calphool/TRS80MXS/eaglecad/modular_expansion_system_graphics_and_sound.board.pdf

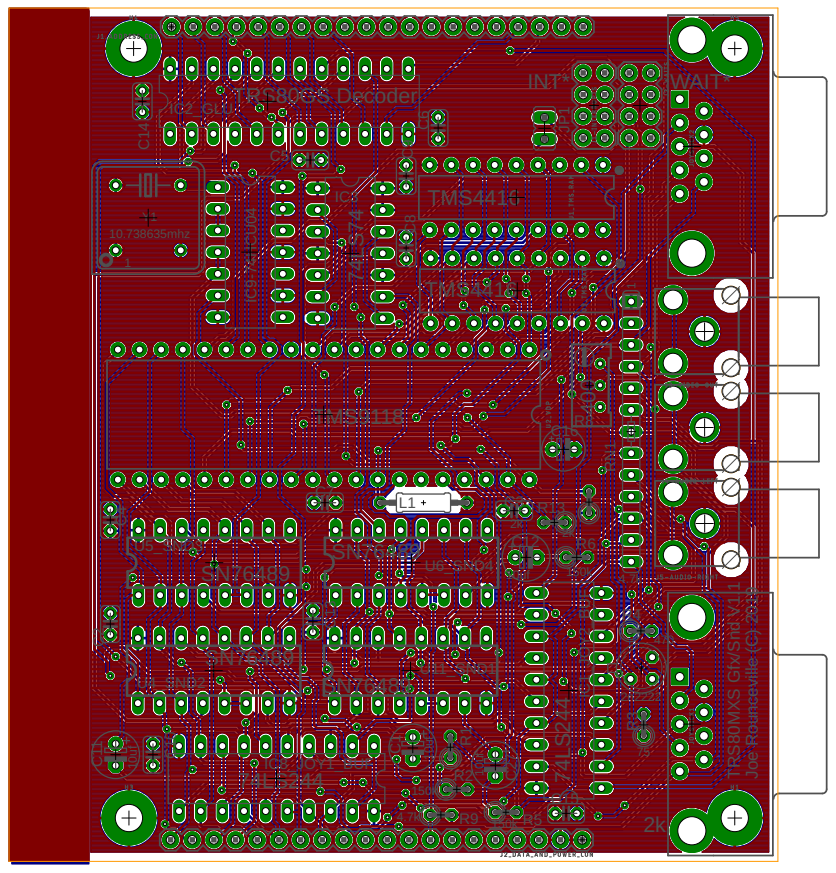
[picture p20: page 1]
