calphool/TRS80MXS/eaglecad/modular_expansion_system_base.board.pdf

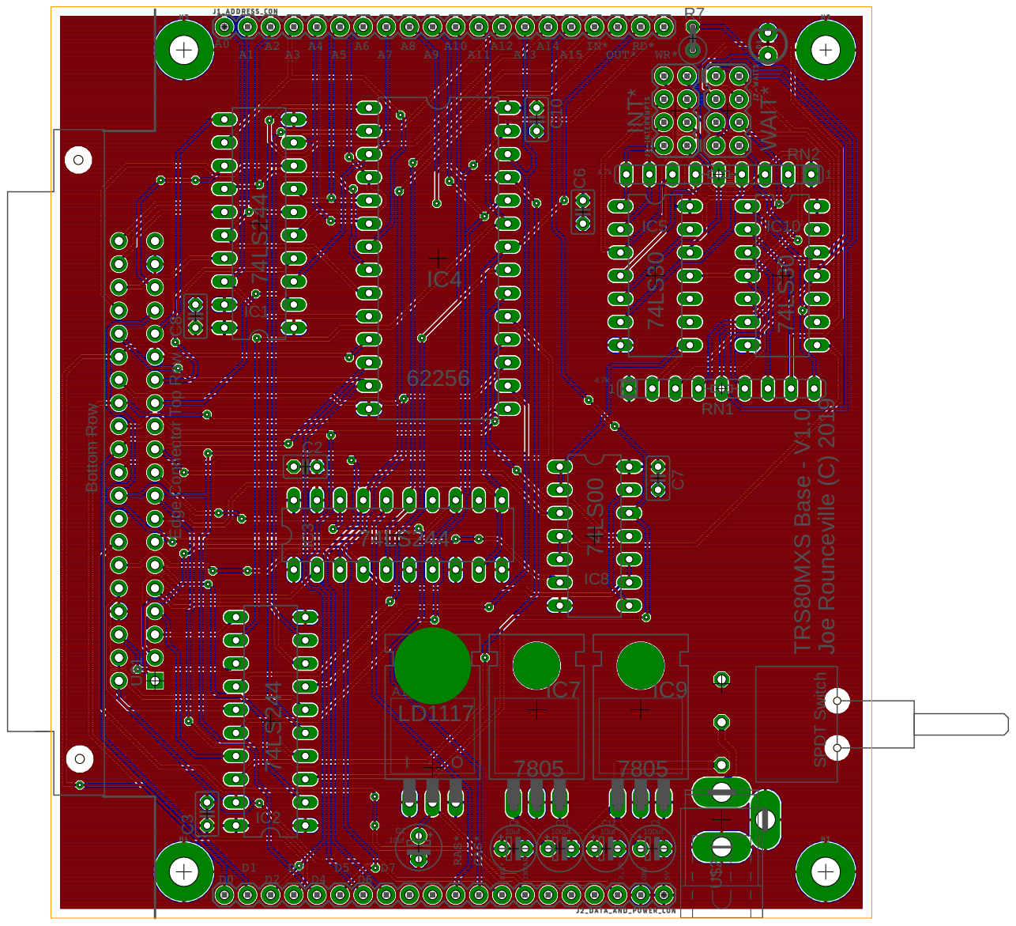
[picture p21: page 1]
