calphool/TRS80MXS/esp32/esp32.ino

#include "defines.h"
#include <WiFi.h>
#include <WiFiClientSecure.h>
#include "esp_task_wdt.h"



char ssid[128];
char password[128];
char server[256];
char inBuffer[256];
char outBuffer[256];
char getBuffer[256];
char headers[4096];
char outstream[8196];

IPAddress ip;
IPAddress subnet;
IPAddress gateway;
char CONNECTING = 0;
char WAITINGFORCONNECT = 0;
char SETTINGCACERT = 0;
char INVOKINGGET = 0;
char RETRIEVINGHEADERS = 0;
char RETRIEVINGSTREAM = 0;
char BUFFERSREADY = 0;

char interruptsAttached = 0;

WiFiClientSecure client;

char dataDirection = 2;


const char* globalsign_ca = \
   "-----BEGIN CERTIFICATE-----\n" \
   "MIIEMjCCAxqgAwIBAgIBATANBgkqhkiG9w0BAQUFADB7MQswCQYDVQQGEwJHQjEb\n" \
   "MBkGA1UECAwSR3JlYXRlciBNYW5jaGVzdGVyMRAwDgYDVQQHDAdTYWxmb3JkMRow\n" \
   "GAYDVQQKDBFDb21vZG8gQ0EgTGltaXRlZDEhMB8GA1UEAwwYQUFBIENlcnRpZmlj\n" \
   "YXRlIFNlcnZpY2VzMB4XDTA0MDEwMTAwMDAwMFoXDTI4MTIzMTIzNTk1OVowezEL\n" \
   "MAkGA1UEBhMCR0IxGzAZBgNVBAgMEkdyZWF0ZXIgTWFuY2hlc3RlcjEQMA4GA1UE\n" \
   "BwwHU2FsZm9yZDEaMBgGA1UECgwRQ29tb2RvIENBIExpbWl0ZWQxITAfBgNVBAMM\n" \
   "GEFBQSBDZXJ0aWZpY2F0ZSBTZXJ2aWNlczCCASIwDQYJKoZIhvcNAQEBBQADggEP\n" \
   "ADCCAQoCggEBAL5AnfRu4ep2hxxNRUSOvkbIgwadwSr+GB+O5AL686tdUIoWMQua\n" \
   "BtDFcCLNSS1UY8y2bmhGC1Pqy0wkwLxyTurxFa70VJoSCsN6sjNg4tqJVfMiWPPe\n" \
   "3M/vg4aijJRPn2jymJBGhCfHdr/jzDUsi14HZGWCwEiwqJH5YZ92IFCokcdmtet4\n" \
   "YgNW8IoaE+oxox6gmf049vYnMlhvB/VruPsUK6+3qszWY19zjNoFmag4qMsXeDZR\n" \
   "rOme9Hg6jc8P2ULimAyrL58OAd7vn5lJ8S3frHRNG5i1R8XlKdH5kBjHYpy+g8cm\n" \
   "ez6KJcfA3Z3mNWgQIJ2P2N7Sw4ScDV7oL8kCAwEAAaOBwDCBvTAdBgNVHQ4EFgQU\n" \
   "oBEKIz6W8Qfs4q8p74Klf9AwpLQwDgYDVR0PAQH/BAQDAgEGMA8GA1UdEwEB/wQF\n" \
   "MAMBAf8wewYDVR0fBHQwcjA4oDagNIYyaHR0cDovL2NybC5jb21vZG9jYS5jb20v\n" \
   "QUFBQ2VydGlmaWNhdGVTZXJ2aWNlcy5jcmwwNqA0oDKGMGh0dHA6Ly9jcmwuY29t\n" \
   "b2RvLm5ldC9BQUFDZXJ0aWZpY2F0ZVNlcnZpY2VzLmNybDANBgkqhkiG9w0BAQUF\n" \
   "AAOCAQEACFb8AvCb6P+k+tZ7xkSAzk/ExfYAWMymtrwUSWgEdujm7l3sAg9g1o1Q\n" \
   "GE8mTgHj5rCl7r+8dFRBv/38ErjHT1r0iWAFf2C3BUrz9vHCv8S5dIa2LX1rzNLz\n" \
   "Rt0vxuBqw8M0Ayx9lt1awg6nCpnBBYurDC/zXDrPbDdVCYfeU0BsWO/8tqtlbgT2\n" \
   "G9w84FoVxp7Z8VlIMCFlA2zs6SFz7JsDoeA3raAVGI/6ugLOpyypEBMs1OUIJqsi\n" \
   "l2D4kF501KKaU73yqWjgom7C12yxow+ev+to51byrvLjKzg6CYG1a4XXvi3tPxq3\n" \
   "smPi9WIsgtRqAEFQ8TmDn5XpNpaYbg==\n" \
   "-----END CERTIFICATE-----\n" \
   "-----BEGIN CERTIFICATE-----\n" \
   "MIIFuzCCA6OgAwIBAgIIVwoRl0LE48wwDQYJKoZIhvcNAQELBQAwazELMAkGA1UE\n" \
   "BhMCSVQxDjAMBgNVBAcMBU1pbGFuMSMwIQYDVQQKDBpBY3RhbGlzIFMucC5BLi8w\n" \
   "MzM1ODUyMDk2NzEnMCUGA1UEAwweQWN0YWxpcyBBdXRoZW50aWNhdGlvbiBSb290\n" \
   "IENBMB4XDTExMDkyMjExMjIwMloXDTMwMDkyMjExMjIwMlowazELMAkGA1UEBhMC\n" \
   "SVQxDjAMBgNVBAcMBU1pbGFuMSMwIQYDVQQKDBpBY3RhbGlzIFMucC5BLi8wMzM1\n" \
   "ODUyMDk2NzEnMCUGA1UEAwweQWN0YWxpcyBBdXRoZW50aWNhdGlvbiBSb290IENB\n" \
   "MIICIjANBgkqhkiG9w0BAQEFAAOCAg8AMIICCgKCAgEAp8bEpSmkLO/lGMWwUKNv\n" \
   "UTufClrJwkg4CsIcoBh/kbWHuUA/3R1oHwiD1S0eiKD4j1aPbZkCkpAW1V8IbInX\n" \
   "4ay8IMKx4INRimlNAJZaby/ARH6jDuSRzVju3PvHHkVH3Se5CAGfpiEd9UEtL0z9\n" \
   "KK3giq0itFZljoZUj5NDKd45RnijMCO6zfB9E1fAXdKDa0hMxKufgFpbOr3JpyI/\n" \
   "gCczWw63igxdBzcIy2zSekciRDXFzMwujt0q7bd9Zg1fYVEiVRvjRuPjPdA1Yprb\n" \
   "rxTIW6HMiRvhMCb8oJsfgadHHwTrozmSBp+Z07/T6k9QnBn+locePGX2oxgkg4YQ\n" \
   "51Q+qDp2JE+BIcXjDwL4k5RHILv+1A7TaLndxHqEguNTVHnd25zS8gebLra8Pu2F\n" \
   "be8lEfKXGkJh90qX6IuxEAf6ZYGyojnP9zz/GPvG8VqLWeICrHuS0E4UT1lF9gxe\n" \
   "KF+w6D9Fz8+vm2/7hNN3WpVvrJSEnu68wEqPSpP4RCHiMUVhUE4Q2OM1fEwZtN4F\n" \
   "v6MGn8i1zeQf1xcGDXqVdFUNaBr8EBtiZJ1t4JWgw5QHVw0U5r0F+7if5t+L4sbn\n" \
   "fpb2U8WANFAoWPASUHEXMLrmeGO89LKtmyuy/uE5jF66CyCU3nuDuP/jVo23Eek7\n" \
   "jPKxwV2dpAtMK9myGPW1n0sCAwEAAaNjMGEwHQYDVR0OBBYEFFLYiDrIn3hm7Ynz\n" \
   "ezhwlMkCAjbQMA8GA1UdEwEB/wQFMAMBAf8wHwYDVR0jBBgwFoAUUtiIOsifeGbt\n" \
   "ifN7OHCUyQICNtAwDgYDVR0PAQH/BAQDAgEGMA0GCSqGSIb3DQEBCwUAA4ICAQAL\n" \
   "e3KHwGCmSUyIWOYdiPcUZEim2FgKDk8TNd81HdTtBjHIgT5q1d07GjLukD0R0i70\n" \
   "jsNjLiNmsGe+b7bAEzlgqqI0JZN1Ut6nna0Oh4lScWoWPBkdg/iaKWW+9D+a2fDz\n" \
   "WochcYBNy+A4mz+7+uAwTc+G02UQGRjRlwKxK3JCaKygvU5a2hi/a5iB0P2avl4V\n" \
   "SM0RFbnAKVy06Ij3Pjaut2L9HmLecHgQHEhb2rykOLpn7VU+Xlff1ANATIGk0k9j\n" \
   "pwlCCRT8AKnCgHNPLsBA2RF7SOp6AsDT6ygBJlh0wcBzIm2Tlf05fbsq4/aC4yyX\n" \
   "X04fkZT6/iyj2HYauE2yOE+b+h1IYHkm4vP9qdCa6HCPSXrW5b0KDtst842/6+Ok\n" \
   "fcvHlXHo2qN8xcL4dJIEG4aspCJTQLas/kx2z/uUMsA1n3Y/buWQbqCmJqK4LL7R\n" \
   "K4X9p2jIugErsWx0Hbhzlefut8cl8ABMALJ+tguLHPPAUJ4lueAI3jZm/zel0btU\n" \
   "ZCzJJ7VLkn5l/9Mt4blOvH+kQSGQQXemOR/qnuOf0GZvBeyqdn6/axag67XH/JJU\n" \
   "LysRJyU3eExRarDzzFhdFPFqSBX/wge2sY0PjlxQRrM9vwGYT7JZVEc+NHt4bVaT\n" \
   "LnPqZih4zR0Uv6CPLy64Lo7yFIrM6bV8+2ydDKXhlg==\n" \
   "-----END CERTIFICATE-----\n" \
   "-----BEGIN CERTIFICATE-----\n" \
   "MIIEGDCCAwCgAwIBAgIBATANBgkqhkiG9w0BAQUFADBlMQswCQYDVQQGEwJTRTEU\n" \
   "MBIGA1UEChMLQWRkVHJ1c3QgQUIxHTAbBgNVBAsTFEFkZFRydXN0IFRUUCBOZXR3\n" \
   "b3JrMSEwHwYDVQQDExhBZGRUcnVzdCBDbGFzcyAxIENBIFJvb3QwHhcNMDAwNTMw\n" \
   "MTAzODMxWhcNMjAwNTMwMTAzODMxWjBlMQswCQYDVQQGEwJTRTEUMBIGA1UEChML\n" \
   "QWRkVHJ1c3QgQUIxHTAbBgNVBAsTFEFkZFRydXN0IFRUUCBOZXR3b3JrMSEwHwYD\n" \
   "VQQDExhBZGRUcnVzdCBDbGFzcyAxIENBIFJvb3QwggEiMA0GCSqGSIb3DQEBAQUA\n" \
   "A4IBDwAwggEKAoIBAQCWltQhSWDia+hBBwzexODcEyPNwTXH+9ZOEQpnXvUGW2ul\n" \
   "CDtbKRY654eyNAbFvAWlA3yCyykQruGIgb3WntP+LVbBFc7jJp0VLhD7Bo8wBN6n\n" \
   "tGO0/7Gcrjyvd7ZWxbWroulpOj0OM3kyP3CCkplhbY0wCI9xP6ZIVxn4JdxLZlyl\n" \
   "dI+Yrsj5wAYi56xz36Uu+1LcsRVlIPo1Zmne3yzxbrww2ywkEtvrNTVokMsAsJch\n" \
   "PXQhI2U0K7t4WaPW4XY5mqRJjox0r26kmqPZm9I4XJuiGMx1I4S+6+JNM3GOGvDC\n" \
   "+Mcdoq0Dlyz4zyXG9rgkMbFjXZJ/Y/AlyVMuH79NAgMBAAGjgdIwgc8wHQYDVR0O\n" \
   "BBYEFJWxtPCUtr3H2tERCSG+wa9J/RB7MAsGA1UdDwQEAwIBBjAPBgNVHRMBAf8E\n" \
   "BTADAQH/MIGPBgNVHSMEgYcwgYSAFJWxtPCUtr3H2tERCSG+wa9J/RB7oWmkZzBl\n" \
   "MQswCQYDVQQGEwJTRTEUMBIGA1UEChMLQWRkVHJ1c3QgQUIxHTAbBgNVBAsTFEFk\n" \
   "ZFRydXN0IFRUUCBOZXR3b3JrMSEwHwYDVQQDExhBZGRUcnVzdCBDbGFzcyAxIENB\n" \
   "IFJvb3SCAQEwDQYJKoZIhvcNAQEFBQADggEBACxtZBsfzQ3duQH6lmM0MkhHma6X\n" \
   "7f1yFqZzR1r0693p9db7RcwpiURdv0Y5PejuvE1Uhh4dbOMXJ0PhiVYrqW9yTkkz\n" \
   "43J8KiOavD7/KCrto/8cI7pDVwlnTUtiBi34/2ydYB7YHEt9tTEv2dB8Xfjea4MY\n" \
   "eDdXL+gzB2ffHsdrKpV2ro9Xo/D0UrSpUwjP4E/TelOL/bscVjby/rK25Xa71SJl\n" \
   "pz/+0WatC7xrmYbvP33zGDLKe8bjq2RGlfgmadlVg3sslgf/WSxEo8bl6ancoWOA\n" \
   "WiFeIc9TVPC6b4nbqKqVz4vjccweGyBECMB6tkD9xOQ14R0WHNC8K47Wcdk=\n" \
   "-----END CERTIFICATE-----\n" \
   "-----BEGIN CERTIFICATE-----\n" \
   "MIIENjCCAx6gAwIBAgIBATANBgkqhkiG9w0BAQUFADBvMQswCQYDVQQGEwJTRTEU\n" \
   "MBIGA1UEChMLQWRkVHJ1c3QgQUIxJjAkBgNVBAsTHUFkZFRydXN0IEV4dGVybmFs\n" \
   "IFRUUCBOZXR3b3JrMSIwIAYDVQQDExlBZGRUcnVzdCBFeHRlcm5hbCBDQSBSb290\n" \
   "MB4XDTAwMDUzMDEwNDgzOFoXDTIwMDUzMDEwNDgzOFowbzELMAkGA1UEBhMCU0Ux\n" \
   "FDASBgNVBAoTC0FkZFRydXN0IEFCMSYwJAYDVQQLEx1BZGRUcnVzdCBFeHRlcm5h\n" \
   "bCBUVFAgTmV0d29yazEiMCAGA1UEAxMZQWRkVHJ1c3QgRXh0ZXJuYWwgQ0EgUm9v\n" \
   "dDCCASIwDQYJKoZIhvcNAQEBBQADggEPADCCAQoCggEBALf3GjPm8gAELTngTlvt\n" \
   "H7xsD821+iO2zt6bETOXpClMfZOfvUq8k+0DGuOPz+VtUFrWlymUWoCwSXrbLpX9\n" \
   "uMq/NzgtHj6RQa1wVsfwTz/oMp50ysiQVOnGXw94nZpAPA6sYapeFI+eh6FqUNzX\n" \
   "mk6vBbOmcZSccbNQYArHE504B4YCqOmoaSYYkKtMsE8jqzpPhNjfzp/haW+710LX\n" \
   "a0Tkx63ubUFfclpxCDezeWWkWaCUN/cALw3CknLa0Dhy2xSoRcRdKn23tNbE7qzN\n" \
   "E0S3ySvdQwAl+mG5aWpYIxG3pzOPVnVZ9c0p10a3CitlttNCbxWyuHv77+ldU9U0\n" \
   "WicCAwEAAaOB3DCB2TAdBgNVHQ4EFgQUrb2YejS0Jvf6xCZU7wO94CTLVBowCwYD\n" \
   "VR0PBAQDAgEGMA8GA1UdEwEB/wQFMAMBAf8wgZkGA1UdIwSBkTCBjoAUrb2YejS0\n" \
   "Jvf6xCZU7wO94CTLVBqhc6RxMG8xCzAJBgNVBAYTAlNFMRQwEgYDVQQKEwtBZGRU\n" \
   "cnVzdCBBQjEmMCQGA1UECxMdQWRkVHJ1c3QgRXh0ZXJuYWwgVFRQIE5ldHdvcmsx\n" \
   "IjAgBgNVBAMTGUFkZFRydXN0IEV4dGVybmFsIENBIFJvb3SCAQEwDQYJKoZIhvcN\n" \
   "AQEFBQADggEBALCb4IUlwtYj4g+WBpKdQZic2YR5gdkeWxQHIzZlj7DYd7usQWxH\n" \
   "YINRsPkyPef89iYTx4AWpb9a/IfPeHmJIZriTAcKhjW88t5RxNKWt9x+Tu5w/Rw5\n" \
   "6wwCURQtjr0W4MHfRnXnJK3s9EK0hZNwEGe6nQY1ShjTK3rMUUKhemPR5ruhxSvC\n" \
   "Nr4TDea9Y355e6cJDUCrat2PisP29owaQgVR1EX1n6diIWgVIEM8med8vSTYqZEX\n" \
   "c4g/VhsxOBi0cQ+azcgOno4uG+GMmIPLHzHxREzGBHNJdmAPx/i9F4BrLunMTA5a\n" \
   "mnkPIAou1Z5jJh5VkpTYghdae9C8x49OhgQ=\n" \
   "-----END CERTIFICATE-----\n" \
   "-----BEGIN CERTIFICATE-----\n" \
   "MIIFVTCCBD2gAwIBAgIEO/OB0DANBgkqhkiG9w0BAQUFADBsMQswCQYDVQQGEwJj\n" \
   "aDEOMAwGA1UEChMFYWRtaW4xETAPBgNVBAsTCFNlcnZpY2VzMSIwIAYDVQQLExlD\n" \
   "ZXJ0aWZpY2F0aW9uIEF1dGhvcml0aWVzMRYwFAYDVQQDEw1BZG1pbi1Sb290LUNB\n" \
   "MB4XDTAxMTExNTA4NTEwN1oXDTIxMTExMDA3NTEwN1owbDELMAkGA1UEBhMCY2gx\n" \
   "DjAMBgNVBAoTBWFkbWluMREwDwYDVQQLEwhTZXJ2aWNlczEiMCAGA1UECxMZQ2Vy\n" \
   "dGlmaWNhdGlvbiBBdXRob3JpdGllczEWMBQGA1UEAxMNQWRtaW4tUm9vdC1DQTCC\n" \
   "ASIwDQYJKoZIhvcNAQEBBQADggEPADCCAQoCggEBAMvgr0QUIv5qF0nyXZ3PXAJi\n" \
   "C4C5Wr+oVTN7oxIkXkxvO0GJToM9n7OVJjSmzBL0zJ2HXj0MDRcvhSY+KiZZc6Go\n" \
   "vDvr5Ua481l7ILFeQAFtumeza+vvxeL5Nd0Maga2miiacLNAKXbAcUYRa0Ov5VZB\n" \
   "++YcOYNNt/aisWbJqA2y8He+NsEgJzK5zNdayvYXQTZN+7tVgWOck16Da3+4FXdy\n" \
   "fH1NCWtZlebtMKtERtkVAaVbiWW24CjZKAiVfggjsiLo3yVMPGj3budLx5D9hEEm\n" \
   "vlyDOtcjebca+AcZglppWMX/iHIrx7740y0zd6cWEqiLIcZCrnpkr/KzwO135GkC\n" \
   "AwEAAaOCAf0wggH5MA8GA1UdEwEB/wQFMAMBAf8wgZkGA1UdIASBkTCBjjCBiwYI\n" \
   "YIV0AREDAQAwfzArBggrBgEFBQcCAjAfGh1UaGlzIGlzIHRoZSBBZG1pbi1Sb290\n" \
   "LUNBIENQUzBQBggrBgEFBQcCARZEaHR0cDovL3d3dy5pbmZvcm1hdGlrLmFkbWlu\n" \
   "LmNoL1BLSS9saW5rcy9DUFNfMl8xNl83NTZfMV8xN18zXzFfMC5wZGYwfwYDVR0f\n" \
   "BHgwdjB0oHKgcKRuMGwxFjAUBgNVBAMTDUFkbWluLVJvb3QtQ0ExIjAgBgNVBAsT\n" \
   "GUNlcnRpZmljYXRpb24gQXV0aG9yaXRpZXMxETAPBgNVBAsTCFNlcnZpY2VzMQ4w\n" \
   "DAYDVQQKEwVhZG1pbjELMAkGA1UEBhMCY2gwHQYDVR0OBBYEFIKf+iNzIPGXi7JM\n" \
   "Tb5CxX9mzWToMIGZBgNVHSMEgZEwgY6AFIKf+iNzIPGXi7JMTb5CxX9mzWTooXCk\n" \
   "bjBsMQswCQYDVQQGEwJjaDEOMAwGA1UEChMFYWRtaW4xETAPBgNVBAsTCFNlcnZp\n" \
   "Y2VzMSIwIAYDVQQLExlDZXJ0aWZpY2F0aW9uIEF1dGhvcml0aWVzMRYwFAYDVQQD\n" \
   "Ew1BZG1pbi1Sb290LUNBggQ784HQMA4GA1UdDwEB/wQEAwIBBjANBgkqhkiG9w0B\n" \
   "AQUFAAOCAQEAeE96XCYRpy6umkPKXDWCRn7INo96ZrWpMggcDORuofHIwdTkgOeM\n" \
   "vWOxDN/yuT7CC3FAaUajbPRbDw0hRMcqKz0aC8CgwcyIyhw/rFK29mfNTG3EviP9\n" \
   "QSsEbnelFnjpm1wjz4EaBiFjatwpUbI6+Zv3XbEt9QQXBn+c6DeFLe4xvC4B+MTr\n" \
   "a440xTk59pSYux8OHhEvqIwHCkiijGqZhTS3KmGFeBopaR+dJVBRBMoXwzk4B3Hn\n" \
   "0Zib1dEYFZa84vPJZyvxCbLOnPRDJgH6V2uQqbG+6DXVaf/wORVOvF/wzzv0viM/\n" \
   "RWbEtJZdvo8N3sdtCULzifnxP/V0T9+4ZQ==\n" \
   "-----END CERTIFICATE-----\n" \
   "-----BEGIN CERTIFICATE-----\n" \
   "MIIDTDCCAjSgAwIBAgIId3cGJyapsXwwDQYJKoZIhvcNAQELBQAwRDELMAkGA1UE\n" \
   "BhMCVVMxFDASBgNVBAoMC0FmZmlybVRydXN0MR8wHQYDVQQDDBZBZmZpcm1UcnVz\n" \
   "dCBDb21tZXJjaWFsMB4XDTEwMDEyOTE0MDYwNloXDTMwMTIzMTE0MDYwNlowRDEL\n" \
   "MAkGA1UEBhMCVVMxFDASBgNVBAoMC0FmZmlybVRydXN0MR8wHQYDVQQDDBZBZmZp\n" \
   "cm1UcnVzdCBDb21tZXJjaWFsMIIBIjANBgkqhkiG9w0BAQEFAAOCAQ8AMIIBCgKC\n" \
   "AQEA9htPZwcroRX1BiLLHwGy43NFBkRJLLtJJRTWzsO3qyxPxkEylFf6EqdbDuKP\n" \
   "Hx6GGaeqtS25Xw2Kwq+FNXkyLbscYjfysVtKPcrNcV/pQr6U6Mje+SJIZMblq8Yr\n" \
   "ba0F8PrVC8+a5fBQpIs7R6UjW3p6+DM/uO+Zl+MgwdYoic+U+7lF7eNAFxHUdPAL\n" \
   "MeIrJmqbTFeurCA+ukV6BfO9m2kVrn1OIGPENXY6BwLJN/3HR+7o8XYdcxXyl6S1\n" \
   "yHp52UKqK39c/s4mT6NmgTWvRLpUHhwwMmWd5jyTXlBOeuM61G7MGvv50jeuJCqr\n" \
   "VwMiKA1JdX+3KNp1v47j3A55MQIDAQABo0IwQDAdBgNVHQ4EFgQUnZPGU4teyq8/\n" \
   "nx4P5ZmVvCT2lI8wDwYDVR0TAQH/BAUwAwEB/zAOBgNVHQ8BAf8EBAMCAQYwDQYJ\n" \
   "KoZIhvcNAQELBQADggEBAFis9AQOzcAN/wr91LoWXym9e2iZWEnStB03TX8nfUYG\n" \
   "XUPGhi4+c7ImfU+TqbbEKpqrIZcUsd6M06uJFdhrJNTxFq7YpFzUf1GO7RgBsZNj\n" \
   "vbz4YYCanrHOQnDiqX0GJX0nof5v7LMeJNrjS1UaADs1tDvZ110w/YETifLCBivt\n" \
   "Z8SOyUOyXGsViQK8YvxO8rUzqrJv0wqiUOP2O+guRMLbZjipM1ZI8W0bM40NjD9g\n" \
   "N53Tym1+NH4Nn3J2ixufcv1SNUFFApYvHLKac0khsUlHRUe072o0EclNmsxZt9YC\n" \
   "nlpOZbWUrhvfKbAW8b8Angc6F2S1BLUjIZkKlTuXfO8=\n" \
   "-----END CERTIFICATE-----\n" \
   "-----BEGIN CERTIFICATE-----\n" \
   "MIIDTDCCAjSgAwIBAgIIfE8EORzUmS0wDQYJKoZIhvcNAQEFBQAwRDELMAkGA1UE\n" \
   "BhMCVVMxFDASBgNVBAoMC0FmZmlybVRydXN0MR8wHQYDVQQDDBZBZmZpcm1UcnVz\n" \
   "dCBOZXR3b3JraW5nMB4XDTEwMDEyOTE0MDgyNFoXDTMwMTIzMTE0MDgyNFowRDEL\n" \
   "MAkGA1UEBhMCVVMxFDASBgNVBAoMC0FmZmlybVRydXN0MR8wHQYDVQQDDBZBZmZp\n" \
   "cm1UcnVzdCBOZXR3b3JraW5nMIIBIjANBgkqhkiG9w0BAQEFAAOCAQ8AMIIBCgKC\n" \
   "AQEAtITMMxcua5Rsa2FSoOujz3mUTOWUgJnLVWREZY9nZOIG41w3SfYvm4SEHi3y\n" \
   "YJ0wTsyEheIszx6e/jarM3c1RNg1lho9Nuh6DtjVR6FqaYvZ/Ls6rnla1fTWcbua\n" \
   "kCNrmreIdIcMHl+5ni36q1Mr3Lt2PpNMCAiMHqIjHNRqrSK6mQEubWXLviRmVSRL\n" \
   "QESxG9fhwoXA3hA/Pe24/PHxI1Pcv2WXb9n5QHGNfb2V1M6+oF4nI979ptAmDgAp\n" \
   "6zxG8D1gvz9Q0twmQVGeFDdCBKNwV6gbh+0t+nvujArjqWaJGctB+d1ENmHP4ndG\n" \
   "yH329JKBNv3bNPFyfvMMFr20FQIDAQABo0IwQDAdBgNVHQ4EFgQUBx/S55zawm6i\n" \
   "QLSwelAQUHTEyL0wDwYDVR0TAQH/BAUwAwEB/zAOBgNVHQ8BAf8EBAMCAQYwDQYJ\n" \
   "KoZIhvcNAQEFBQADggEBAIlXshZ6qML91tmbmzTCnLQyFE2npN/svqe++EPbkTfO\n" \
   "tDIuUFUaNU52Q3Eg75N3ThVwLofDwR1t3Mu1J9QsVtFSUzpE0nPIxBsFZVpikpzu\n" \
   "QY0x2+c06lkh1QF612S4ZDnNye2v7UsDSKegmQGA3GWjNq5lWUhPgkvIZfFXHeVZ\n" \
   "Lgo/bNjR9eUJtGxUAArgFU2HdW23WJZa3W3SAKD0m0i+wzekujbgfIeFlxoVot4u\n" \
   "olu9rxj5kFDNcFn4J2dHy8egBzp90SxdbBk6ZrV9/ZFvgrG+CJPbFEfxojfHRZ48\n" \
   "x3evZKiT3/Zpg4Jg8klCNO1aAFSFHBY2kgxc+qatv9s=\n" \
   "-----END CERTIFICATE-----\n" \
   "-----BEGIN CERTIFICATE-----\n" \
   "MIIFRjCCAy6gAwIBAgIIbYwURrGmCu4wDQYJKoZIhvcNAQEMBQAwQTELMAkGA1UE\n" \
   "BhMCVVMxFDASBgNVBAoMC0FmZmlybVRydXN0MRwwGgYDVQQDDBNBZmZpcm1UcnVz\n" \
   "dCBQcmVtaXVtMB4XDTEwMDEyOTE0MTAzNloXDTQwMTIzMTE0MTAzNlowQTELMAkG\n" \
   "A1UEBhMCVVMxFDASBgNVBAoMC0FmZmlybVRydXN0MRwwGgYDVQQDDBNBZmZpcm1U\n" \
   "cnVzdCBQcmVtaXVtMIICIjANBgkqhkiG9w0BAQEFAAOCAg8AMIICCgKCAgEAxBLf\n" \
   "qV/+Qd3d9Z+K4/as4Tx4mrzY8H96oDMq3I0gW64tb+eT2TZwamjPjlGjhVtnBKAQ\n" \
   "JG9dKILBl1fYSCkTtuG+kU3fhQxTGJoeJKJPj/CihQvL9Cl/0qRY7iZNyaqoe5rZ\n" \
   "+jjeRFcV5fiMyNlI4g0WJx0eyIOFJbe6qlVBzAMiSy2RjYvmia9mx+n/K+k8rNrS\n" \
   "s8PhaJyJ+HoAVt70VZVs+7pk3WKL3wt3MutizCaam7uqYoNMtAZ6MMgpv+0GTZe5\n" \
   "HMQxK9VfvFMSF5yZVylmd2EhMQcuJUmdGPLu8ytxjLW6OQdJd/zvLpKQBY0tL3d7\n" \
   "70O/Nbua2Plzpyzy0FfuKE4mX4+QaAkvuPjcBukumj5Rp9EixAqnOEhss/n/fauG\n" \
   "V+O61oV4d7pD6kh/9ti+I20ev9E2bFhc8e6kGVQa9QPSdubhjL08s9NIS+LI+H+S\n" \
   "qHZGnEJlPqQewQcDWkYtuJfzt9WyVSHvutxMAJf7FJUnM7/oQ0dG0giZFmA7mn7S\n" \
   "5u046uwBHjxIVkkJx0w3AJ6IDsBz4W9m6XJHMD4Q5QsDyZpCAGzFlH5hxIrff4Ia\n" \
   "C1nEWTJ3s7xgaVY5/bQGeyzWZDbZvUjthB9+pSKPKrhC9IK31FOQeE4tGv2Bb0TX\n" \
   "OwF0lkLgAOIua+rF7nKsu7/+6qqo+Nz2snmKtmcCAwEAAaNCMEAwHQYDVR0OBBYE\n" \
   "FJ3AZ6YMItkm9UWrpmVSESfYRaxjMA8GA1UdEwEB/wQFMAMBAf8wDgYDVR0PAQH/\n" \
   "BAQDAgEGMA0GCSqGSIb3DQEBDAUAA4ICAQCzV00QYk465KzquByvMiPIs0laUZx2\n" \
   "KI15qldGF9X1Uva3ROgIRL8YhNILgM3FEv0AVQVhh0HctSSePMTYyPtwni94loMg\n" \
   "Nt58D2kTiKV1NpgIpsbfrM7jWNa3Pt668+s0QNiigfV4Py/VpfzZotReBA4Xrf5B\n" \
   "8OWycvpEgjNC6C1Y91aMYj+6QrCcDFx+LmUmXFNPALJ4fqENmS2NuB2OosSw/WDQ\n" \
   "MKSOyARiqcTtNd56l+0OOF6SL5Nwpamcb6d9Ex1+xghIsV5n61EIJenmJWtSKZGc\n" \
   "0jlzCFfemQa0W50QBuHCAKi4HEoCChTQwUHK+4w1IX2COPKpVJEZNZOUbWo6xbLQ\n" \
   "u4mGk+ibyQ86p3q4ofB4Rvr8Ny/lioTz3/4E2aFooC8k4gmVBtWVyuEklut89pMF\n" \
   "u+1z6S3RdTnX5yTb2E5fQ4+e0BQ5v1VwSJlXMbSc7kqYA5YwH2AG7hsj/oFgIxpH\n" \
   "YoWlzBk0gG+zrBrjn/B7SK3VAdlntqlyk+otZrWyuOQ9PLLvTIzq6we/qzWaVYa8\n" \
   "GKa1qF60g2xraUDTn9zxw2lrueFtCfTxqlB2Cnp9ehehVZZCmTEJ3WARjQUwfuaO\n" \
   "RtGdFNrHF+QFlozEJLUbzxQHskD4o55BhrwE0GuWyCqANP2/7waj3VjFhT0+j/6e\n" \
   "KeC2uAloGRwYQw==\n" \
   "-----END CERTIFICATE-----\n" \
   "-----BEGIN CERTIFICATE-----\n" \
   "MIIB/jCCAYWgAwIBAgIIdJclisc/elQwCgYIKoZIzj0EAwMwRTELMAkGA1UEBhMC\n" \
   "VVMxFDASBgNVBAoMC0FmZmlybVRydXN0MSAwHgYDVQQDDBdBZmZpcm1UcnVzdCBQ\n" \
   "cmVtaXVtIEVDQzAeFw0xMDAxMjkxNDIwMjRaFw00MDEyMzExNDIwMjRaMEUxCzAJ\n" \
   "BgNVBAYTAlVTMRQwEgYDVQQKDAtBZmZpcm1UcnVzdDEgMB4GA1UEAwwXQWZmaXJt\n" \
   "VHJ1c3QgUHJlbWl1bSBFQ0MwdjAQBgcqhkjOPQIBBgUrgQQAIgNiAAQNMF4bFZ0D\n" \
   "0KF5Nbc6PJJ6yhUczWLznCZcBz3lVPqj1swS6vQUX+iOGasvLkjmrBhDeKzQN8O9\n" \
   "ss0s5kfiGuZjuD0uL3jET9v0D6RoTFVya5UdThhClXjMNzyR4ptlKymjQjBAMB0G\n" \
   "A1UdDgQWBBSaryl6wBE1NSZRMADDav5A1a7WPDAPBgNVHRMBAf8EBTADAQH/MA4G\n" \
   "A1UdDwEB/wQEAwIBBjAKBggqhkjOPQQDAwNnADBkAjAXCfOHiFBar8jAQr9HX/Vs\n" \
   "aobgxCd05DhT1wV/GzTjxi+zygk8N53X57hG8f2h4nECMEJZh0PUUd+60wkyWs6I\n" \
   "flc9nF9Ca/UHLbXwgpP5WW+uZPpY5Yse42O+tYHNbwKMeQ==\n" \
   "-----END CERTIFICATE-----\n" \
   "-----BEGIN CERTIFICATE-----\n" \
   "MIIDQTCCAimgAwIBAgITBmyfz5m/jAo54vB4ikPmljZbyjANBgkqhkiG9w0BAQsF\n" \
   "ADA5MQswCQYDVQQGEwJVUzEPMA0GA1UEChMGQW1hem9uMRkwFwYDVQQDExBBbWF6\n" \
   "b24gUm9vdCBDQSAxMB4XDTE1MDUyNjAwMDAwMFoXDTM4MDExNzAwMDAwMFowOTEL\n" \
   "MAkGA1UEBhMCVVMxDzANBgNVBAoTBkFtYXpvbjEZMBcGA1UEAxMQQW1hem9uIFJv\n" \
   "b3QgQ0EgMTCCASIwDQYJKoZIhvcNAQEBBQADggEPADCCAQoCggEBALJ4gHHKeNXj\n" \
   "ca9HgFB0fW7Y14h29Jlo91ghYPl0hAEvrAIthtOgQ3pOsqTQNroBvo3bSMgHFzZM\n" \
   "9O6II8c+6zf1tRn4SWiw3te5djgdYZ6k/oI2peVKVuRF4fn9tBb6dNqcmzU5L/qw\n" \
   "IFAGbHrQgLKm+a/sRxmPUDgH3KKHOVj4utWp+UhnMJbulHheb4mjUcAwhmahRWa6\n" \
   "VOujw5H5SNz/0egwLX0tdHA114gk957EWW67c4cX8jJGKLhD+rcdqsq08p8kDi1L\n" \
   "93FcXmn/6pUCyziKrlA4b9v7LWIbxcceVOF34GfID5yHI9Y/QCB/IIDEgEw+OyQm\n" \
   "jgSubJrIqg0CAwEAAaNCMEAwDwYDVR0TAQH/BAUwAwEB/zAOBgNVHQ8BAf8EBAMC\n" \
   "AYYwHQYDVR0OBBYEFIQYzIU07LwMlJQuCFmcx7IQTgoIMA0GCSqGSIb3DQEBCwUA\n" \
   "A4IBAQCY8jdaQZChGsV2USggNiMOruYou6r4lK5IpDB/G/wkjUu0yKGX9rbxenDI\n" \
   "U5PMCCjjmCXPI6T53iHTfIUJrU6adTrCC2qJeHZERxhlbI1Bjjt/msv0tadQ1wUs\n" \
   "N+gDS63pYaACbvXy8MWy7Vu33PqUXHeeE6V/Uq2V8viTO96LXFvKWlJbYK8U90vv\n" \
   "o/ufQJVtMVT8QtPHRh8jrdkPSHCa2XV4cdFyQzR1bldZwgJcJmApzyMZFo6IQ6XU\n" \
   "5MsI+yMRQ+hDKXJioaldXgjUkK642M4UwtBV8ob2xJNDd2ZhwLnoQdeXeGADbkpy\n" \
   "rqXRfboQnoZsG4q5WTP468SQvvG5\n" \
   "-----END CERTIFICATE-----\n" \
   "-----BEGIN CERTIFICATE-----\n" \
   "MIIFQTCCAymgAwIBAgITBmyf0pY1hp8KD+WGePhbJruKNzANBgkqhkiG9w0BAQwF\n" \
   "ADA5MQswCQYDVQQGEwJVUzEPMA0GA1UEChMGQW1hem9uMRkwFwYDVQQDExBBbWF6\n" \
   "b24gUm9vdCBDQSAyMB4XDTE1MDUyNjAwMDAwMFoXDTQwMDUyNjAwMDAwMFowOTEL\n" \
   "MAkGA1UEBhMCVVMxDzANBgNVBAoTBkFtYXpvbjEZMBcGA1UEAxMQQW1hem9uIFJv\n" \
   "b3QgQ0EgMjCCAiIwDQYJKoZIhvcNAQEBBQADggIPADCCAgoCggIBAK2Wny2cSkxK\n" \
   "gXlRmeyKy2tgURO8TW0G/LAIjd0ZEGrHJgw12MBvIITplLGbhQPDW9tK6Mj4kHbZ\n" \
   "W0/jTOgGNk3Mmqw9DJArktQGGWCsN0R5hYGCrVo34A3MnaZMUnbqQ523BNFQ9lXg\n" \
   "1dKmSYXpN+nKfq5clU1Imj+uIFptiJXZNLhSGkOQsL9sBbm2eLfq0OQ6PBJTYv9K\n" \
   "8nu+NQWpEjTj82R0Yiw9AElaKP4yRLuH3WUnAnE72kr3H9rN9yFVkE8P7K6C4Z9r\n" \
   "2UXTu/Bfh+08LDmG2j/e7HJV63mjrdvdfLC6HM783k81ds8P+HgfajZRRidhW+me\n" \
   "z/CiVX18JYpvL7TFz4QuK/0NURBs+18bvBt+xa47mAExkv8LV/SasrlX6avvDXbR\n" \
   "8O70zoan4G7ptGmh32n2M8ZpLpcTnqWHsFcQgTfJU7O7f/aS0ZzQGPSSbtqDT6Zj\n" \
   "mUyl+17vIWR6IF9sZIUVyzfpYgwLKhbcAS4y2j5L9Z469hdAlO+ekQiG+r5jqFoz\n" \
   "7Mt0Q5X5bGlSNscpb/xVA1wf+5+9R+vnSUeVC06JIglJ4PVhHvG/LopyboBZ/1c6\n" \
   "+XUyo05f7O0oYtlNc/LMgRdg7c3r3NunysV+Ar3yVAhU/bQtCSwXVEqY0VThUWcI\n" \
   "0u1ufm8/0i2BWSlmy5A5lREedCf+3euvAgMBAAGjQjBAMA8GA1UdEwEB/wQFMAMB\n" \
   "Af8wDgYDVR0PAQH/BAQDAgGGMB0GA1UdDgQWBBSwDPBMMPQFWAJI/TPlUq9LhONm\n" \
   "UjANBgkqhkiG9w0BAQwFAAOCAgEAqqiAjw54o+Ci1M3m9Zh6O+oAA7CXDpO8Wqj2\n" \
   "LIxyh6mx/H9z/WNxeKWHWc8w4Q0QshNabYL1auaAn6AFC2jkR2vHat+2/XcycuUY\n" \
   "+gn0oJMsXdKMdYV2ZZAMA3m3MSNjrXiDCYZohMr/+c8mmpJ5581LxedhpxfL86kS\n" \
   "k5Nrp+gvU5LEYFiwzAJRGFuFjWJZY7attN6a+yb3ACfAXVU3dJnJUH/jWS5E4ywl\n" \
   "7uxMMne0nxrpS10gxdr9HIcWxkPo1LsmmkVwXqkLN1PiRnsn/eBG8om3zEK2yygm\n" \
   "btmlyTrIQRNg91CMFa6ybRoVGld45pIq2WWQgj9sAq+uEjonljYE1x2igGOpm/Hl\n" \
   "urR8FLBOybEfdF849lHqm/osohHUqS0nGkWxr7JOcQ3AWEbWaQbLU8uz/mtBzUF+\n" \
   "fUwPfHJ5elnNXkoOrJupmHN5fLT0zLm4BwyydFy4x2+IoZCn9Kr5v2c69BoVYh63\n" \
   "n749sSmvZ6ES8lgQGVMDMBu4Gon2nL2XA46jCfMdiyHxtN/kHNGfZQIG6lzWE7OE\n" \
   "76KlXIx3KadowGuuQNKotOrN8I1LOJwZmhsoVLiJkO/KdYE+HvJkJMcYr07/R54H\n" \
   "9jVlpNMKVv/1F2Rs76giJUmTtt8AF9pYfl3uxRuw0dFfIRDH+fO6AgonB8Xx1sfT\n" \
   "4PsJYGw=\n" \
   "-----END CERTIFICATE-----\n" \
   "-----BEGIN CERTIFICATE-----\n" \
   "MIIBtjCCAVugAwIBAgITBmyf1XSXNmY/Owua2eiedgPySjAKBggqhkjOPQQDAjA5\n" \
   "MQswCQYDVQQGEwJVUzEPMA0GA1UEChMGQW1hem9uMRkwFwYDVQQDExBBbWF6b24g\n" \
   "Um9vdCBDQSAzMB4XDTE1MDUyNjAwMDAwMFoXDTQwMDUyNjAwMDAwMFowOTELMAkG\n" \
   "A1UEBhMCVVMxDzANBgNVBAoTBkFtYXpvbjEZMBcGA1UEAxMQQW1hem9uIFJvb3Qg\n" \
   "Q0EgMzBZMBMGByqGSM49AgEGCCqGSM49AwEHA0IABCmXp8ZBf8ANm+gBG1bG8lKl\n" \
   "ui2yEujSLtf6ycXYqm0fc4E7O5hrOXwzpcVOho6AF2hiRVd9RFgdszflZwjrZt6j\n" \
   "QjBAMA8GA1UdEwEB/wQFMAMBAf8wDgYDVR0PAQH/BAQDAgGGMB0GA1UdDgQWBBSr\n" \
   "ttvXBp43rDCGB5Fwx5zEGbF4wDAKBggqhkjOPQQDAgNJADBGAiEA4IWSoxe3jfkr\n" \
   "BqWTrBqYaGFy+uGh0PsceGCmQ5nFuMQCIQCcAu/xlJyzlvnrxir4tiz+OpAUFteM\n" \
   "YyRIHN8wfdVoOw==\n" \
   "-----END CERTIFICATE-----\n" \
   "-----BEGIN CERTIFICATE-----\n" \
   "MIIB8jCCAXigAwIBAgITBmyf18G7EEwpQ+Vxe3ssyBrBDjAKBggqhkjOPQQDAzA5\n" \
   "MQswCQYDVQQGEwJVUzEPMA0GA1UEChMGQW1hem9uMRkwFwYDVQQDExBBbWF6b24g\n" \
   "Um9vdCBDQSA0MB4XDTE1MDUyNjAwMDAwMFoXDTQwMDUyNjAwMDAwMFowOTELMAkG\n" \
   "A1UEBhMCVVMxDzANBgNVBAoTBkFtYXpvbjEZMBcGA1UEAxMQQW1hem9uIFJvb3Qg\n" \
   "Q0EgNDB2MBAGByqGSM49AgEGBSuBBAAiA2IABNKrijdPo1MN/sGKe0uoe0ZLY7Bi\n" \
   "9i0b2whxIdIA6GO9mif78DluXeo9pcmBqqNbIJhFXRbb/egQbeOc4OO9X4Ri83Bk\n" \
   "M6DLJC9wuoihKqB1+IGuYgbEgds5bimwHvouXKNCMEAwDwYDVR0TAQH/BAUwAwEB\n" \
   "/zAOBgNVHQ8BAf8EBAMCAYYwHQYDVR0OBBYEFNPsxzplbszh2naaVvuc84ZtV+WB\n" \
   "MAoGCCqGSM49BAMDA2gAMGUCMDqLIfG9fhGt0O9Yli/W651+kI0rz2ZVwyzjKKlw\n" \
   "CkcO8DdZEv8tmZQoTipPNU0zWgIxAOp1AE47xDqUEpHJWEadIRNyp4iciuRMStuW\n" \
   "1KyLa2tJElMzrdfkviT8tQp21KW8EA==\n" \
   "-----END CERTIFICATE-----\n" \
   "-----BEGIN CERTIFICATE-----\n" \
   "MIIIGDCCBgCgAwIBAgIGAT8vMXfmMA0GCSqGSIb3DQEBCwUAMIIBCjELMAkGA1UE\n" \
   "BhMCRVMxEjAQBgNVBAgMCUJhcmNlbG9uYTFYMFYGA1UEBwxPQmFyY2Vsb25hIChz\n" \
   "ZWUgY3VycmVudCBhZGRyZXNzIGF0IGh0dHA6Ly93d3cuYW5mLmVzL2VzL2FkZHJl\n" \
   "c3MtZGlyZWNjaW9uLmh0bWwgKTEnMCUGA1UECgweQU5GIEF1dG9yaWRhZCBkZSBD\n" \
   "ZXJ0aWZpY2FjaW9uMRcwFQYDVQQLDA5BTkYgQ2xhc2UgMSBDQTEaMBgGCSqGSIb3\n" \
   "DQEJARYLaW5mb0BhbmYuZXMxEjAQBgNVBAUTCUc2MzI4NzUxMDEbMBkGA1UEAwwS\n" \
   "QU5GIEdsb2JhbCBSb290IENBMB4XDTEzMDYxMDE3NDUzOFoXDTMzMDYwNTE3NDUz\n" \
   "OFowggEKMQswCQYDVQQGEwJFUzESMBAGA1UECAwJQmFyY2Vsb25hMVgwVgYDVQQH\n" \
   "DE9CYXJjZWxvbmEgKHNlZSBjdXJyZW50IGFkZHJlc3MgYXQgaHR0cDovL3d3dy5h\n" \
   "bmYuZXMvZXMvYWRkcmVzcy1kaXJlY2Npb24uaHRtbCApMScwJQYDVQQKDB5BTkYg\n" \
   "QXV0b3JpZGFkIGRlIENlcnRpZmljYWNpb24xFzAVBgNVBAsMDkFORiBDbGFzZSAx\n" \
   "IENBMRowGAYJKoZIhvcNAQkBFgtpbmZvQGFuZi5lczESMBAGA1UEBRMJRzYzMjg3\n" \
   "NTEwMRswGQYDVQQDDBJBTkYgR2xvYmFsIFJvb3QgQ0EwggIiMA0GCSqGSIb3DQEB\n" \
   "AQUAA4ICDwAwggIKAoICAQDHPi9xy4wynbcUbWjorVUgQKeUAVh937J7P37XmsfH\n" \
   "ZLOBZKIIlhhCtRwnDlg7x+BUvtJOTkIbEGMujDygUQ2s3HDYr5I41hTyM2Pl0cq2\n" \
   "EuSGEbPIHb3dEX8NAguFexM0jqNjrreN3hM2/+TOkAxSdDJP2aMurlySC5zwl47K\n" \
   "ZLHtcVrkZnkDa0o5iN24hJT4vBDT4t2q9khQ+qb1D8KgCOb02r1PxWXu3vfd6Ha2\n" \
   "mkdB97iGuEh5gO2n4yOmFS5goFlVA2UdPbbhJsb8oKVKDd+YdCKGQDCkQyG4AjmC\n" \
   "YiNm3UPG/qtftTH5cWri67DlLtm6fyUFOMmO6NSh0RtR745pL8GyWJUanyq/Q4bF\n" \
   "HQB21E+WtTsCaqjGaoFcrBunMypmCd+jUZXl27TYENRFbrwNdAh7m2UztcIyb+Sg\n" \
   "VJFyfvVsBQNvnp7GPimVxXZNc4VpxEXObRuPWQN1oZN/90PcZVqTia/SHzEyTryL\n" \
   "ckhiLG3jZiaFZ7pTZ5I9wti9Pn+4kOHvE3Y/4nEnUo4mTxPX9pOlinF+VCiybtV2\n" \
   "u1KSlc+YaIM7VmuyndDZCJRXm3v0/qTE7t5A5fArZl9lvibigMbWB8fpD+c1GpGH\n" \
   "Eo8NRY0lkaM+DkIqQoaziIsz3IKJrfdKaq9bQMSlIfameKBZ8fNYTBZrH9KZAIhz\n" \
   "YwIDAQABo4IBfjCCAXowHQYDVR0OBBYEFIf6nt9SdnXsSUogb1twlo+d77sXMB8G\n" \
   "A1UdIwQYMBaAFIf6nt9SdnXsSUogb1twlo+d77sXMA8GA1UdEwEB/wQFMAMBAf8w\n" \
   "DgYDVR0PAQH/BAQDAgEGMIIBFQYDVR0RBIIBDDCCAQiCEWh0dHA6Ly93d3cuYW5m\n" \
   "LmVzgQtpbmZvQGFuZi5lc6SB5TCB4jE0MDIGA1UECQwrR3JhbiBWaWEgZGUgbGVz\n" \
   "IENvcnRzIENhdGFsYW5lcy4gOTk2LiAwODAxODESMBAGA1UEBwwJQmFyY2Vsb25h\n" \
   "MScwJQYDVQQKDB5BTkYgQXV0b3JpZGFkIGRlIENlcnRpZmljYWNpb24xEjAQBgNV\n" \
   "BAUTCUc2MzI4NzUxMDFZMFcGA1UECwxQSW5zY3JpdGEgZW4gZWwgTWluaXN0ZXJp\n" \
   "byBkZWwgSW50ZXJpb3IgZGUgRXNwYcOxYSBjb24gZWwgbnVtZXJvIG5hY2lvbmFs\n" \
   "IDE3MS40NDMwDQYJKoZIhvcNAQELBQADggIBAIgR9tFTZ9BCYg+HViMxOfF0MHN2\n" \
   "Pe/eC128ARdS+GH8A4thtbqiH/SOYbWofO/0zssHhNKa5iQEj45lCAb8BANpWJMD\n" \
   "nWkPr6jq2+50a6d0MMgSS2l1rvjSF+3nIrEuicshHXSTi3q/vBLKr7uGKMVFaM68\n" \
   "XAropIwk6ndlA0JseARSPsbetv7ALESMIZAxlHV1TcctYHd0bB3c/Jz+PLszJQqs\n" \
   "Cg/kBPo2D111OXZkIY8W/fJuG9veR783khAK2gUnC0zLLCNsYzEbdGt8zUmBsAsM\n" \
   "cGxqGm6B6vDXd65OxWqw13xdq/24+5R8Ng1PF9tvfjZkUFBF30CxjWur7P90WiKI\n" \
   "G7IGfr6BE1NgXlhEQQu4F+HizB1ypEPzGWltecXQ4yOzO+H0WfFTjLTYX6VSveyW\n" \
   "DQV18ixF8M4tHP/SwNE+yyv2b2JJ3/3RpxjtFlLk+opJ574x0gD/dMJuWTH0JqVY\n" \
   "3PbRfE1jIxFpk164Qz/Xp7H7w7f6xh+tQCkBs3PUYmnGIZcPwq44Q6JHlCNsKx4K\n" \
   "hxfggTvRCk4w79cUID45c2qDsRCqTPoOo/cbOpcfVhbH9LdMORpmuLwNogRZEUSE\n" \
   "fWpqR9q+0kcQf4zGSWIURIyDrogdpDgoHDxktqgMgc+qA4ZE2WQl1D8hmev53A46\n" \
   "lUSrWUiWfDXtK3ux\n" \
   "-----END CERTIFICATE-----\n" \
   "-----BEGIN CERTIFICATE-----\n" \
   "MIIEuzCCA6OgAwIBAgIBAjANBgkqhkiG9w0BAQUFADBiMQswCQYDVQQGEwJVUzET\n" \
   "MBEGA1UEChMKQXBwbGUgSW5jLjEmMCQGA1UECxMdQXBwbGUgQ2VydGlmaWNhdGlv\n" \
   "biBBdXRob3JpdHkxFjAUBgNVBAMTDUFwcGxlIFJvb3QgQ0EwHhcNMDYwNDI1MjE0\n" \
   "MDM2WhcNMzUwMjA5MjE0MDM2WjBiMQswCQYDVQQGEwJVUzETMBEGA1UEChMKQXBw\n" \
   "bGUgSW5jLjEmMCQGA1UECxMdQXBwbGUgQ2VydGlmaWNhdGlvbiBBdXRob3JpdHkx\n" \
   "FjAUBgNVBAMTDUFwcGxlIFJvb3QgQ0EwggEiMA0GCSqGSIb3DQEBAQUAA4IBDwAw\n" \
   "ggEKAoIBAQDkkakJH5HbHkdQ6wXtXnmELes2oldMVeyLGYne+Uts9QerIjAC6Bg+\n" \
   "+FAJ039BqJj50cpmnCRrEdCju+QbKsMflZ56DKRHi1vUFjczy8QPTc4UadHJGXL1\n" \
   "XQ7Vf1+b8iUDulWPTV0N8WQ1IxVLFVkds5T39pyez1C6wVhQZ48ItCD3y6wsIG9w\n" \
   "tj8BMIy3Q88PnT3zK0koGsj+zrW5DtleHNbLPbU6rfQPDgCSC7EhFi501TwN22IW\n" \
   "q6NxkkdTVcGvL0Gz+PvjcM3mo0xFfh9Ma1CWQYnEdGILEINBhzOKgbEwWOxaBDKM\n" \
   "aLOPHd5lc/9nXmW8Sdh2nzMUZaF3lMktAgMBAAGjggF6MIIBdjAOBgNVHQ8BAf8E\n" \
   "BAMCAQYwDwYDVR0TAQH/BAUwAwEB/zAdBgNVHQ4EFgQUK9BpR5R2Cf70a40uQKb3\n" \
   "R01/CF4wHwYDVR0jBBgwFoAUK9BpR5R2Cf70a40uQKb3R01/CF4wggERBgNVHSAE\n" \
   "ggEIMIIBBDCCAQAGCSqGSIb3Y2QFATCB8jAqBggrBgEFBQcCARYeaHR0cHM6Ly93\n" \
   "d3cuYXBwbGUuY29tL2FwcGxlY2EvMIHDBggrBgEFBQcCAjCBthqBs1JlbGlhbmNl\n" \
   "IG9uIHRoaXMgY2VydGlmaWNhdGUgYnkgYW55IHBhcnR5IGFzc3VtZXMgYWNjZXB0\n" \
   "YW5jZSBvZiB0aGUgdGhlbiBhcHBsaWNhYmxlIHN0YW5kYXJkIHRlcm1zIGFuZCBj\n" \
   "b25kaXRpb25zIG9mIHVzZSwgY2VydGlmaWNhdGUgcG9saWN5IGFuZCBjZXJ0aWZp\n" \
   "Y2F0aW9uIHByYWN0aWNlIHN0YXRlbWVudHMuMA0GCSqGSIb3DQEBBQUAA4IBAQBc\n" \
   "NplMLXi37Yyb3PN3m/J20ncwT8EfhYOFG5k9RzfyqZtAjizUsZAS2L70c5vu0mQP\n" \
   "y3lPNNiiPvl4/2vIB+x9OYOLUyDTOMSxv5pPCmv/K/xZpwUJfBdAVhEedNO3iyM7\n" \
   "R6PVbyTi69G3cN8PReEnyvFteO3ntRcXqNx+IjXKJdXZD9Zr1KIkIxH3oayPc4Fg\n" \
   "xhtbCS+SsvhESPBgOJ4V9T0mZyCKM2r3DYLP3uujL/lTaltkwGMzd/c6ByxW69oP\n" \
   "IQ7aunMZT7XZNn/Bh1XZp5m5MkL72NVxnn6hUrcbvZNCJBIqxw8dtk2cXmPIS4AX\n" \
   "UKqK1drk/NAJBzewdXUh\n" \
   "-----END CERTIFICATE-----\n" \
   "-----BEGIN CERTIFICATE-----\n" \
   "MIIFkjCCA3qgAwIBAgIIAeDltYNno+AwDQYJKoZIhvcNAQEMBQAwZzEbMBkGA1UE\n" \
   "AwwSQXBwbGUgUm9vdCBDQSAtIEcyMSYwJAYDVQQLDB1BcHBsZSBDZXJ0aWZpY2F0\n" \
   "aW9uIEF1dGhvcml0eTETMBEGA1UECgwKQXBwbGUgSW5jLjELMAkGA1UEBhMCVVMw\n" \
   "HhcNMTQwNDMwMTgxMDA5WhcNMzkwNDMwMTgxMDA5WjBnMRswGQYDVQQDDBJBcHBs\n" \
   "ZSBSb290IENBIC0gRzIxJjAkBgNVBAsMHUFwcGxlIENlcnRpZmljYXRpb24gQXV0\n" \
   "aG9yaXR5MRMwEQYDVQQKDApBcHBsZSBJbmMuMQswCQYDVQQGEwJVUzCCAiIwDQYJ\n" \
   "KoZIhvcNAQEBBQADggIPADCCAgoCggIBANgREkhI2imKScUcx+xuM23+TfvgHN6s\n" \
   "XuI2pyT5f1BrTM65MFQn5bPW7SXmMLYFN14UIhHF6Kob0vuy0gmVOKTvKkmMXT5x\n" \
   "ZgM4+xb1hYjkWpIMBDLyyED7Ul+f9sDx47pFoFDVEovy3d6RhiPw9bZyLgHaC/Yu\n" \
   "OQhfGaFjQQscp5TBhsRTL3b2CtcM0YM/GlMZ81fVJ3/8E7j4ko380yhDPLVoACVd\n" \
   "J2LT3VXdRCCQgzWTxb+4Gftr49wIQuavbfqeQMpOhYV4SbHXw8EwOTKrfl+q04tv\n" \
   "ny0aIWhwZ7Oj8ZhBbZF8+NfbqOdfIRqMM78xdLe40fTgIvS/cjTf94FNcX1RoeKz\n" \
   "8NMoFnNvzcytN31O661A4T+B/fc9Cj6i8b0xlilZ3MIZgIxbdMYs0xBTJh0UT8TU\n" \
   "gWY8h2czJxQI6bR3hDRSj4n4aJgXv8O7qhOTH11UL6jHfPsNFL4VPSQ08prcdUFm\n" \
   "IrQB1guvkJ4M6mL4m1k8COKWNORj3rw31OsMiANDC1CvoDTdUE0V+1ok2Az6DGOe\n" \
   "HwOx4e7hqkP0ZmUoNwIx7wHHHtHMn23KVDpA287PT0aLSmWaasZobNfMmRtHsHLD\n" \
   "d4/E92GcdB/O/WuhwpyUgquUoue9G7q5cDmVF8Up8zlYNPXEpMZ7YLlmQ1A/bmH8\n" \
   "DvmGqmAMQ0uVAgMBAAGjQjBAMB0GA1UdDgQWBBTEmRNsGAPCe8CjoA1/coB6HHcm\n" \
   "jTAPBgNVHRMBAf8EBTADAQH/MA4GA1UdDwEB/wQEAwIBBjANBgkqhkiG9w0BAQwF\n" \
   "AAOCAgEAUabz4vS4PZO/Lc4Pu1vhVRROTtHlznldgX/+tvCHM/jvlOV+3Gp5pxy+\n" \
   "8JS3ptEwnMgNCnWefZKVfhidfsJxaXwU6s+DDuQUQp50DhDNqxq6EWGBeNjxtUVA\n" \
   "eKuowM77fWM3aPbn+6/Gw0vsHzYmE1SGlHKy6gLti23kDKaQwFd1z4xCfVzmMX3z\n" \
   "ybKSaUYOiPjjLUKyOKimGY3xn83uamW8GrAlvacp/fQ+onVJv57byfenHmOZ4VxG\n" \
   "/5IFjPoeIPmGlFYl5bRXOJ3riGQUIUkhOb9iZqmxospvPyFgxYnURTbImHy99v6Z\n" \
   "SYA7LNKmp4gDBDEZt7Y6YUX6yfIjyGNzv1aJMbDZfGKnexWoiIqrOEDCzBL/FePw\n" \
   "N983csvMmOa/orz6JopxVtfnJBtIRD6e/J/JzBrsQzwBvDR4yGn1xuZW7AYJNpDr\n" \
   "FEobXsmII9oDMJELuDY++ee1KG++P+w8j2Ud5cAeh6Squpj9kuNsJnfdBrRkBof0\n" \
   "Tta6SqoWqPQFZ2aWuuJVecMsXUmPgEkrihLHdoBR37q9ZV0+N0djMenl9MU/S60E\n" \
   "inpxLK8JQzcPqOMyT/RFtm2XNuyE9QoB6he7hY1Ck3DDUOUUi78/w0EP3SIEIwiK\n" \
   "um1xRKtzCTrJ+VKACd+66eYWyi4uTLLT3OUEVLLUNIAytbwPF+E=\n" \
   "-----END CERTIFICATE-----\n" \
   "-----BEGIN CERTIFICATE-----\n" \
   "MIICQzCCAcmgAwIBAgIILcX8iNLFS5UwCgYIKoZIzj0EAwMwZzEbMBkGA1UEAwwS\n" \
   "QXBwbGUgUm9vdCBDQSAtIEczMSYwJAYDVQQLDB1BcHBsZSBDZXJ0aWZpY2F0aW9u\n" \
   "IEF1dGhvcml0eTETMBEGA1UECgwKQXBwbGUgSW5jLjELMAkGA1UEBhMCVVMwHhcN\n" \
   "MTQwNDMwMTgxOTA2WhcNMzkwNDMwMTgxOTA2WjBnMRswGQYDVQQDDBJBcHBsZSBS\n" \
   "b290IENBIC0gRzMxJjAkBgNVBAsMHUFwcGxlIENlcnRpZmljYXRpb24gQXV0aG9y\n" \
   "aXR5MRMwEQYDVQQKDApBcHBsZSBJbmMuMQswCQYDVQQGEwJVUzB2MBAGByqGSM49\n" \
   "AgEGBSuBBAAiA2IABJjpLz1AcqTtkyJygRMc3RCV8cWjTnHcFBbZDuWmBSp3ZHtf\n" \
   "TjjTuxxEtX/1H7YyYl3J6YRbTzBPEVoA/VhYDKX1DyxNB0cTddqXl5dvMVztK517\n" \
   "IDvYuVTZXpmkOlEKMaNCMEAwHQYDVR0OBBYEFLuw3qFYM4iapIqZ3r6966/ayySr\n" \
   "MA8GA1UdEwEB/wQFMAMBAf8wDgYDVR0PAQH/BAQDAgEGMAoGCCqGSM49BAMDA2gA\n" \
   "MGUCMQCD6cHEFl4aXTQY2e3v9GwOAEZLuN+yRhHFD/3meoyhpmvOwgPUnPWTxnS4\n" \
   "at+qIxUCMG1mihDK1A3UT82NQz60imOlM27jbdoXt2QfyFMm+YhidDkLF1vLUagM\n" \
   "6BgD56KyKA==\n" \
   "-----END CERTIFICATE-----\n" \
   "-----BEGIN CERTIFICATE-----\n" \
   "MIIFujCCBKKgAwIBAgIBATANBgkqhkiG9w0BAQUFADCBhjELMAkGA1UEBhMCVVMx\n" \
   "HTAbBgNVBAoTFEFwcGxlIENvbXB1dGVyLCBJbmMuMS0wKwYDVQQLEyRBcHBsZSBD\n" \
   "b21wdXRlciBDZXJ0aWZpY2F0ZSBBdXRob3JpdHkxKTAnBgNVBAMTIEFwcGxlIFJv\n" \
   "b3QgQ2VydGlmaWNhdGUgQXV0aG9yaXR5MB4XDTA1MDIxMDAwMTgxNFoXDTI1MDIx\n" \
   "MDAwMTgxNFowgYYxCzAJBgNVBAYTAlVTMR0wGwYDVQQKExRBcHBsZSBDb21wdXRl\n" \
   "ciwgSW5jLjEtMCsGA1UECxMkQXBwbGUgQ29tcHV0ZXIgQ2VydGlmaWNhdGUgQXV0\n" \
   "aG9yaXR5MSkwJwYDVQQDEyBBcHBsZSBSb290IENlcnRpZmljYXRlIEF1dGhvcml0\n" \
   "eTCCASIwDQYJKoZIhvcNAQEBBQADggEPADCCAQoCggEBAOSRqQkfkdseR1DrBe1e\n" \
   "eYQt6zaiV0xV7IsZid75S2z1B6siMALoGD74UAnTf0GomPnRymacJGsR0KO75Bsq\n" \
   "wx+VnnoMpEeLW9QWNzPLxA9NzhRp0ckZcvVdDtV/X5vyJQO6VY9NXQ3xZDUjFUsV\n" \
   "WR2zlPf2nJ7PULrBWFBnjwi0IPfLrCwgb3C2PwEwjLdDzw+dPfMrSSgayP7OtbkO\n" \
   "2V4c1ss9tTqt9A8OAJILsSEWLnTVPA3bYharo3GSR1NVwa8vQbP4++NwzeajTEV+\n" \
   "H0xrUJZBicR0YgsQg0GHM4qBsTBY7FoEMoxos48d3mVz/2deZbxJ2HafMxRloXeU\n" \
   "yS0CAwEAAaOCAi8wggIrMA4GA1UdDwEB/wQEAwIBBjAPBgNVHRMBAf8EBTADAQH/\n" \
   "MB0GA1UdDgQWBBQr0GlHlHYJ/vRrjS5ApvdHTX8IXjAfBgNVHSMEGDAWgBQr0GlH\n" \
   "lHYJ/vRrjS5ApvdHTX8IXjCCASkGA1UdIASCASAwggEcMIIBGAYJKoZIhvdjZAUB\n" \
   "MIIBCTBBBggrBgEFBQcCARY1aHR0cHM6Ly93d3cuYXBwbGUuY29tL2NlcnRpZmlj\n" \
   "YXRlYXV0aG9yaXR5L3Rlcm1zLmh0bWwwgcMGCCsGAQUFBwICMIG2GoGzUmVsaWFu\n" \
   "Y2Ugb24gdGhpcyBjZXJ0aWZpY2F0ZSBieSBhbnkgcGFydHkgYXNzdW1lcyBhY2Nl\n" \
   "cHRhbmNlIG9mIHRoZSB0aGVuIGFwcGxpY2FibGUgc3RhbmRhcmQgdGVybXMgYW5k\n" \
   "IGNvbmRpdGlvbnMgb2YgdXNlLCBjZXJ0aWZpY2F0ZSBwb2xpY3kgYW5kIGNlcnRp\n" \
   "ZmljYXRpb24gcHJhY3RpY2Ugc3RhdGVtZW50cy4wRAYDVR0fBD0wOzA5oDegNYYz\n" \
   "aHR0cHM6Ly93d3cuYXBwbGUuY29tL2NlcnRpZmljYXRlYXV0aG9yaXR5L3Jvb3Qu\n" \
   "Y3JsMFUGCCsGAQUFBwEBBEkwRzBFBggrBgEFBQcwAoY5aHR0cHM6Ly93d3cuYXBw\n" \
   "bGUuY29tL2NlcnRpZmljYXRlYXV0aG9yaXR5L2Nhc2lnbmVycy5odG1sMA0GCSqG\n" \
   "SIb3DQEBBQUAA4IBAQCd2i0oWC99dgS5BNM+zrdmY06PL9T+S61yvaM5xlJNBZhS\n" \
   "9YlRASR5vhoy9+VEi0tEBzmC1lrKtCBe2a4VXR2MHTK/ODFiSF3H4ZCx+CRA+F9Y\n" \
   "m1FdV53B5f88zHIhbsTp6aF31ywXJsM/65roCwO66bNKcuszCVut5mIxauivL9Wv\n" \
   "Hld2j383LS4CXN1jyfJxuCZA3xWNdUQ/eb3mHZnhQyw+rW++uaT+DjUZUWOxw961\n" \
   "kj5ReAFziqQjyqSI8R5cH0EWLX6VCqrpiUGYGxrdyyC/R14MJsVVNU3GMIuZZxTH\n" \
   "CR+6R8faAQmHJEKVvRNgGQrv6n8Obs3BREM6StXj\n" \
   "-----END CERTIFICATE-----\n" \
   "-----BEGIN CERTIFICATE-----\n" \
   "MIID9zCCAt+gAwIBAgILMTI1MzcyODI4MjgwDQYJKoZIhvcNAQELBQAwWDELMAkG\n" \
   "A1UEBhMCSlAxHDAaBgNVBAoTE0phcGFuZXNlIEdvdmVybm1lbnQxDTALBgNVBAsT\n" \
   "BEdQS0kxHDAaBgNVBAMTE0FwcGxpY2F0aW9uQ0EyIFJvb3QwHhcNMTMwMzEyMTUw\n" \
   "MDAwWhcNMzMwMzEyMTUwMDAwWjBYMQswCQYDVQQGEwJKUDEcMBoGA1UEChMTSmFw\n" \
   "YW5lc2UgR292ZXJubWVudDENMAsGA1UECxMER1BLSTEcMBoGA1UEAxMTQXBwbGlj\n" \
   "YXRpb25DQTIgUm9vdDCCASIwDQYJKoZIhvcNAQEBBQADggEPADCCAQoCggEBAKaq\n" \
   "rSVl1gAR1uh6dqr05rRL88zDUrSNrKZPtZJxb0a11a2LEiIXJc5F6BR6hZrkIxCo\n" \
   "+rFnUOVtR+BqiRPjrq418fRCxQX3TZd+PCj8sCaRHoweOBqW3FhEl2LjMsjRFUFN\n" \
   "dZh4vqtoqV7tR76kuo6hApfek3SZbWe0BSXulMjtqqS6MmxCEeu+yxcGkOGThchk\n" \
   "KM4fR8fAXWDudjbcMztR63vPctgPeKgZggiQPhqYjY60zxU2pm7dt+JNQCBT2XYq\n" \
   "0HisifBPizJtROouurCp64ndt295D6uBbrjmiykLWa+2SQ1RLKn9nShjZrhwlXOa\n" \
   "2Po7M7xCQhsyrLEy+z0CAwEAAaOBwTCBvjAdBgNVHQ4EFgQUVqesqgIdsqw9kA6g\n" \
   "by5Bxnbne9owDgYDVR0PAQH/BAQDAgEGMHwGA1UdEQR1MHOkcTBvMQswCQYDVQQG\n" \
   "EwJKUDEYMBYGA1UECgwP5pel5pys5Zu95pS/5bqcMRswGQYDVQQLDBLmlL/lupzo\n" \
   "qo3oqLzln7rnm6QxKTAnBgNVBAMMIOOCouODl+ODquOCseODvOOCt+ODp+ODs0NB\n" \
   "MiBSb290MA8GA1UdEwEB/wQFMAMBAf8wDQYJKoZIhvcNAQELBQADggEBAH+aCXWs\n" \
   "B9FydC53VzDCBJzUgKaD56WgG5/+q/OAvdVKo6GPtkxgEefK4WCB10jBIFmlYTKL\n" \
   "nZ6X02aD2mUuWD7b5S+lzYxzplG+WCigeVxpL0PfY7KJR8q73rk0EWOgDiUX5Yf0\n" \
   "HbCwpc9BqHTG6FPVQvSCLVMJEWgmcZR1E02qdog8dLHW40xPYsNJTE5t8XB+w3+m\n" \
   "Bcx4m+mB26jIx1ye/JKSLaaX8ji1bnOVDMA/zqaUMLX6BbfeniCq/BNkyYq6ZO/i\n" \
   "Y+TYmK5rtT6mVbgzPixy+ywRAPtbFi+E0hOe+gXFwctyTiLdhMpLvNIthhoEdlkf\n" \
   "SUJiOxMfFui61/0=\n" \
   "-----END CERTIFICATE-----\n" \
   "-----BEGIN CERTIFICATE-----\n" \
   "MIIDdzCCAl+gAwIBAgIIXDPLYixfszIwDQYJKoZIhvcNAQELBQAwPDEeMBwGA1UE\n" \
   "AwwVQXRvcyBUcnVzdGVkUm9vdCAyMDExMQ0wCwYDVQQKDARBdG9zMQswCQYDVQQG\n" \
   "EwJERTAeFw0xMTA3MDcxNDU4MzBaFw0zMDEyMzEyMzU5NTlaMDwxHjAcBgNVBAMM\n" \
   "FUF0b3MgVHJ1c3RlZFJvb3QgMjAxMTENMAsGA1UECgwEQXRvczELMAkGA1UEBhMC\n" \
   "REUwggEiMA0GCSqGSIb3DQEBAQUAA4IBDwAwggEKAoIBAQCVhTuXbyo7LjvPpvMp\n" \
   "Nb7PGKw+qtn4TaA+Gke5vJrf8v7MPkfoepbCJI419KkM/IL9bcFyYie96mvr54rM\n" \
   "VD6QUM+A1JX76LWC1BTFtqlVJVfbsVD2sGBkWXppzwO3bw2+yj5vdHLqqjAqc2K+\n" \
   "SZFhyBH+DgMq92og3AIVDV4VavzjgsG1xZ1kCWyjWZgHJ8cblithdHFsQ/H3NYkQ\n" \
   "4J7sVaE3IqKHBAUsR320HLliKWYoyrfhk/WklAOZuXCFteZI6o1Q/NnezG8HDt0L\n" \
   "cp2AMBYHlT8oDv3FdU9T1nSatCQujgKRz3bFmx5VdJx4IbHwLfELn8LVlhgf8FQi\n" \
   "eowHAgMBAAGjfTB7MB0GA1UdDgQWBBSnpQaxLKYJYO7Rl+lwrrw7GWzbITAPBgNV\n" \
   "HRMBAf8EBTADAQH/MB8GA1UdIwQYMBaAFKelBrEspglg7tGX6XCuvDsZbNshMBgG\n" \
   "A1UdIAQRMA8wDQYLKwYBBAGwLQMEAQEwDgYDVR0PAQH/BAQDAgGGMA0GCSqGSIb3\n" \
   "DQEBCwUAA4IBAQAmdzTblEiGKkGdLD4GkGDEjKwLVLgfuXvTBznk+j57sj1O7Z8j\n" \
   "vZfza1zv7v1Apt+hk6EKhqzvINB5Ab149xnYJDE0BAGmuhWawyfc2E8PzBhj/5kP\n" \
   "DpFrdRbhIfzYJsdHt6bPWHJxfrrhTZVHO8mvbaG0weyJ9rQPOLXiZNwlz6bb65pc\n" \
   "maHFCN795trV1lpFDMS3wrUU77QR/w4VtfX128a961qn8FYiqTxlVMYVqL2Gns2D\n" \
   "lmh6cYGJ4Qvh6hEbaAjMaZ7snkGeRDImeuKHCnE96+RapNLbxc3G3mB/ufNPRJLv\n" \
   "KrcYPqcZ2Qt9sTdBQrC6YB3y/gkRsPCHe6ed\n" \
   "-----END CERTIFICATE-----\n" \
   "-----BEGIN CERTIFICATE-----\n" \
   "MIIGFDCCA/ygAwIBAgIIU+w77vuySF8wDQYJKoZIhvcNAQEFBQAwUTELMAkGA1UE\n" \
   "BhMCRVMxQjBABgNVBAMMOUF1dG9yaWRhZCBkZSBDZXJ0aWZpY2FjaW9uIEZpcm1h\n" \
   "cHJvZmVzaW9uYWwgQ0lGIEE2MjYzNDA2ODAeFw0wOTA1MjAwODM4MTVaFw0zMDEy\n" \
   "MzEwODM4MTVaMFExCzAJBgNVBAYTAkVTMUIwQAYDVQQDDDlBdXRvcmlkYWQgZGUg\n" \
   "Q2VydGlmaWNhY2lvbiBGaXJtYXByb2Zlc2lvbmFsIENJRiBBNjI2MzQwNjgwggIi\n" \
   "MA0GCSqGSIb3DQEBAQUAA4ICDwAwggIKAoICAQDKlmuO6vj78aI14H9M2uDDUtd9\n" \
   "thDIAl6zQyrET2qyyhxdKJp4ERppWVevtSBC5IsP5t9bpgOSL/UR5GLXMnE42QQM\n" \
   "cas9UX4PB99jBVzpv5RvwSmCwLTaUbDBPLutN0pcyvFLNg4kq7/DhHf9qFD0sefG\n" \
   "L9ItWY16Ck6WaVICqjaY7Pz6FIMMNx/Jkjd/14Et5cS54D40/mf0PmbR0/RAz15i\n" \
   "NA9wBj4gGFrO93IbJWyTdBSTo3OxDqqHECNZXyAFGUftaI6SEspd/NYrspI8IM/h\n" \
   "X68gvqB2f3bl7BqGYTM+53u0P6APjqK5am+5hyZvQWyIplD9amML9ZMWGxmPsu2b\n" \
   "m8mQ9QEM3xk9Dz44I8kvjwzRAv4bVdZO0I08r0+k8/6vKtMFnXkIoctXMbScyJCy\n" \
   "Z/QYFpM6/EfY0XiWMR+6KwxfXZmtY4laJCB22N/9q06mIqqdXuYnin1oKaPnirja\n" \
   "EbsXLZmdEyRG98Xi2J+Of8ePdG1asuhy9azuJBCtLxTa/y2aRnFHvkLfuwHb9H/T\n" \
   "KI8xWVvTyQKmtFLKbpf7Q8UIJm+K9Lv9nyiqDdVF8xM6HdjAeI9BZzwelGSuewvF\n" \
   "6NkBiDkal4ZkQdU7hwxu+g/GvUgUvzlN1J5Bto+WHWOWk9mVBngxaJ43BjuAiUVh\n" \
   "OSPHG0SjFeUc+JIwuwIDAQABo4HvMIHsMBIGA1UdEwEB/wQIMAYBAf8CAQEwDgYD\n" \
   "VR0PAQH/BAQDAgEGMB0GA1UdDgQWBBRlzeurNR4APn7VdMActHNHDhpkLzCBpgYD\n" \
   "VR0gBIGeMIGbMIGYBgRVHSAAMIGPMC8GCCsGAQUFBwIBFiNodHRwOi8vd3d3LmZp\n" \
   "cm1hcHJvZmVzaW9uYWwuY29tL2NwczBcBggrBgEFBQcCAjBQHk4AUABhAHMAZQBv\n" \
   "ACAAZABlACAAbABhACAAQgBvAG4AYQBuAG8AdgBhACAANAA3ACAAQgBhAHIAYwBl\n" \
   "AGwAbwBuAGEAIAAwADgAMAAxADcwDQYJKoZIhvcNAQEFBQADggIBABd9oPm03cXF\n" \
   "661LJLWhAqvdpYhKsg9VSytXjDvlMd3+xDLx51tkljYyGOylMnfX40S2wBEqgLk9\n" \
   "am58m9Ot/MPWo+ZkKXzR4Tgegiv/J2Wv+xYVxC5xhOW1//qkR71kMrv2JYSiJ0L1\n" \
   "ILDCExARzRAVukKQKtJE4ZYm6zFIEv0q2skGz3QeqUvVhyj5eTSSPi5E6PaPT481\n" \
   "PyWzOdxjKpBrIF/EUhJOlywqrJ2X3kjyo2bbwtKDlaZmp54lD+kLM5FlClrD2VQS\n" \
   "3a/DTg4fJl4N3LON7NWBcN7STyQF82xO9UxJZo3R/9ILJUFI/lGExkKvgATP0H5k\n" \
   "SeTy36LssUzAKh3ntLFlosS88Zj0qnAHY7S42jtM+kAiMFsRpvAFDsYCA0irhpuF\n" \
   "3dvd6qJ2gHN99ZwExEWN57kci57q13XRcrHedUTnQn3iV2t93Jm8PYMo6oCTjcVM\n" \
   "ZcFwgbg4/EMxsvYDNEeyrPsiBsse3RdHHF9mudMaotoRsaS8I8nkvof/uZS2+F0g\n" \
   "StRf571oe2XyFR7SOqkt6dhrJKyXWERHrVkY8SFlcN7ONGCoQPHzPKTDKCOM/icz\n" \
   "Q0CgFzzr6juwcqajuUpLXhZI9LK8yIySxZ2frHI2vDSANGupi5LAuBft7HZT9SQB\n" \
   "jLMi6Et8Vcad+qMUu2WFbm5PEn4KPJ2V\n" \
   "-----END CERTIFICATE-----\n" \
   "-----BEGIN CERTIFICATE-----\n" \
   "MIIJmzCCB4OgAwIBAgIBATANBgkqhkiG9w0BAQwFADCCAR4xPjA8BgNVBAMTNUF1\n" \
   "dG9yaWRhZCBkZSBDZXJ0aWZpY2FjaW9uIFJhaXogZGVsIEVzdGFkbyBWZW5lem9s\n" \
   "YW5vMQswCQYDVQQGEwJWRTEQMA4GA1UEBxMHQ2FyYWNhczEZMBcGA1UECBMQRGlz\n" \
   "dHJpdG8gQ2FwaXRhbDE2MDQGA1UEChMtU2lzdGVtYSBOYWNpb25hbCBkZSBDZXJ0\n" \
   "aWZpY2FjaW9uIEVsZWN0cm9uaWNhMUMwQQYDVQQLEzpTdXBlcmludGVuZGVuY2lh\n" \
   "IGRlIFNlcnZpY2lvcyBkZSBDZXJ0aWZpY2FjaW9uIEVsZWN0cm9uaWNhMSUwIwYJ\n" \
   "KoZIhvcNAQkBFhZhY3JhaXpAc3VzY2VydGUuZ29iLnZlMB4XDTEwMTIyMjE4MDgy\n" \
   "MVoXDTMwMTIxNzIzNTk1OVowggEeMT4wPAYDVQQDEzVBdXRvcmlkYWQgZGUgQ2Vy\n" \
   "dGlmaWNhY2lvbiBSYWl6IGRlbCBFc3RhZG8gVmVuZXpvbGFubzELMAkGA1UEBhMC\n" \
   "VkUxEDAOBgNVBAcTB0NhcmFjYXMxGTAXBgNVBAgTEERpc3RyaXRvIENhcGl0YWwx\n" \
   "NjA0BgNVBAoTLVNpc3RlbWEgTmFjaW9uYWwgZGUgQ2VydGlmaWNhY2lvbiBFbGVj\n" \
   "dHJvbmljYTFDMEEGA1UECxM6U3VwZXJpbnRlbmRlbmNpYSBkZSBTZXJ2aWNpb3Mg\n" \
   "ZGUgQ2VydGlmaWNhY2lvbiBFbGVjdHJvbmljYTElMCMGCSqGSIb3DQEJARYWYWNy\n" \
   "YWl6QHN1c2NlcnRlLmdvYi52ZTCCAiIwDQYJKoZIhvcNAQEBBQADggIPADCCAgoC\n" \
   "ggIBAME77xNS8ZlW47RsBeEaaRZhJoZ4rw785UAFCuPZOAVMqNS1wMYqzy95q6Gk\n" \
   "UO81ER/ugiQX/KMcq/4HBn83fwdYWxPZfwBfK7BP2p/JsFgzYeFP0BXOLmvoJIzl\n" \
   "Jb6FW+1MPwGBjuaZGFImWZsSmGUclb51mRYMZETh9/J5CLThR1exStxHQptwSzra\n" \
   "zNFpkQY/zmj7+YZNA9yDoroVFv6sybYOZ7OxNDo7zkSLo45I7gMwtxqWZ8VkJZkC\n" \
   "8+p0dX6mkhUT0QAV64Zc9HsZiH/oLhEkXjhrgZ28cF73MXIqLx1fyM4kPH1yOJi/\n" \
   "R72nMwL7D+Sd6mZgI035TxuHXc2/uOwXfKrrTjaJDz8Jp6DdessOkxIgkKXRjP+F\n" \
   "K3ze3n4NUIRGhGRtyvEjK95/2g02t6PeYiYVGur6ruS49n0RAaSS0/LJb6XzaAAe\n" \
   "0mmO2evnEqxIKwy2mZRNPfAVW1l3wCnWiUwryBU6OsbFcFFrQm+00wOicXvOTHBM\n" \
   "aiCVAVZTb9RSLyi+LJ1llzJZO3pq3IRiiBj38Nooo+2ZNbMEciSgmig7YXaUcmud\n" \
   "SVQvLSL+Yw+SqawyezwZuASbp7d/0rutQ59d81zlbMt3J7yB567rT2IqIydQ8qBW\n" \
   "k+fmXzghX+/FidYsh/aK+zZ7Wy68kKHuzEw1Vqkat5DGs+VzAgMBAAGjggLeMIIC\n" \
   "2jASBgNVHRMBAf8ECDAGAQH/AgECMDcGA1UdEgQwMC6CD3N1c2NlcnRlLmdvYi52\n" \
   "ZaAbBgVghl4CAqASDBBSSUYtRy0yMDAwNDAzNi0wMB0GA1UdDgQWBBStuyIdxuDS\n" \
   "Aaj9dlBSk+2YwU2u0zCCAVAGA1UdIwSCAUcwggFDgBStuyIdxuDSAaj9dlBSk+2Y\n" \
   "wU2u06GCASakggEiMIIBHjE+MDwGA1UEAxM1QXV0b3JpZGFkIGRlIENlcnRpZmlj\n" \
   "YWNpb24gUmFpeiBkZWwgRXN0YWRvIFZlbmV6b2xhbm8xCzAJBgNVBAYTAlZFMRAw\n" \
   "DgYDVQQHEwdDYXJhY2FzMRkwFwYDVQQIExBEaXN0cml0byBDYXBpdGFsMTYwNAYD\n" \
   "VQQKEy1TaXN0ZW1hIE5hY2lvbmFsIGRlIENlcnRpZmljYWNpb24gRWxlY3Ryb25p\n" \
   "Y2ExQzBBBgNVBAsTOlN1cGVyaW50ZW5kZW5jaWEgZGUgU2VydmljaW9zIGRlIENl\n" \
   "cnRpZmljYWNpb24gRWxlY3Ryb25pY2ExJTAjBgkqhkiG9w0BCQEWFmFjcmFpekBz\n" \
   "dXNjZXJ0ZS5nb2IudmWCAQEwDgYDVR0PAQH/BAQDAgEGMDcGA1UdEQQwMC6CD3N1\n" \
   "c2NlcnRlLmdvYi52ZaAbBgVghl4CAqASDBBSSUYtRy0yMDAwNDAzNi0wMFQGA1Ud\n" \
   "HwRNMEswJKAioCCGHmhodHA6Ly93d3cuc3VzY2VydGUuZ29iLnZlL2xjcjAjoCGg\n" \
   "H4YdbGRhcDovL2FjcmFpei5zdXNjZXJ0ZS5nb2IudmUwNwYIKwYBBQUHAQEEKzAp\n" \
   "MCcGCCsGAQUFBzABhhtoaHRwOi8vb2NzcC5zdXNjZXJ0ZS5nb2IudmUwQAYDVR0g\n" \
   "BDkwNzA1BgVghl4BAjAsMCoGCCsGAQUFBwIBFh5odHRwOi8vd3d3LnN1c2NlcnRl\n" \
   "LmdvYi52ZS9kcGMwDQYJKoZIhvcNAQEMBQADggIBAK4qy/zmZ9zBwfW3yOYtLcBT\n" \
   "Oy4szJyPz7/RhNH3bPVH7HbDTGpi6JZ4YXdXMBeJE5qBF4a590Kgj8Rlnltt+Rbo\n" \
   "OFQOU1UDqKuTdBsA//Zry5899fmn8jBUkg4nh09jhHHbLlaUScdz704Zz2+UVg7i\n" \
   "s/r3Legxap60KzmdrmTAE9VKte1TQRgavQwVX5/2mO/J+SCas//UngI+h8SyOucq\n" \
   "mjudYEgBrZaodUsagUfn/+AzFNrGLy+al+5nZeHb8JnCfLHWS0M9ZyhgoeO/czyn\n" \
   "99+5G93VWNv4zfc4KiavHZKrkn8F9pg0ycIZh+OwPT/RE2zq4gTazBMlP3ACIe/p\n" \
   "olkNaOEa8KvgzW96sjBZpMW49zFmyINYkcj+uaNCJrVGsXgdBmkuRGJNWFZ9r0cG\n" \
   "woIaxViFBypsz045r1ESfYPlfDOavBhZ/giR/Xocm9CHkPRY2BApMMR0DUCyGETg\n" \
   "Ql+L3kfdTKzuDjUp2DM9FqysQmaM81YDZufWkMhlZPfHwC7KbNougoLroa5Umeos\n" \
   "bqAXWmk46SwIdWRPLLqbUpDTKooynZKpSYIkkotdgJoVZUUCY+RCO8jsVPEU6ece\n" \
   "SxztNUm5UOta1OJPMwSAKRHOo3ilVb9c6lAixDdvV8MeNbqe6asM1mpCHWbJ/0rg\n" \
   "5Ls9Cxx8hracyp0ev7b0\n" \
   "-----END CERTIFICATE-----\n" \
   "-----BEGIN CERTIFICATE-----\n" \
   "MIIDdzCCAl+gAwIBAgIEAgAAuTANBgkqhkiG9w0BAQUFADBaMQswCQYDVQQGEwJJ\n" \
   "RTESMBAGA1UEChMJQmFsdGltb3JlMRMwEQYDVQQLEwpDeWJlclRydXN0MSIwIAYD\n" \
   "VQQDExlCYWx0aW1vcmUgQ3liZXJUcnVzdCBSb290MB4XDTAwMDUxMjE4NDYwMFoX\n" \
   "DTI1MDUxMjIzNTkwMFowWjELMAkGA1UEBhMCSUUxEjAQBgNVBAoTCUJhbHRpbW9y\n" \
   "ZTETMBEGA1UECxMKQ3liZXJUcnVzdDEiMCAGA1UEAxMZQmFsdGltb3JlIEN5YmVy\n" \
   "VHJ1c3QgUm9vdDCCASIwDQYJKoZIhvcNAQEBBQADggEPADCCAQoCggEBAKMEuyKr\n" \
   "mD1X6CZymrV51Cni4eiVgLGw41uOKymaZN+hXe2wCQVt2yguzmKiYv60iNoS6zjr\n" \
   "IZ3AQSsBUnuId9Mcj8e6uYi1agnnc+gRQKfRzMpijS3ljwumUNKoUMMo6vWrJYeK\n" \
   "mpYcqWe4PwzV9/lSEy/CG9VwcPCPwBLKBsua4dnKM3p31vjsufFoREJIE9LAwqSu\n" \
   "XmD+tqYF/LTdB1kC1FkYmGP1pWPgkAx9XbIGevOF6uvUA65ehD5f/xXtabz5OTZy\n" \
   "dc93Uk3zyZAsuT3lySNTPx8kmCFcB5kpvcY67Oduhjprl3RjM71oGDHweI12v/ye\n" \
   "jl0qhqdNkNwnGjkCAwEAAaNFMEMwHQYDVR0OBBYEFOWdWTCCR1jMrPoIVDaGezq1\n" \
   "BE3wMBIGA1UdEwEB/wQIMAYBAf8CAQMwDgYDVR0PAQH/BAQDAgEGMA0GCSqGSIb3\n" \
   "DQEBBQUAA4IBAQCFDF2O5G9RaEIFoN27TyclhAO992T9Ldcw46QQF+vaKSm2eT92\n" \
   "9hkTI7gQCvlYpNRhcL0EYWoSihfVCr3FvDB81ukMJY2GQE/szKN+OMY3EU/t3Wgx\n" \
   "jkzSswF07r51XgdIGn9w/xZchMB5hbgF/X++ZRGjD8ACtPhSNzkE1akxehi/oCr0\n" \
   "Epn3o0WC4zxe9Z2etciefC7IpJ5OCBRLbf1wbWsaY71k5h+3zvDyny67G7fyUIhz\n" \
   "ksLi4xaNmjICq44Y3ekQEe5+NauQrz4wlHrQMz2nZQ/1/I6eYs9HRCwBXbsdtTLS\n" \
   "R9I4LtD+gdwyah617jzV/OeBHRnDJELqYzmp\n" \
   "-----END CERTIFICATE-----\n" \
   "-----BEGIN CERTIFICATE-----\n" \
   "MIIDjjCCAnagAwIBAgIIKv++n6Lw6YcwDQYJKoZIhvcNAQEFBQAwKDELMAkGA1UE\n" \
   "BhMCQkUxGTAXBgNVBAMTEEJlbGdpdW0gUm9vdCBDQTIwHhcNMDcxMDA0MTAwMDAw\n" \
   "WhcNMjExMjE1MDgwMDAwWjAoMQswCQYDVQQGEwJCRTEZMBcGA1UEAxMQQmVsZ2l1\n" \
   "bSBSb290IENBMjCCASIwDQYJKoZIhvcNAQEBBQADggEPADCCAQoCggEBAMZzQh6S\n" \
   "/3UPi790hqc/7bIYLS2X+an7mEoj39WN4IzGMhwWLQdC1i22bi+n9fzGhYJdld61\n" \
   "IgDMqFNAn68KNaJ6x+HK92AQZw6nUHMXU5WfIp8MXW+2QbyM69odRr2nlL/zGsvU\n" \
   "+40OHjPIltfsjFPekx40HopQcSZYtF3CiInaYNKJIT/e1wEYNm7hLHADBGXvmAYr\n" \
   "XR5i3FVr/mZkIV/4L+HXmymvb82fqgxG0YjFnaKVn6w/Fa7yYd/vw2uaItgscf1Y\n" \
   "HewApDgglVrH1Tdjuk+bqv5WRi5j2Qsj1Yr6tSPwiRuhFA0m2kHwOI8w7QUmecFL\n" \
   "TqG4flVSOmlGhHUCAwEAAaOBuzCBuDAOBgNVHQ8BAf8EBAMCAQYwDwYDVR0TAQH/\n" \
   "BAUwAwEB/zBCBgNVHSAEOzA5MDcGBWA4CQEBMC4wLAYIKwYBBQUHAgEWIGh0dHA6\n" \
   "Ly9yZXBvc2l0b3J5LmVpZC5iZWxnaXVtLmJlMB0GA1UdDgQWBBSFiuv0xbu+DlkD\n" \
   "lN7WgAEV4xCcOTARBglghkgBhvhCAQEEBAMCAAcwHwYDVR0jBBgwFoAUhYrr9MW7\n" \
   "vg5ZA5Te1oABFeMQnDkwDQYJKoZIhvcNAQEFBQADggEBAFHYhd27V2/MoGy1oyCc\n" \
   "UwnzSgEMdL8rs5qauhjyC4isHLMzr87lEwEnkoRYmhC598wUkmt0FoqW6FHvv/pK\n" \
   "JaeJtmMrXZRY0c8RcrYeuTlBFk0pvDVTC9rejg7NqZV3JcqUWumyaa7YwBO+mPyW\n" \
   "nIR/VRPmPIfjvCCkpDZoa01gZhz5v6yAlGYuuUGK02XThIAC71AdXkbc98m6tTR8\n" \
   "KvPG2F9fVJ3bTc0R5/0UAoNmXsimABKgX77OFP67H6dh96tK8QYUn8pJQsKpvO2F\n" \
   "sauBQeYNxUJpU4c5nUwfAA4+Bw11V0SoU7Q2dmSZ3G7rPUZuFF1eR1ONeE3gJ7uO\n" \
   "hXY=\n" \
   "-----END CERTIFICATE-----\n" \
   "-----BEGIN CERTIFICATE-----\n" \
   "MIIFWTCCA0GgAwIBAgIBAjANBgkqhkiG9w0BAQsFADBOMQswCQYDVQQGEwJOTzEd\n" \
   "MBsGA1UECgwUQnV5cGFzcyBBUy05ODMxNjMzMjcxIDAeBgNVBAMMF0J1eXBhc3Mg\n" \
   "Q2xhc3MgMiBSb290IENBMB4XDTEwMTAyNjA4MzgwM1oXDTQwMTAyNjA4MzgwM1ow\n" \
   "TjELMAkGA1UEBhMCTk8xHTAbBgNVBAoMFEJ1eXBhc3MgQVMtOTgzMTYzMzI3MSAw\n" \
   "HgYDVQQDDBdCdXlwYXNzIENsYXNzIDIgUm9vdCBDQTCCAiIwDQYJKoZIhvcNAQEB\n" \
   "BQADggIPADCCAgoCggIBANfHXvfBB9R3+0Mh9PT1aeTuMgHbo4Yf5FkNuud1g1Lr\n" \
   "6hxhFUi7HQfKjK6w3Jad6sNgkoaCKHOcVgb/S2TwDCo3SbXlzwx87vFKu3MwZfPV\n" \
   "L4O2fuPn9Z6rYPnT8Z2SdIrkHJasW4DptfQxh6NR/Md+oW+OU3fUl8FVM5I+GC91\n" \
   "1K2GScuVr1QGbNgGE41b/+EmGVnAJLqBcXmQRFBoJJRfuLMR8SlBYaNByyM21cHx\n" \
   "MlAQTn/0hpPshNOOvEu/XAFOBz3cFIqUCqTqc/sLUegTBxj6DvEr0VQVfTzh97QZ\n" \
   "QmdiXnfgolXsttlpF9U6r0TtSsWe5HonfOV116rLJeffawrbD02TTqigzXsu8lkB\n" \
   "arcNuAeBfos4GzjmCleZPe4h6KP1DBbdi+w0jpwqHAAVF41og9JwnxgIzRFo1clr\n" \
   "Us3ERo/ctfPYV3Me6ZQ5BL/T3jjetFPsaRyifsSP5BtwrfKi+fv3FmRmaZ9JUaLi\n" \
   "FRhnBkp/1Wy1TbMz4GHrXb7pmA8y1x1LPC5aAVKRCfLf6o3YBkBjqhHk/sM3nhRS\n" \
   "P/TizPJhk9H9Z2vXUq6/aKtAQ6BXNVN48FP4YUIHZMbXb5tMOA1jrGKvNouicwoN\n" \
   "9SG9dKpN6nIDSdvHXx1iY8f93ZHsM+71bbRuMGjeyNYmsHVee7QHIJihdjK4TWxP\n" \
   "AgMBAAGjQjBAMA8GA1UdEwEB/wQFMAMBAf8wHQYDVR0OBBYEFMmAd+BikoL1Rpzz\n" \
   "uvdMw964o605MA4GA1UdDwEB/wQEAwIBBjANBgkqhkiG9w0BAQsFAAOCAgEAU18h\n" \
   "9bqwOlI5LJKwbADJ784g7wbylp7ppHR/ehb8t/W2+xUbP6umwHJdELFx7rxP462s\n" \
   "A20ucS6vxOOto70MEae0/0qyexAQH6dXQbLArvQsWdZHEIjzIVEpMMpghq9Gqx3t\n" \
   "OluwlN5E40EIosHsHdb9T7bWR9AUC8rmyrV7d35BH16Dx7aMOZawP5aBQW9gkOLo\n" \
   "+fsicdl9sz1Gv7SEr5AcD48Saq/v7h56rgJKihcrdv6sVIkkLE8/trKnToyokZf7\n" \
   "KcZ7XC25y2a2t6hbElGFtQl+Ynhw/qlqYLYdDnkM/crqJIByw5c/8nerQyIKx+u2\n" \
   "DISCLIBrQYoIwOula9+ZEsuK1V6ADJHgJgg2SMX6OBE1/yWDLfJ6v9r9jv6ly0Us\n" \
   "H8SIU653DtmadsWOLB2jutXsMq7Aqqz30XpN69QH4kj3Io6wpJ9qzo6ysmD0oyLQ\n" \
   "I+uUWnpp3Q+/QFesa1lQ2aOZ4W7+jQF5JyMV3pKdewlNWudLSDBaGOYKbeaP4NK7\n" \
   "5t98biGCwWg5TbSYWGZizEqQXsP6JwSxeRV0mcy+rSDeJmAc61ZRpqPq5KM/p/9h\n" \
   "3PFaTWwyI0PurKju7koSCTxdccK+efrCh2gdC/1cacwG0Jp9VJkqyTkaGa9LKkPz\n" \
   "Y11aWOIv4x3kqdbQCtCev9eBCfHJxyYNrJgWVqA=\n" \
   "-----END CERTIFICATE-----\n" \
   "-----BEGIN CERTIFICATE-----\n" \
   "MIIFWTCCA0GgAwIBAgIBAjANBgkqhkiG9w0BAQsFADBOMQswCQYDVQQGEwJOTzEd\n" \
   "MBsGA1UECgwUQnV5cGFzcyBBUy05ODMxNjMzMjcxIDAeBgNVBAMMF0J1eXBhc3Mg\n" \
   "Q2xhc3MgMyBSb290IENBMB4XDTEwMTAyNjA4Mjg1OFoXDTQwMTAyNjA4Mjg1OFow\n" \
   "TjELMAkGA1UEBhMCTk8xHTAbBgNVBAoMFEJ1eXBhc3MgQVMtOTgzMTYzMzI3MSAw\n" \
   "HgYDVQQDDBdCdXlwYXNzIENsYXNzIDMgUm9vdCBDQTCCAiIwDQYJKoZIhvcNAQEB\n" \
   "BQADggIPADCCAgoCggIBAKXaCpUWUOOV8l6ddjEGMnqb8RB2uACatVI2zSRHsJ8Y\n" \
   "ZLya9vrVediQYkwiL944PdbgqOkcLNt4EemOaFEVcsfzM4fkoF0LXOBXByow9c3E\n" \
   "N3coTRiR5r/VUv1xLXA+58bEiuPwKAv0dpihi4dVsjoT/Lc+JzeOIuOoTyrvYLs9\n" \
   "tznDDgFHmV0ST9tD+leh7fmdvhFHJlsTmKtdFoqwNxxXnUX/iJY2v7vKB3tvh2PX\n" \
   "0DJq1l1sDPGzbjniazEuOQAnFN44wOwZZoYS6J1yFhNkUsepNxz9gjDthBgd9K5c\n" \
   "/3ATAOux9TN6S9ZV+AWNS2mw9bMoNlwUxFFzTWsL8TQH2xc519woe2v1n/MuwU8X\n" \
   "KhDzzMro6/1rqy6any2CbgTUUgGTLT2G/H783+9CHaZr77kgxve9oKeV/afmiSTY\n" \
   "zIw0bOIjL9kSGiG5VZFvC5F5GQytQIgLcOJ60g7YaEi7ghM5EFjp2CoHxhLbWNvS\n" \
   "O1UQRwUVZ2J+GGOmRj8JDlQyXr8NYnon74Do29lLBlo3WiXQCBJ31G8JUJc9yB3D\n" \
   "34xFMFbG02SrZvPAXpacw8Tvw3xrizp5f7NJzz3iiZ+gMEuFuZyUJHmPfWupRWgP\n" \
   "K9Dx2hzLabjKSWJtyNBjYt1gD1iqj6G8BaVmos8bdrKEZLFMOVLAMLrwjEsCsLa3\n" \
   "AgMBAAGjQjBAMA8GA1UdEwEB/wQFMAMBAf8wHQYDVR0OBBYEFEe4zf/lb+74suwv\n" \
   "Tg75JbCOPGvDMA4GA1UdDwEB/wQEAwIBBjANBgkqhkiG9w0BAQsFAAOCAgEAACAj\n" \
   "QTUEkMJAYmDv4jVM1z+s4jSQuKFvdvoWFqRINyzpkMLyPPgKn9iB5btb2iUspKdV\n" \
   "cSQy9sgL8rxq+JOssgfCX5/bzMiKqr5qb+FJEMwx14C7u8jYog5kV+qi9cKpMRXS\n" \
   "IGrs/CIBKM+GuIAeqcwRpTzyFrNHnfzSgCHEy9BHcEGhyoMZCCxt8l13nIoUE9Q2\n" \
   "HJLw5QY33KbmkJs4j1xrG0aGQ0JfPgEHU1RdZX33inOhmlRaHylDFCfChQ+1iHsa\n" \
   "O5S3HWCntZznKWlXWpuTekMwGwPXYshApqr8ZORK15FTAaggiG6cX0S5y2CBNOxv\n" \
   "033aSF/rtJC8LakcC6wc1aJoIIAE1vyxjy+7SjENSoYc6+I2KSb12tjE8nVhz36u\n" \
   "dmNKekBlk4f4HoCMhuWG1o8O/FMsYOgWYRqiPkN7zTlgVGr18okmAWiDSKIz6MkE\n" \
   "kbIRNBE+6tBDGR8Dk5AM/1E9V/RBbuHLoL7ryWPNbczk+DaqaJ3tvV2XcEQNtg41\n" \
   "3OEMXbugUZTLfhbrES+jkkXITHHZvMmZUldGL1DPvTVp9D0VzgalLA8+9oG6lLvD\n" \
   "u79leNKGef9JOxqDDPDeeOzI8k1MGt6CKfjBWtrt7uYnXuhF0J0cUahoq0Tj0Itq\n" \
   "4/g7u9xN12TyUb7mqqta6THuBrxzvxNiCp/HuZc=\n" \
   "-----END CERTIFICATE-----\n" \
   "-----BEGIN CERTIFICATE-----\n" \
   "MIIFaTCCA1GgAwIBAgIJAMMDmu5QkG4oMA0GCSqGSIb3DQEBBQUAMFIxCzAJBgNV\n" \
   "BAYTAlNLMRMwEQYDVQQHEwpCcmF0aXNsYXZhMRMwEQYDVQQKEwpEaXNpZyBhLnMu\n" \
   "MRkwFwYDVQQDExBDQSBEaXNpZyBSb290IFIxMB4XDTEyMDcxOTA5MDY1NloXDTQy\n" \
   "MDcxOTA5MDY1NlowUjELMAkGA1UEBhMCU0sxEzARBgNVBAcTCkJyYXRpc2xhdmEx\n" \
   "EzARBgNVBAoTCkRpc2lnIGEucy4xGTAXBgNVBAMTEENBIERpc2lnIFJvb3QgUjEw\n" \
   "ggIiMA0GCSqGSIb3DQEBAQUAA4ICDwAwggIKAoICAQCqw3j33Jijp1pedxiy3QRk\n" \
   "D2P9m5YJgNXoqqXinCaUOuiZc4yd39ffg/N4T0Dhf9Kn0uXKE5Pn7cZ3Xza1lK/o\n" \
   "OI7bm+V8u8yN63Vz4STN5qctGS7Y1oprFOsIYgrY3LMATcMjfF9DCCMyEtztDK3A\n" \
   "fQ+lekLZWnDZv6fXARz2m6uOt0qGeKAeVjGu74IKgEH3G8muqzIm1Cxr7X1r5OJe\n" \
   "IgpFy4QxTaz+29FHuvlglzmxZcfe+5nkCiKxLU3lSCZpq+Kq8/v8kiky6bM+TR8n\n" \
   "oc2OuRf7JT7JbvN32g0S9l3HuzYQ1VTW8+DiR0jm3hTaYVKvJrT1cU/J19IG32PK\n" \
   "/yHoWQbgCNWEFVP3Q+V8xaCJmGtzxmjOZd69fwX3se72V6FglcXM6pM6vpmumwKj\n" \
   "rckWtc7dXpl4fho5frLABaTAgqWjR56M6ly2vGfb5ipN0gTco65F97yLnByn1tUD\n" \
   "3AjLLhbKXEAz6GfDLuemROoRRRw1ZS0eRWEkG4IupZ0zXWX4Qfkuy5Q/H6MMMSRE\n" \
   "7cderVC6xkGbrPAXZcD4XW9boAo0PO7X6oifmPmvTiT6l7Jkdtqr9O3jw2Dv1fkC\n" \
   "yC2fg69naQanMVXVz0tv/wQFx1isXxYb5dKj6zHbHzMVTdDypVP1y+E9Tmgt2BLd\n" \
   "qvLmTZtJ5cUoobqwWsagtQIDAQABo0IwQDAPBgNVHRMBAf8EBTADAQH/MA4GA1Ud\n" \
   "DwEB/wQEAwIBBjAdBgNVHQ4EFgQUiQq0OJMa5qvum5EY+fU8PjXQ04IwDQYJKoZI\n" \
   "hvcNAQEFBQADggIBADKL9p1Kyb4U5YysOMo6CdQbzoaz3evUuii+Eq5FLAR0rBNR\n" \
   "xVgYZk2C2tXck8An4b58n1KeElb21Zyp9HWc+jcSjxyT7Ff+Bw+r1RL3D65hXlaA\n" \
   "SfX8MPWbTx9BLxyE04nH4toCdu0Jz2zBuByDHBb6lM19oMgY0sidbvW9adRtPTXo\n" \
   "HqJPYNcHKfyyo6SdbhWSVhlMCrDpfNIZTUJG7L399ldb3Zh+pE3McgODWF3vkzpB\n" \
   "emOqfDqo9ayk0d2iLbYq/J8BjuIQscTK5GfbVSUZP/3oNn6z4eGBrxEWi1CXYBmC\n" \
   "AMBrTXO40RMHPuq2MU/wQppt4hF05ZSsjYSVPCGvxdpHyN85YmLLW1AL14FABZyb\n" \
   "7bq2ix4Eb5YgOe2kfSnbSM6C3NQCjR0EMVrHS/BsYVLXtFHCgWzN4funodKSds+x\n" \
   "DzdYpPJScWc/DIh4gInByLUfkmO+p3qKViwaqKactV2zY9ATIKHrkWzQjX2v3wvk\n" \
   "F7mGnjixlAxYjOBVqjtjbZqJYLhkKpLGN/R+Q0O3c+gB53+XD9fyexn9GtePyfqF\n" \
   "a3qdnom2piiZk4hA9z7NUaPK6u95RyG1/jLix8NRb76AdPCkwzryT+lf3xkK8jsT\n" \
   "Q6wxpLPn6/wY1gGp8yqPNg7rtLG8t0zJa7+h89n07eLw4+1knj0vllJPgFOL\n" \
   "-----END CERTIFICATE-----\n" \
   "-----BEGIN CERTIFICATE-----\n" \
   "MIIFaTCCA1GgAwIBAgIJAJK4iNuwisFjMA0GCSqGSIb3DQEBCwUAMFIxCzAJBgNV\n" \
   "BAYTAlNLMRMwEQYDVQQHEwpCcmF0aXNsYXZhMRMwEQYDVQQKEwpEaXNpZyBhLnMu\n" \
   "MRkwFwYDVQQDExBDQSBEaXNpZyBSb290IFIyMB4XDTEyMDcxOTA5MTUzMFoXDTQy\n" \
   "MDcxOTA5MTUzMFowUjELMAkGA1UEBhMCU0sxEzARBgNVBAcTCkJyYXRpc2xhdmEx\n" \
   "EzARBgNVBAoTCkRpc2lnIGEucy4xGTAXBgNVBAMTEENBIERpc2lnIFJvb3QgUjIw\n" \
   "ggIiMA0GCSqGSIb3DQEBAQUAA4ICDwAwggIKAoICAQCio8QACdaFXS1tFPbCw3Oe\n" \
   "NcJxVX6B+6tGUODBfEl45qt5WDza/3wcn9iXAng+a0EE6UG9vgMsRfYvZNSrXaNH\n" \
   "PWSb6WiaxswbP7q+sos0Ai6YVRn8jG+qX9pMzk0DIaPY0jSTVpbLTAwAFjxfGs3I\n" \
   "x2ymrdMxp7zo5eFm1tL7A7RBZckQrg4FY8aAamkw/dLukO8NJ9+flXP04SXabBbe\n" \
   "QTg06ov80egEFGEtQX6sx3dOy1FU+16SGBsEWmjGycT6txOgmLcRK7fWV8x8nhfR\n" \
   "yyX+hk4kLlYMeE2eARKmK6cBZW58Yh2EhN/qwGu1pSqVg8NTEQxzHQuyRpDRQjrO\n" \
   "QG6Vrf/GlK1ul4SOfW+eioANSW1z4nuSHsPzwfPrLgVv2RvPN3YEyLRa5Beny912\n" \
   "H9AZdugsBbPWnDTYltxhh5EF5EQIM8HauQhl1K6yNg3ruji6DOWbnuuNZt2Zz9aJ\n" \
   "QfYEkoopKW1rOhzndX0CcQ7zwOe9yxndnWCywmZgtrEE7snmhrmaZkCo5xHtgUUD\n" \
   "i/ZnWejBBhG93c+AAk9lQHhcR1DIm+YfgXvkRKhbhZri3lrVx/k6RGZL5DJUfORs\n" \
   "nLMOPReisjQS1n6yqEm70XooQL6iFh/f5DcfEXP7kAplQ6INfPgGAVUzfbANuPT1\n" \
   "rqVCV3w2EYx7XsQDnYx5nQIDAQABo0IwQDAPBgNVHRMBAf8EBTADAQH/MA4GA1Ud\n" \
   "DwEB/wQEAwIBBjAdBgNVHQ4EFgQUtZn4r7CU9eMg1gqtzk5WpC5uQu0wDQYJKoZI\n" \
   "hvcNAQELBQADggIBACYGXnDnZTPIgm7ZnBc6G3pmsgH2eDtpXi/q/075KMOYKmFM\n" \
   "tCQSin1tERT3nLXK5ryeJ45MGcipvXrA1zYObYVybqjGom32+nNjf7xueQgcnYqf\n" \
   "GopTpti72TVVsRHFqQOzVju5hJMiXn7B9hJSi+osZ7z+Nkz1uM/Rs0mSO9MpDpkb\n" \
   "lvdhuDvEK7Z4bLQjb/D907JedR+Zlais9trhxTF7+9FGs9K8Z7RiVLoJ92Owk6Ka\n" \
   "+elSLotgEqv89WBW7xBci8QaQtyDW2QOy7W81k/BfDxujRNt+3vrMNDcTa/F1bal\n" \
   "TFtxyegxvug4BkihGuLq0t4SOVga/4AOgnXmt8kHbA7v/zjxmHHEt38OFdAlab0i\n" \
   "nSvtBfZGR6ztwPDUO+Ls7pZbkBNOHlY667DvlruWIxG68kOGdGSVyCh13x01utI3\n" \
   "gzhTODY7z2zp+WsO0PsE6E9312UBeIYMej4hYvF/Y3EMyZ9E26gnonW+boE+18Dr\n" \
   "G5gPcFw0sorMwIUY6256s/daoQe/qUKS82Ail+QUoQebTnbAjn39pCXHR+3/H3Os\n" \
   "zMOl6W8KjptlwlCFtaOgUxLMVYdh84GuEEZhvUQhuMI9dM9+JDX6HAcOmz0iyu8x\n" \
   "L4ysEr3vQCj8KWefshNPZiTEUxnpHikV7+ZtsH8tZ/3zbBt1RqPlShfppNcL\n" \
   "-----END CERTIFICATE-----\n" \
   "-----BEGIN CERTIFICATE-----\n" \
   "MIIDqDCCApCgAwIBAgIJAP7c4wEPyUj/MA0GCSqGSIb3DQEBBQUAMDQxCzAJBgNV\n" \
   "BAYTAkZSMRIwEAYDVQQKDAlEaGlteW90aXMxETAPBgNVBAMMCENlcnRpZ25hMB4X\n" \
   "DTA3MDYyOTE1MTMwNVoXDTI3MDYyOTE1MTMwNVowNDELMAkGA1UEBhMCRlIxEjAQ\n" \
   "BgNVBAoMCURoaW15b3RpczERMA8GA1UEAwwIQ2VydGlnbmEwggEiMA0GCSqGSIb3\n" \
   "DQEBAQUAA4IBDwAwggEKAoIBAQDIaPHJ1tazNHUmgh7stL7qXOEm7RFHYeGifBZ4\n" \
   "QCHkYJ5ayGPhxLGWkv8YbWkj4Sti993iNi+RB7lIzw7sebYs5zRLcAglozyHGxny\n" \
   "gQcPOJAZ0xH+hrTy0V4eHpbNgGzOOzGTtvKg0KmVEn2lmsxryIRWijOp5yIVUxbw\n" \
   "zBfsV1/pogqYCd7jX5xv3EjjhQsVWqa6n6xI4wmy9/Qy3l40vhx4XUJbzg4ij02Q\n" \
   "130yGLMLLGq/jj8UEYkgDncUtT2UCIf3JR7VsmAA7G8qKCVuKj4YYxclPz5EIBb2\n" \
   "JsglrgVKtOdjLPOMFlN+XPsRGgjBRmKfIrjxwo1p3Po6WAbfAgMBAAGjgbwwgbkw\n" \
   "DwYDVR0TAQH/BAUwAwEB/zAdBgNVHQ4EFgQUGu3+QTmQtCRZvgHyUtVF9lo53BEw\n" \
   "ZAYDVR0jBF0wW4AUGu3+QTmQtCRZvgHyUtVF9lo53BGhOKQ2MDQxCzAJBgNVBAYT\n" \
   "AkZSMRIwEAYDVQQKDAlEaGlteW90aXMxETAPBgNVBAMMCENlcnRpZ25hggkA/tzj\n" \
   "AQ/JSP8wDgYDVR0PAQH/BAQDAgEGMBEGCWCGSAGG+EIBAQQEAwIABzANBgkqhkiG\n" \
   "9w0BAQUFAAOCAQEAhQMeknH2Qq/ho2Ge6/PAD/Kl1NqV5ta+aDY9fm4fTIrv0Q8h\n" \
   "bV6lUmPOEvjvKtpv6zf+EwLHyzs+ImvaYS5/1HI93TDhHkxAGYwP15zRgzB7mFnc\n" \
   "fca5DClMoTOi62c6ZYTTluLtdkVwj7Ur3vkj1kluPBS1xp81HlDQwY9qcEQCYsuu\n" \
   "HWhBp6pX6FOqB9IG9tUUBguRA3UsbHK1YZWaDYu5Def131TN3ubY1gkIl2PlwS6w\n" \
   "t0QmwCbAr1UwnjvVNioZBPRcHv/PLLf/0P2HQBHVESO7SMAhqaQoLf0V+LBOK/Qw\n" \
   "WyH8EZE0vkHve52Xdf+XlcCWWC/qu0bXu+TZLg==\n" \
   "-----END CERTIFICATE-----\n" \
   "-----BEGIN CERTIFICATE-----\n" \
   "MIIFnDCCA4SgAwIBAgIBATANBgkqhkiG9w0BAQUFADBjMQswCQYDVQQGEwJGUjET\n" \
   "MBEGA1UEChMKQ2VydGlub21pczEXMBUGA1UECxMOMDAwMiA0MzM5OTg5MDMxJjAk\n" \
   "BgNVBAMMHUNlcnRpbm9taXMgLSBBdXRvcml0w6kgUmFjaW5lMB4XDTA4MDkxNzA4\n" \
   "Mjg1OVoXDTI4MDkxNzA4Mjg1OVowYzELMAkGA1UEBhMCRlIxEzARBgNVBAoTCkNl\n" \
   "cnRpbm9taXMxFzAVBgNVBAsTDjAwMDIgNDMzOTk4OTAzMSYwJAYDVQQDDB1DZXJ0\n" \
   "aW5vbWlzIC0gQXV0b3JpdMOpIFJhY2luZTCCAiIwDQYJKoZIhvcNAQEBBQADggIP\n" \
   "ADCCAgoCggIBAJ2Fn4bT46/HsmtuM+Cet0I0VZ35gb5j2CN2DpdUzZlMGvE5x4jY\n" \
   "F1AMnmHawE5V3udauHpOd4cN5bjr+p5eex7Ezyh0x5P1FMYiKAT5kcOrJ3NqDi5N\n" \
   "8y4oH3DfVS9O7cdxbwlyLu3VMpfQ8Vh30WC8Tl7bmoT2R2FFK/ZQpn9qcSdIhDWe\n" \
   "rP5pqZ56XjUl+rSnSTV3lqc2W+HN3yNw2F1MpQiD8aYkOBOo7C+ooWfHpi2GR+6K\n" \
   "/OybDnT0K0kCe5B1jPyZOQE51kqJ5Z52qz6WKDgmi92NjMD2AR5vpTESOH2VwnHu\n" \
   "7XSu5DaiQ3XV8QCb4uTXzEIDS3h65X27uK4uIJPT5GHfceF2Z5c/tt9qc1pkIuVC\n" \
   "28+BA5PY9OMQ4HL2AHCs8MF6DwV/zzRpRbWT5BnbUhYjBYkOjUjkJW+zeL9i9Qf6\n" \
   "lSTClrLooyPCXQP8w9PlfMl1I9f09bze5N/NgL+RiH2nE7Q5uiy6vdFrzPOlKO1E\n" \
   "nn1So2+WLhl+HPNbxxaOu2B9d2ZHVIIAEWBsMsGoOBvrbpgT1u449fCfDu/+MYHB\n" \
   "0iSVL1N6aaLwD4ZFjliCK0wi1F6g530mJ0jfJUaNSih8hp75mxpZuWW/Bd22Ql09\n" \
   "5gBIgl4g9xGC3srYn+Y3RyYe63j3YcNBZFgCQfna4NH4+ej9Uji29YnfAgMBAAGj\n" \
   "WzBZMA8GA1UdEwEB/wQFMAMBAf8wDgYDVR0PAQH/BAQDAgEGMB0GA1UdDgQWBBQN\n" \
   "jLZh2kS40RR9w759XkjwzspqsDAXBgNVHSAEEDAOMAwGCiqBegFWAgIAAQEwDQYJ\n" \
   "KoZIhvcNAQEFBQADggIBACQ+YAZ+He86PtvqrxyaLAEL9MW12Ukx9F1BjYkMTv9s\n" \
   "ov3/4gbIOZ/xWqndIlgVqIrTseYyCYIDbNc/CMf4uboAbbnW/FIyXaR/pDGUu7ZM\n" \
   "OH8oMDX/nyNTt7buFHAAQCvaR6s0fl6nVjBhK4tDrP22iCj1a7Y+YEq6QpA0Z43q\n" \
   "619FVDsXrIvkxmUP7tCMXWY5zjKn2BCXwH40nJ+U8/aGH88bc62UeYdocMMzpXDn\n" \
   "2NU4lG9jeeu/Cg4I58UvD0KgKxRA/yHgBcUn4YQRE7rWhh1BCxMjidPJC+iKunqj\n" \
   "o3M3NYB9Ergzd0A4wPpeMNLytqOx1qKVl4GbUu1pTP+A5FPbVFsDbVRfsbjvJL1v\n" \
   "nxHDx2TCDyhihWZeGnuyt++uNckZM6i4J9szVb9o4XVIRFb7zdNIu0eJOqxp9YDG\n" \
   "5ERQL1TEqkPFMTFYvZbF6nVsmnWxTfj3l/+WFvKXTej28xH5On2KOG4Ey+HTRRWq\n" \
   "pdEdnV1j6CTmNhTih60bWfVEm/vXd3wfAXBioSAaosUaKPQhA+4u2cGA6rnZgtZb\n" \
   "dsLLO7XSAPCjDuGtbkD326C00EauFddEwk01+dIL8hf2rGbVJLJP0RyZwG71fet0\n" \
   "BLj5TXcJ17TPBzAJ8bgAVtkXFhYKK4bfjwEZGuW7gmP/vgt2Fl43N+bYdJeimUV5\n" \
   "-----END CERTIFICATE-----\n" \
   "-----BEGIN CERTIFICATE-----\n" \
   "MIIFkjCCA3qgAwIBAgIBATANBgkqhkiG9w0BAQsFADBaMQswCQYDVQQGEwJGUjET\n" \
   "MBEGA1UEChMKQ2VydGlub21pczEXMBUGA1UECxMOMDAwMiA0MzM5OTg5MDMxHTAb\n" \
   "BgNVBAMTFENlcnRpbm9taXMgLSBSb290IENBMB4XDTEzMTAyMTA5MTcxOFoXDTMz\n" \
   "MTAyMTA5MTcxOFowWjELMAkGA1UEBhMCRlIxEzARBgNVBAoTCkNlcnRpbm9taXMx\n" \
   "FzAVBgNVBAsTDjAwMDIgNDMzOTk4OTAzMR0wGwYDVQQDExRDZXJ0aW5vbWlzIC0g\n" \
   "Um9vdCBDQTCCAiIwDQYJKoZIhvcNAQEBBQADggIPADCCAgoCggIBANTMCQosP5L2\n" \
   "fxSeC5yaah1AMGT9qt8OHgZbn1CF6s2Nq0Nn3rD6foCWnoR4kkjW4znuzuRZWJfl\n" \
   "LieY6pOod5tK8O90gC3rMB+12ceAnGInkYjwSond3IjmFPnVAy//ldu9n+ws+hQV\n" \
   "WZUKxkd8aRi5pwP5ynapz8dvtF4F/u7BUrJ1Mofs7SlmO/NKFoL21prbcpjp3vDF\n" \
   "TKWrteoB4owuZH9kb/2jJZOLyKIOSY008B/sWEUuNKqEUL3nskoTuLAPrjhdsKkb\n" \
   "5nPJWqHZZkCqqU2mNAKthH6yI8H7KsZn9DS2sJVqM09xRLWtwHkziOC/7aOgFLSc\n" \
   "CbAK42C++PhmiM1b8XcF4LVzbsF9Ri6OSyemzTUK/eVNfaoqoynHWmgE6OXWk6Ri\n" \
   "wsXm9E/G+Z8ajYJJGYrKWUM66A0ywfRMEwNvbqY/kXPLynNvEiCL7sCCeN5LLsJJ\n" \
   "wx3tFvYk9CcbXFcx3FXuqB5vbKziRcxXV4p1VxngtViZSTYxPDMBbRZKzbgqg4SG\n" \
   "m/lg0h9tkQPTYKbVPZrdd5A9NaSfD171UkRpucC63M9933zZxKyGIjK8e2uR73r4\n" \
   "F2iw4lNVYC2vPsKD2NkJK/DAZNuHi5HMkesE/Xa0lZrmFAYb1TQdvtj/dBxThZng\n" \
   "WVJKYe2InmtJiUZ+IFrZ50rlau7SZRFDAgMBAAGjYzBhMA4GA1UdDwEB/wQEAwIB\n" \
   "BjAPBgNVHRMBAf8EBTADAQH/MB0GA1UdDgQWBBTvkUz1pcMw6C8I6tNxIqSSaHh0\n" \
   "2TAfBgNVHSMEGDAWgBTvkUz1pcMw6C8I6tNxIqSSaHh02TANBgkqhkiG9w0BAQsF\n" \
   "AAOCAgEAfj1U2iJdGlg+O1QnurrMyOMaauo++RLrVl89UM7g6kgmJs95Vn6RHJk/\n" \
   "0KGRHCwPT5iVWVO90CLYiF2cN/z7ZMF4jIuaYAnq1fohX9B0ZedQxb8uuQsLrbWw\n" \
   "F6YSjNRieOpWauwK0kDDPAUwPk2Ut59KA9N9J0u2/kTO+hkzGm2kQtHdzMjI1xZS\n" \
   "g081lLMSVX3l4kLr5JyTCcBMWwerx20RoFAXlCOotQqSD7J6wWAsOMwaplv/8gzj\n" \
   "qh8c3LigkyfeY+N/IZ865Z764BNqdeuWXGKRlI5nU7aJ+BIJy29SWwNyhlCVCNSN\n" \
   "h4YVH5Uk2KRvms6knZtt0rJ2BobGVgjF6wnaNsIbW0G+YSrjcOa4pvi2WsS9Iff/\n" \
   "ql+hbHY5ZtbqTFXhADObE5hjyW/QASAJN1LnDE8+zbz1X5YnpyACleAu6AdBBR8V\n" \
   "btaw5BngDwKTACdyxYvRVB9dSsNAl35VpnzBMwQUAR1JIGkLGZOdblgi90AMRgwj\n" \
   "Y/M50n92Uaf0yKHxDHYiI0ZSKS3io0EHVmmY0gUJvGnHWmHNj4FgFU2A3ZDifcRQ\n" \
   "8ow7bkrHxuaAKzyBvBGAFhAn1/DNP3nMcyrDflOR1m749fPH0FFNjkulW+YZFzvW\n" \
   "gQncItzujrnEj1PhZ7szuIgVRs/taTX/dQ1G885x4cVrhkIGuUE=\n" \
   "-----END CERTIFICATE-----\n" \
   "-----BEGIN CERTIFICATE-----\n" \
   "MIIFazCCA1OgAwIBAgISESBVg+QtPlRWhS2DN7cs3EYRMA0GCSqGSIb3DQEBDQUA\n" \
   "MD4xCzAJBgNVBAYTAkZSMREwDwYDVQQKDAhDZXJ0cGx1czEcMBoGA1UEAwwTQ2Vy\n" \
   "dHBsdXMgUm9vdCBDQSBHMTAeFw0xNDA1MjYwMDAwMDBaFw0zODAxMTUwMDAwMDBa\n" \
   "MD4xCzAJBgNVBAYTAkZSMREwDwYDVQQKDAhDZXJ0cGx1czEcMBoGA1UEAwwTQ2Vy\n" \
   "dHBsdXMgUm9vdCBDQSBHMTCCAiIwDQYJKoZIhvcNAQEBBQADggIPADCCAgoCggIB\n" \
   "ANpQh7bauKk+nWT6VjOaVj0W5QOVsjQcmm1iBdTYj+eJZJ+622SLZOZ5KmHNr49a\n" \
   "iZFluVj8tANfkT8tEBXgfs+8/H9DZ6itXjYj2JizTfNDnjl8KvzsiNWI7nC9hRYt\n" \
   "6kuJPKNxQv4c/dMcLRC4hlTqQ7jbxofaqK6AJc96Jh2qkbBIb6613p7Y1/oA/caP\n" \
   "0FG7Yn2ksYyy/yARujVjBYZHYEMzkPZHogNPlk2dT8Hq6pyi/jQu3rfKG3akt62f\n" \
   "6ajUeD94/vI4CTYd0hYCyOwqaK/1jpTvLRN6HkJKHRUxrgwEV/xhc/MxVoYxgKDE\n" \
   "EW4wduOU8F8ExKyHcomYxZ3MVwia9Az8fXoFOvpHgDm2z4QTd28n6v+WZxcIbekN\n" \
   "1iNQMLAVdBM+5S//Ds3EC0pd8NgAM0lm66EYfFkuPSi5YXHLtaW6uOrc4nBvCGrc\n" \
   "h2c0798wct3zyT8j/zXhviEpIDCB5BmlIOklynMxdCm+4kLV87ImZsdo/Rmz5yCT\n" \
   "mehd4F6H50boJZwKKSTUzViGUkAksnsPmBIgJPaQbEfIDbsYIC7Z/fyL8inqh3SV\n" \
   "4EJQeIQEQWGw9CEjjy3LKCHyamz0GqbFFLQ3ZU+V/YDI+HLlJWvEYLF7bY5KinPO\n" \
   "WftwenMGE9nTdDckQQoRb5fc5+R+ob0V8rqHDz1oihYHAgMBAAGjYzBhMA4GA1Ud\n" \
   "DwEB/wQEAwIBBjAPBgNVHRMBAf8EBTADAQH/MB0GA1UdDgQWBBSowcCbkahDFXxd\n" \
   "Bie0KlHYlwuBsTAfBgNVHSMEGDAWgBSowcCbkahDFXxdBie0KlHYlwuBsTANBgkq\n" \
   "hkiG9w0BAQ0FAAOCAgEAnFZvAX7RvUz1isbwJh/k4DgYzDLDKTudQSk0YcbX8ACh\n" \
   "66Ryj5QXvBMsdbRX7gp8CXrc1cqh0DQT+Hern+X+2B50ioUHj3/MeXrKls3N/U/7\n" \
   "/SMNkPX0XtPGYX2eEeAC7gkE2Qfdpoq3DIMku4NQkv5gdRE+2J2winq14J2by5BS\n" \
   "S7CTKtQ+FjPlnsZlFT5kOwQ/2wyPX1wdaR+v8+khjPPvl/aatxm2hHSco1S1cE5j\n" \
   "2FddUyGbQJJD+tZ3VTNPZNX70Cxqjm0lpu+F6ALEUz65noe8zDUa3qHpimOHZR4R\n" \
   "Kttjd5cUvpoUmRGywO6wT/gUITJDT5+rosuoD6o7BlXGEilXCNQ314cnrUlZp5Gr\n" \
   "RHpejXDbl85IULFzk/bwg2D5zfHhMf1bfHEhYxQUqq/F3pN+aLHsIqKqkHWetUNy\n" \
   "6mSjhEv9DKgma3GX7lZjZuhCVPnHHd/Qj1vfyDBviP4NxDMcU6ij/UgQ8uQKTuEV\n" \
   "V/xuZDDCVRHc6qnNSlSsKWNEz0pAoNZoWRsz+e86i9sgktxChL8Bq4fA1SCC28a5\n" \
   "g4VCXA9DO2pJNdWY9BW/+mGBDAkgGNLQFwzLSABQ6XaCjGTXOqAHVcweMcDvOrRl\n" \
   "++O/QmueD6i9a5jc2NvLi6Td11n0bt3+qsOR0C5CB8AMTVPNJLFMWx5R9N/pkvo=\n" \
   "-----END CERTIFICATE-----\n" \
   "-----BEGIN CERTIFICATE-----\n" \
   "MIICHDCCAaKgAwIBAgISESDZkc6uo+jF5//pAq/Pc7xVMAoGCCqGSM49BAMDMD4x\n" \
   "CzAJBgNVBAYTAkZSMREwDwYDVQQKDAhDZXJ0cGx1czEcMBoGA1UEAwwTQ2VydHBs\n" \
   "dXMgUm9vdCBDQSBHMjAeFw0xNDA1MjYwMDAwMDBaFw0zODAxMTUwMDAwMDBaMD4x\n" \
   "CzAJBgNVBAYTAkZSMREwDwYDVQQKDAhDZXJ0cGx1czEcMBoGA1UEAwwTQ2VydHBs\n" \
   "dXMgUm9vdCBDQSBHMjB2MBAGByqGSM49AgEGBSuBBAAiA2IABM0PW1aC3/BFGtat\n" \
   "93nwHcmsltaeTpwftEIRyoa/bfuFo8XlGVzX7qY/aWfYeOKmycTbLXku54uNAm8x\n" \
   "Ik0G42ByRZ0OQneezs/lf4WbGOT8zC5y0xaTTsqZY1yhBSpsBqNjMGEwDgYDVR0P\n" \
   "AQH/BAQDAgEGMA8GA1UdEwEB/wQFMAMBAf8wHQYDVR0OBBYEFNqDYwJ5jtpMxjwj\n" \
   "FNiPwyCrKGBZMB8GA1UdIwQYMBaAFNqDYwJ5jtpMxjwjFNiPwyCrKGBZMAoGCCqG\n" \
   "SM49BAMDA2gAMGUCMHD+sAvZ94OX7PNVHdTcswYO/jOYnYs5kGuUIe22113WTNch\n" \
   "p+e/IQ8rzfcq3IUHnQIxAIYUFuXcsGXCwI4Un78kFmjlvPl5adytRSv3tjFzzAal\n" \
   "U5ORGpOucGpnutee5WEaXw==\n" \
   "-----END CERTIFICATE-----\n" \
   "-----BEGIN CERTIFICATE-----\n" \
   "MIIDODCCAiCgAwIBAgIGIAYFFnACMA0GCSqGSIb3DQEBBQUAMDsxCzAJBgNVBAYT\n" \
   "AlJPMREwDwYDVQQKEwhjZXJ0U0lHTjEZMBcGA1UECxMQY2VydFNJR04gUk9PVCBD\n" \
   "QTAeFw0wNjA3MDQxNzIwMDRaFw0zMTA3MDQxNzIwMDRaMDsxCzAJBgNVBAYTAlJP\n" \
   "MREwDwYDVQQKEwhjZXJ0U0lHTjEZMBcGA1UECxMQY2VydFNJR04gUk9PVCBDQTCC\n" \
   "ASIwDQYJKoZIhvcNAQEBBQADggEPADCCAQoCggEBALczuX7IJUqOtdu0KBuqV5Do\n" \
   "0SLTZLrTk+jUrIZhQGpgV2hUhE28alQCBf/fm5oqrl0Hj0rDKH/v+yv6efHHrfAQ\n" \
   "UySQi2bJqIirr1qjAOm+ukbuW3N7LBeCgV5iLKECZbO9xSsAfsT8AzNXDe3i+s5d\n" \
   "RdY4zTW2ssHQnIFKquSyAVwdj1+ZxLGt24gh65AIgoDzMKND5pCCrlUoSe1b16kQ\n" \
   "OA7+j0xbm0bqQfWwCHTD0IgztnzXdN/chNFDDnU5oSVAKOp4yw4sLjmdjItuFhwv\n" \
   "JoIQ4uNllAoEwF73XVv4EOLQunpL+943AAAaWyjj0pxzPjKHmKHJUS/X3qwzs08C\n" \
   "AwEAAaNCMEAwDwYDVR0TAQH/BAUwAwEB/zAOBgNVHQ8BAf8EBAMCAcYwHQYDVR0O\n" \
   "BBYEFOCMm9slSbPxfIbWskKHC9BroNnkMA0GCSqGSIb3DQEBBQUAA4IBAQA+0hyJ\n" \
   "LjX8+HXd5n9liPRyTMks1zJO890ZeUe9jjtbkw9QSSQTaxQGcu8J06Gh40CEyecY\n" \
   "MnQ8SG4Pn0vU9x7Tk4ZkVJdjclDVVc/6IJMCopvDI5NOFlV2oHB5bc0hH88vLbwZ\n" \
   "44gx+FkagQnIl6Z0x2DEW8xXjrJ1/RsCCdtZb3KTafcxQdaIOL+Hsr0Wefmq5L6I\n" \
   "Jd1hJyMctTEHBDa0GpC9oHRxUIltvBTjD4au8as+x6AJzKNI0eDbZOeStc+vckNw\n" \
   "i/nDhDwTqn6Sm1dTk/pwwpEOMfmbZ13pljheX7NzTogVZ96edhBiIL5VaZVDADlN\n" \
   "9u6wWk5JRFRYX0KD\n" \
   "-----END CERTIFICATE-----\n" \
   "-----BEGIN CERTIFICATE-----\n" \
   "MIIDDDCCAfSgAwIBAgIDAQAgMA0GCSqGSIb3DQEBBQUAMD4xCzAJBgNVBAYTAlBM\n" \
   "MRswGQYDVQQKExJVbml6ZXRvIFNwLiB6IG8uby4xEjAQBgNVBAMTCUNlcnR1bSBD\n" \
   "QTAeFw0wMjA2MTExMDQ2MzlaFw0yNzA2MTExMDQ2MzlaMD4xCzAJBgNVBAYTAlBM\n" \
   "MRswGQYDVQQKExJVbml6ZXRvIFNwLiB6IG8uby4xEjAQBgNVBAMTCUNlcnR1bSBD\n" \
   "QTCCASIwDQYJKoZIhvcNAQEBBQADggEPADCCAQoCggEBAM6xwS7TT3zNJc4YPk/E\n" \
   "jG+AanPIW1H4m9LcuwBcsaD8dQPugfCI7iNS6eYVM42sLQnFdvkrOYCJ5JdLkKWo\n" \
   "ePhzQ3ukYbDYWMzhbGZ+nPMJXlVjhNWo7/OxLjBos8Q82KxujZlakE403Daaj4GI\n" \
   "ULdtlkIJ89eVgw1BS7Bqa/j8D35in2fE7SZfECYPCE/wpFcozo+47UX2bu4lXapu\n" \
   "Ob7kky/ZR6By6/qmW6/KUz/iDsaWVhFu9+lmqSbYf5VT7QqFiLpPKaVCjF62/IUg\n" \
   "AKpoC6EahQGcxEZjgoi2IrHu/qpGWX7PNSzVttpd90gzFFS269lvzs2I1qsb2pY7\n" \
   "HVkCAwEAAaMTMBEwDwYDVR0TAQH/BAUwAwEB/zANBgkqhkiG9w0BAQUFAAOCAQEA\n" \
   "uI3O7+cUus/usESSbLQ5PqKEbq24IXfS1HeCh+YgQYHu4vgRt2PRFze+GXYkHAQa\n" \
   "TOs9qmdvLdTN/mUxcMUbpgIKumB7bVjCmkn+YzILa+M6wKyrO7Do0wlRjBCDxjTg\n" \
   "xSvgGrZgFCdsMneMvLJymM/NzD+5yCRCFNZX/OYmQ6kd5YCQzgNUKD73P9P4Te1q\n" \
   "CjqTE5s7FCMTY5w/0YcneeVMUeMBrYVdGjux1XMQpNPyvG5k9VpWkKjHDkx0Dy5x\n" \
   "O/fIR/RpbxXyEV6DHpx8Uq79AtoSqFlnGNu8cN2bsWntgM6JQEhqDjXKKWYVIZQs\n" \
   "6GAqm4VKQPNriiTsBhYscw==\n" \
   "-----END CERTIFICATE-----\n" \
   "-----BEGIN CERTIFICATE-----\n" \
   "MIIDuzCCAqOgAwIBAgIDBETAMA0GCSqGSIb3DQEBBQUAMH4xCzAJBgNVBAYTAlBM\n" \
   "MSIwIAYDVQQKExlVbml6ZXRvIFRlY2hub2xvZ2llcyBTLkEuMScwJQYDVQQLEx5D\n" \
   "ZXJ0dW0gQ2VydGlmaWNhdGlvbiBBdXRob3JpdHkxIjAgBgNVBAMTGUNlcnR1bSBU\n" \
   "cnVzdGVkIE5ldHdvcmsgQ0EwHhcNMDgxMDIyMTIwNzM3WhcNMjkxMjMxMTIwNzM3\n" \
   "WjB+MQswCQYDVQQGEwJQTDEiMCAGA1UEChMZVW5pemV0byBUZWNobm9sb2dpZXMg\n" \
   "Uy5BLjEnMCUGA1UECxMeQ2VydHVtIENlcnRpZmljYXRpb24gQXV0aG9yaXR5MSIw\n" \
   "IAYDVQQDExlDZXJ0dW0gVHJ1c3RlZCBOZXR3b3JrIENBMIIBIjANBgkqhkiG9w0B\n" \
   "AQEFAAOCAQ8AMIIBCgKCAQEA4/t9o3K6wvDJFIf1awFO4W5AB7ptJ11/91sts1rH\n" \
   "UV+rpDKmYYe2bg+G0jACl/jXaVehGDldamR5xgFZrDwxSjh80gTSSyjoIF87B6LM\n" \
   "TXPb865Px1bVWqeWifrzq2jUI4ZZJ88JJ7ysbnKDHDBy3+Ci6dLhdHUZvSqeexVU\n" \
   "BBvXQzmtVSjF4hq79MDkrjhJM8x2hZ85RdKknvISjFH4fOQtf/WsX+sWn7Et0brM\n" \
   "kUJ3TCXJkDhv2/DM+44el1k+1WBO5gUo7Ul5E0u6SNsv+XLTOcr+H9g0cvW0QM8x\n" \
   "AcPs3hEtF10fuFDRXhmnad4HMyjKUJX5p1TLVIZQRan5SQIDAQABo0IwQDAPBgNV\n" \
   "HRMBAf8EBTADAQH/MB0GA1UdDgQWBBQIds3LB/8k9sXN7buQvOKEN0Z19zAOBgNV\n" \
   "HQ8BAf8EBAMCAQYwDQYJKoZIhvcNAQEFBQADggEBAKaorSLOAT2mo/9i0Eidi15y\n" \
   "sHhE49wcrwn9I0j6vSrEuVUEtRCjjSfeC4Jj0O7eDDd5QVsisrCaQVymcODU0HfL\n" \
   "I9MA4GxWL+FpDQ3Zqr8hgVDZBqWo/5U30Kr+4rP1mS1FhIrlQgnXdAIv94nYmem8\n" \
   "J9RHjboNRhx3zxSkHLmkMcScKHQDNP8zGSal6Q10tz6XxnboJ5ajZt3hrvJBW8qY\n" \
   "VoNzcOSGGtIxQbovvi0TWnZvTuhOgQ4/WwMioBK+ZlgRSssDxLQqKi2WF+A5VLxI\n" \
   "03YnnZotBqbJ7DnSq9ufmgsnAjUpsUCV5/nonFWIGUbWtzT1fs45mtk48VH3Tyw=\n" \
   "-----END CERTIFICATE-----\n" \
   "-----BEGIN CERTIFICATE-----\n" \
   "MIIF0jCCA7qgAwIBAgIQIdbQSk8lD8kyN/yqXhKN6TANBgkqhkiG9w0BAQ0FADCB\n" \
   "gDELMAkGA1UEBhMCUEwxIjAgBgNVBAoTGVVuaXpldG8gVGVjaG5vbG9naWVzIFMu\n" \
   "QS4xJzAlBgNVBAsTHkNlcnR1bSBDZXJ0aWZpY2F0aW9uIEF1dGhvcml0eTEkMCIG\n" \
   "A1UEAxMbQ2VydHVtIFRydXN0ZWQgTmV0d29yayBDQSAyMCIYDzIwMTExMDA2MDgz\n" \
   "OTU2WhgPMjA0NjEwMDYwODM5NTZaMIGAMQswCQYDVQQGEwJQTDEiMCAGA1UEChMZ\n" \
   "VW5pemV0byBUZWNobm9sb2dpZXMgUy5BLjEnMCUGA1UECxMeQ2VydHVtIENlcnRp\n" \
   "ZmljYXRpb24gQXV0aG9yaXR5MSQwIgYDVQQDExtDZXJ0dW0gVHJ1c3RlZCBOZXR3\n" \
   "b3JrIENBIDIwggIiMA0GCSqGSIb3DQEBAQUAA4ICDwAwggIKAoICAQC9+Xj45tWA\n" \
   "DGSdhhuWZGc/IjoedQF97/tcZ4zJzFxrqZHmuULlIEub2pt7uZld2ZuAS9eEQCsn\n" \
   "0+i6MLs+CRqnSZXvK0AkwpfHp+6bJe+oCgCXhVqqndwpyeI1B+twTUrWwbNWuKFB\n" \
   "OJvR+zF/j+Bf4bE/D44WSWDXBo0Y+aomEKsq09DRZ40bRr5HMNUuctHFY9rnY3lE\n" \
   "fktjJImGLjQ/KUxSiyqnwOKRKIm5wFv5HdnnJ63/mgKXwcZQkpsCLL2puTRZCr+E\n" \
   "Sv/f/rOf69me4Jgj7KZrdxYq28ytOxykh9xGc14ZYmhFV+SQgkK7QtbwYeDBoz1m\n" \
   "o130GO6IyY0XRSmZMnUCMe4pJshrAua1YkV/NxVaI2iJ1D7eTiew8EAMvE0Xy02i\n" \
   "sx7QBlrd9pPPV3WZ9fqGGmd4s7+W/jTcvedSVuWz5XV710GRBdxdaeOVDUO5/IOW\n" \
   "OZV7bIBaTxNyxtd9KXpEulKkKtVBRgkg/iKgtlswjbyJDNXXcPiHUv3a76xRLgez\n" \
   "Tv7QCdpw75j6VuZt27VXS9zlLCUVyJ4ueE742pyehizKV/Ma5ciSixqClnrDvFAS\n" \
   "adgOWkaLOusm+iPJtrCBvkIApPjW/jAux9JG9uWOdf3yzLnQh1vMBhBgu4M1t15n\n" \
   "3kfsmUjxpKEV/q2MYo45VU85FrmxY53/twIDAQABo0IwQDAPBgNVHRMBAf8EBTAD\n" \
   "AQH/MB0GA1UdDgQWBBS2oVQ5AsOgP46KvPrU+Bym0ToO/TAOBgNVHQ8BAf8EBAMC\n" \
   "AQYwDQYJKoZIhvcNAQENBQADggIBAHGlDs7k6b8/ONWJWsQCYftMxRQXLYtPU2sQ\n" \
   "F/xlhMcQSZDe28cmk4gmb3DWAl45oPePq5a1pRNcgRRtDoGCERuKTsZPpd1iHkTf\n" \
   "CVn0W3cLN+mLIMb4Ck4uWBzrM9DPhmDJ2vuAL55MYIR4PSFk1vtBHxgP58l1cb29\n" \
   "XN40hz5BsA72udY/CROWFC/emh1auVbONTqwX3BNXuMp8SMoclm2q8KMZiYcdywm\n" \
   "djWLKKdpoPk79SPdhRB0yZADVpHnr7pH1BKXESLjokmUbOe3lEu6LaTaM4tMpkT/\n" \
   "WjzGHWTYtTHkpjx6qFcL2+1hGsvxznN3Y6SHb0xRONbkX8eftoEq5IVIeVheO/jb\n" \
   "AoJnwTnbw3RLPTYe+SmTiGhbqEQZIfCn6IENLOiTNrQ3ssqwGyZ6miUfmpqAnksq\n" \
   "P/ujmv5zMnHCnsZy4YpoJ/HkD7TETKVhk/iXEAcqMCWpuchxuO9ozC1+9eB+D4Ko\n" \
   "b7a6bINDd82Kkhehnlt4Fj1F4jNy3eFmypnTycUm/Q1oBEauttmbjL4ZvrHG8hnj\n" \
   "XALKLNhvSgfZyTXaQHXyxKcZb55CEJh15pWLYLztxRLXis7VmFxWlgPF7ncGNf/P\n" \
   "5O4/E2Hu29othfDNrp2yGAlFw5Khchf8R7agCyzxxN5DaAhqXzvwdmP7zAYspsbi\n" \
   "DrW5viSP\n" \
   "-----END CERTIFICATE-----\n" \
   "-----BEGIN CERTIFICATE-----\n" \
   "MIIFjTCCA3WgAwIBAgIEGErM1jANBgkqhkiG9w0BAQsFADBWMQswCQYDVQQGEwJD\n" \
   "TjEwMC4GA1UECgwnQ2hpbmEgRmluYW5jaWFsIENlcnRpZmljYXRpb24gQXV0aG9y\n" \
   "aXR5MRUwEwYDVQQDDAxDRkNBIEVWIFJPT1QwHhcNMTIwODA4MDMwNzAxWhcNMjkx\n" \
   "MjMxMDMwNzAxWjBWMQswCQYDVQQGEwJDTjEwMC4GA1UECgwnQ2hpbmEgRmluYW5j\n" \
   "aWFsIENlcnRpZmljYXRpb24gQXV0aG9yaXR5MRUwEwYDVQQDDAxDRkNBIEVWIFJP\n" \
   "T1QwggIiMA0GCSqGSIb3DQEBAQUAA4ICDwAwggIKAoICAQDXXWvNED8fBVnVBU03\n" \
   "sQ7smCuOFR36k0sXgiFxEFLXUWRwFsJVaU2OFW2fvwwbwuCjZ9YMrM8irq93VCpL\n" \
   "TIpTUnrD7i7es3ElweldPe6hL6P3KjzJIx1qqx2hp/Hz7KDVRM8Vz3IvHWOX6Jn5\n" \
   "/ZOkVIBMUtRSqy5J35DNuF++P96hyk0g1CXohClTt7GIH//62pCfCqktQT+x8Rgp\n" \
   "7hZZLDRJGqgG16iI0gNyejLi6mhNbiyWZXvKWfry4t3uMCz7zEasxGPrb382KzRz\n" \
   "EpR/38wmnvFyXVBlWY9ps4deMm/DGIq1lY+wejfeWkU7xzbh72fROdOXW3NiGUgt\n" \
   "hxwG+3SYIElz8AXSG7Ggo7cbcNOIabla1jj0Ytwli3i/+Oh+uFzJlU9fpy25IGvP\n" \
   "a931DfSCt/SyZi4QKPaXWnuWFo8BGS1sbn85WAZkgwGDg8NNkt0yxoekN+kWzqot\n" \
   "aK8KgWU6cMGbrU1tVMoqLUuFG7OA5nBFDWteNfB/O7ic5ARwiRIlk9oKmSJgamNg\n" \
   "TnYGmE69g60dWIolhdLHZR4tjsbftsbhf4oEIRUpdPA+nJCdDC7xij5aqgwJHsfV\n" \
   "PKPtl8MeNPo4+QgO48BdK4PRVmrJtqhUUy54Mmc9gn900PvhtgVguXDbjgv5E1hv\n" \
   "cWAQUhC5wUEJ73IfZzF4/5YFjQIDAQABo2MwYTAfBgNVHSMEGDAWgBTj/i39KNAL\n" \
   "tbq2osS/BqoFjJP7LzAPBgNVHRMBAf8EBTADAQH/MA4GA1UdDwEB/wQEAwIBBjAd\n" \
   "BgNVHQ4EFgQU4/4t/SjQC7W6tqLEvwaqBYyT+y8wDQYJKoZIhvcNAQELBQADggIB\n" \
   "ACXGumvrh8vegjmWPfBEp2uEcwPenStPuiB/vHiyz5ewG5zz13ku9Ui20vsXiObT\n" \
   "ej/tUxPQ4i9qecsAIyjmHjdXNYmEwnZPNDatZ8POQQaIxffu2Bq41gt/UP+TqhdL\n" \
   "jOztUmCypAbqTuv0axn96/Ua4CUqmtzHQTb3yHQFhDmVOdYLO6Qn+gjYXB74BGBS\n" \
   "ESgoA//vU2YApUo0FmZ8/Qmkrp5nGm9BC2sGE5uPhnEFtC+NiWYzKXZUmhH4J/qy\n" \
   "P5Hgzg0b8zAarb8iXRvTvyUFTeGSGn+ZnzxEk8rUQElsgIfXBDrDMlI1Dlb4pd19\n" \
   "xIsNER9Tyx6yF7Zod1rg1MvIB671Oi6ON7fQAUtDKXeMOZePglr4UeWJoBjnaH9d\n" \
   "Ci77o0cOPaYjesYBx4/IXr9tgFa+iiS6M+qf4TIRnvHST4D2G0CvOJ4RUHlzEhLN\n" \
   "5mydLIhyPDCBBpEi6lmt2hkuIsKNuYyH4Ga8cyNfIWRjgEj1oDwYPZTISEEdQLpe\n" \
   "/v5WOaHIz16eGWRGENoXkbcFgKyLmZJ956LYBws2J+dIeWCKw9cTXPhyQN9Ky8+Z\n" \
   "AAoACxGV2lZFA4gKn2fQ1XmxqI1AbQ3CekD6819kR5LLU7m7Wc5P/dAVUwHY3+vZ\n" \
   "5nbv0CO7O6l5s9UCKc2Jo5YPSjXnTkLAdc0Hz+Ys63su\n" \
   "-----END CERTIFICATE-----\n" \
   "-----BEGIN CERTIFICATE-----\n" \
   "MIIEvTCCA6WgAwIBAgIBADANBgkqhkiG9w0BAQUFADB/MQswCQYDVQQGEwJFVTEn\n" \
   "MCUGA1UEChMeQUMgQ2FtZXJmaXJtYSBTQSBDSUYgQTgyNzQzMjg3MSMwIQYDVQQL\n" \
   "ExpodHRwOi8vd3d3LmNoYW1iZXJzaWduLm9yZzEiMCAGA1UEAxMZQ2hhbWJlcnMg\n" \
   "b2YgQ29tbWVyY2UgUm9vdDAeFw0wMzA5MzAxNjEzNDNaFw0zNzA5MzAxNjEzNDRa\n" \
   "MH8xCzAJBgNVBAYTAkVVMScwJQYDVQQKEx5BQyBDYW1lcmZpcm1hIFNBIENJRiBB\n" \
   "ODI3NDMyODcxIzAhBgNVBAsTGmh0dHA6Ly93d3cuY2hhbWJlcnNpZ24ub3JnMSIw\n" \
   "IAYDVQQDExlDaGFtYmVycyBvZiBDb21tZXJjZSBSb290MIIBIDANBgkqhkiG9w0B\n" \
   "AQEFAAOCAQ0AMIIBCAKCAQEAtzZV5aVdGDDg2olUkfzIx1L4L1DZ77F1c2VHfRtb\n" \
   "unXF/KGIJPov7coISjlUxFF6tdpg6jg8gbLL8bvZkSM/SAFwdakFKq0fcfPJVD0d\n" \
   "BmpAPrMMhe5cG3nCYsS4No41XQEMIwRHNaqbYE6gZj3LJgqcQKH0XZi/caulAGgq\n" \
   "7YN6D6IUtdQis4CwPAxaUWktWBiP7Zme8a7ileb2R6jWDA+wWFjbw2Y3npuRVDM3\n" \
   "0pQcakjJyfKl2qUMI/cjDpwyVV5xnIQFUZot/eZOKjRa3spAN2cMVCFVd9oKDMyX\n" \
   "roDclDZK9D7ONhMeU+SsTjoF7Nuucpw4i9A5O4kKPnf+dQIBA6OCAUQwggFAMBIG\n" \
   "A1UdEwEB/wQIMAYBAf8CAQwwPAYDVR0fBDUwMzAxoC+gLYYraHR0cDovL2NybC5j\n" \
   "aGFtYmVyc2lnbi5vcmcvY2hhbWJlcnNyb290LmNybDAdBgNVHQ4EFgQU45T1sU3p\n" \
   "26EpW1eLTXYGduHRooowDgYDVR0PAQH/BAQDAgEGMBEGCWCGSAGG+EIBAQQEAwIA\n" \
   "BzAnBgNVHREEIDAegRxjaGFtYmVyc3Jvb3RAY2hhbWJlcnNpZ24ub3JnMCcGA1Ud\n" \
   "EgQgMB6BHGNoYW1iZXJzcm9vdEBjaGFtYmVyc2lnbi5vcmcwWAYDVR0gBFEwTzBN\n" \
   "BgsrBgEEAYGHLgoDATA+MDwGCCsGAQUFBwIBFjBodHRwOi8vY3BzLmNoYW1iZXJz\n" \
   "aWduLm9yZy9jcHMvY2hhbWJlcnNyb290Lmh0bWwwDQYJKoZIhvcNAQEFBQADggEB\n" \
   "AAxBl8IahsAifJ/7kPMa0QOx7xP5IV8EnNrJpY0nbJaHkb5BkAFyk+cefV/2icZd\n" \
   "p0AJPaxJRUXcLo0waLIJuvvDL8y6C98/d3tGfToSJI6WjzwFCm/SlCgdbQzALogi\n" \
   "1djPHRPH8EjX1wWnz8dHnjs8NMiAT9QUu/wNUPf6s+xCX6ndbcj0dc97wXImsQEc\n" \
   "XCz9ek60AcUFV7nnPKoF2YjpB0ZBzu9Bga5Y34OirsrXdx/nADydb47kMgkdTXg0\n" \
   "eDQ8lJsm7U9xxhl6vSAiSFr+S30Dt+dYvsYyTnQeaN2oaFuzPu5ifdmA6Ap1erfu\n" \
   "tGWaIZDgqtCYvDi1czyL+Nw=\n" \
   "-----END CERTIFICATE-----\n" \
   "-----BEGIN CERTIFICATE-----\n" \
   "MIIHTzCCBTegAwIBAgIJAKPaQn6ksa7aMA0GCSqGSIb3DQEBBQUAMIGuMQswCQYD\n" \
   "VQQGEwJFVTFDMEEGA1UEBxM6TWFkcmlkIChzZWUgY3VycmVudCBhZGRyZXNzIGF0\n" \
   "IHd3dy5jYW1lcmZpcm1hLmNvbS9hZGRyZXNzKTESMBAGA1UEBRMJQTgyNzQzMjg3\n" \
   "MRswGQYDVQQKExJBQyBDYW1lcmZpcm1hIFMuQS4xKTAnBgNVBAMTIENoYW1iZXJz\n" \
   "IG9mIENvbW1lcmNlIFJvb3QgLSAyMDA4MB4XDTA4MDgwMTEyMjk1MFoXDTM4MDcz\n" \
   "MTEyMjk1MFowga4xCzAJBgNVBAYTAkVVMUMwQQYDVQQHEzpNYWRyaWQgKHNlZSBj\n" \
   "dXJyZW50IGFkZHJlc3MgYXQgd3d3LmNhbWVyZmlybWEuY29tL2FkZHJlc3MpMRIw\n" \
   "EAYDVQQFEwlBODI3NDMyODcxGzAZBgNVBAoTEkFDIENhbWVyZmlybWEgUy5BLjEp\n" \
   "MCcGA1UEAxMgQ2hhbWJlcnMgb2YgQ29tbWVyY2UgUm9vdCAtIDIwMDgwggIiMA0G\n" \
   "CSqGSIb3DQEBAQUAA4ICDwAwggIKAoICAQCvAMtwNyuAWko6bHiUfaN/Gh/2NdW9\n" \
   "28sNRHI+JrKQUrpjOyhYb6WzbZSm891kDFX29ufyIiKAXuFixrYp4YFs8r/lfTJq\n" \
   "VKAyGVn+H4vXPWCGhSRv4xGzdz4gljUha7MI2XAuZPeEklPWDrCQiorjh40G072Q\n" \
   "DuKZoRuGDtqaCrsLYVAGUvGef3bsyw/QHg3PmTA9HMRFEFis1tPo1+XqxQEHd9ZR\n" \
   "5gN/ikilTWh1uem8nk4ZcfUyS5xtYBkL+8ydddy/Js2Pk3g5eXNeJQ7KXOt3EgfL\n" \
   "ZEFHcpOrUMPrCXZkNNI5t3YRCQ12RcSprj1qr7V9ZS+UWBDsXHyvfuK2GNnQm05a\n" \
   "Sd+pZgvMPMZ4fKecHePOjlO+Bd5gD2vlGts/4+EhySnB8esHnFIbAURRPHsl18Tl\n" \
   "UlRdJQfKFiC4reRB7noI/plvg6aRArBsNlVq5331lubKgdaX8ZSD6e2wsWsSaR6s\n" \
   "+12pxZjptFtYer49okQ6Y1nUCyXeG0+95QGezdIp1Z8XGQpvvwyQ0wlf2eOKNcx5\n" \
   "Wk0ZN5K3xMGtr/R5JJqyAQuxr1yW84Ay+1w9mPGgP0revq+ULtlVmhduYJ1jbLhj\n" \
   "ya6BXBg14JC7vjxPNyK5fuvPnnchpj04gftI2jE9K+OJ9dC1vX7gUMQSibMjmhAx\n" \
   "hduub+84Mxh2EQIDAQABo4IBbDCCAWgwEgYDVR0TAQH/BAgwBgEB/wIBDDAdBgNV\n" \
   "HQ4EFgQU+SSsD7K1+HnA+mCIG8TZTQKeFxkwgeMGA1UdIwSB2zCB2IAU+SSsD7K1\n" \
   "+HnA+mCIG8TZTQKeFxmhgbSkgbEwga4xCzAJBgNVBAYTAkVVMUMwQQYDVQQHEzpN\n" \
   "YWRyaWQgKHNlZSBjdXJyZW50IGFkZHJlc3MgYXQgd3d3LmNhbWVyZmlybWEuY29t\n" \
   "L2FkZHJlc3MpMRIwEAYDVQQFEwlBODI3NDMyODcxGzAZBgNVBAoTEkFDIENhbWVy\n" \
   "ZmlybWEgUy5BLjEpMCcGA1UEAxMgQ2hhbWJlcnMgb2YgQ29tbWVyY2UgUm9vdCAt\n" \
   "IDIwMDiCCQCj2kJ+pLGu2jAOBgNVHQ8BAf8EBAMCAQYwPQYDVR0gBDYwNDAyBgRV\n" \
   "HSAAMCowKAYIKwYBBQUHAgEWHGh0dHA6Ly9wb2xpY3kuY2FtZXJmaXJtYS5jb20w\n" \
   "DQYJKoZIhvcNAQEFBQADggIBAJASryI1wqM58C7e6bXpeHxIvj99RZJe6dqxGfwW\n" \
   "PJ+0W2aeaufDuV2I6A+tzyMP3iU6XsxPpcG1Lawk0lgH3qLPaYRgM+gQDROpI9CF\n" \
   "5Y57pp49chNyM/WqfcZjHwj0/gF/JM8rLFQJ3uIrbZLGOU8W6jx+ekbURWpGqOt1\n" \
   "glanq6B8aBMz9p0w8G8nOSQjKpD9kCk18pPfNKXG9/jvjA9iSnyu0/VU+I22mlaH\n" \
   "FoI6M6taIgj3grrqLuBHmrS1RaMFO9ncLkVAO+rcf+g769HsJtg1pDDFOqxXnrN2\n" \
   "pSB7+R5KBWIBpih1YJeSDW4+TTdDDZIVnBgizVGZoCkaPF+KMjNbMMeJL0eYD6MD\n" \
   "xvbxrN8y8NmBGuScvfaAFPDRLLmF9dijscilIeUcE5fuDr3fKanvNFNb0+RqE4QG\n" \
   "tjICxFKuItLcsiFCGtpA8CnJ7AoMXOLQusxI0zcKzBIKinmwPQN/aUv0NCB9szTq\n" \
   "jktk9T79syNnFQ0EuPAtwQlRPLJsFfClI9eDdOTlLsn+mCdCxqvGnrDQWzilm1De\n" \
   "fhiYtUU79nm06PcaewaD+9CL2rvHvRirCG88gGtAPxkZumWK5r7VXNM21+9AUiRg\n" \
   "OGcEMeyP84LG3rlV8zsxkVrctQgVrXYlCg17LofiDKYGvCYQbTed7N14jHyAxfDZ\n" \
   "d0jQ\n" \
   "-----END CERTIFICATE-----\n" \
   "-----BEGIN CERTIFICATE-----\n" \
   "MIIDQzCCAiugAwIBAgIQX/h7KCtU3I1CoxW1aMmt/zANBgkqhkiG9w0BAQUFADA1\n" \
   "MRYwFAYDVQQKEw1DaXNjbyBTeXN0ZW1zMRswGQYDVQQDExJDaXNjbyBSb290IENB\n" \
   "IDIwNDgwHhcNMDQwNTE0MjAxNzEyWhcNMjkwNTE0MjAyNTQyWjA1MRYwFAYDVQQK\n" \
   "Ew1DaXNjbyBTeXN0ZW1zMRswGQYDVQQDExJDaXNjbyBSb290IENBIDIwNDgwggEg\n" \
   "MA0GCSqGSIb3DQEBAQUAA4IBDQAwggEIAoIBAQCwmrmrp68Kd6ficba0ZmKUeIhH\n" \
   "xmJVhEAyv8CrLqUccda8bnuoqrpu0hWISEWdovyD0My5jOAmaHBKeN8hF570YQXJ\n" \
   "FcjPFto1YYmUQ6iEqDGYeJu5Tm8sUxJszR2tKyS7McQr/4NEb7Y9JHcJ6r8qqB9q\n" \
   "VvYgDxFUl4F1pyXOWWqCZe+36ufijXWLbvLdT6ZeYpzPEApk0E5tzivMW/VgpSdH\n" \
   "jWn0f84bcN5wGyDWbs2mAag8EtKpP6BrXruOIIt6keO1aO6g58QBdKhTCytKmg9l\n" \
   "Eg6CTY5j/e/rmxrbU6YTYK/CfdfHbBcl1HP7R2RQgYCUTOG/rksc35LtLgXfAgED\n" \
   "o1EwTzALBgNVHQ8EBAMCAYYwDwYDVR0TAQH/BAUwAwEB/zAdBgNVHQ4EFgQUJ/PI\n" \
   "FR5umgIJFq0roIlgX9p7L6owEAYJKwYBBAGCNxUBBAMCAQAwDQYJKoZIhvcNAQEF\n" \
   "BQADggEBAJ2dhISjQal8dwy3U8pORFBi71R803UXHOjgxkhLtv5MOhmBVrBW7hmW\n" \
   "Yqpao2TB9k5UM8Z3/sUcuuVdJcr18JOagxEu5sv4dEX+5wW4q+ffy0vhN4TauYuX\n" \
   "cB7w4ovXsNgOnbFp1iqRe6lJT37mjpXYgyc81WhJDtSd9i7rp77rMKSsH0T8lasz\n" \
   "Bvt9YAretIpjsJyp8qS5UwGH0GikJ3+r/+n6yUA4iGe0OcaEb1fJU9u6ju7AQ7L4\n" \
   "CYNu/2bPPu8Xs1gYJQk0XuPL1hS27PKSb3TkL4Eq1ZKR4OCXPDJoBYVL0fdX4lId\n" \
   "kxpUnwVwwEpxYB5DC2Ae/qPOgRnhCzU=\n" \
   "-----END CERTIFICATE-----\n" \
   "-----BEGIN CERTIFICATE-----\n" \
   "MIIEHTCCAwWgAwIBAgIQToEtioJl4AsC7j41AkblPTANBgkqhkiG9w0BAQUFADCB\n" \
   "gTELMAkGA1UEBhMCR0IxGzAZBgNVBAgTEkdyZWF0ZXIgTWFuY2hlc3RlcjEQMA4G\n" \
   "A1UEBxMHU2FsZm9yZDEaMBgGA1UEChMRQ09NT0RPIENBIExpbWl0ZWQxJzAlBgNV\n" \
   "BAMTHkNPTU9ETyBDZXJ0aWZpY2F0aW9uIEF1dGhvcml0eTAeFw0wNjEyMDEwMDAw\n" \
   "MDBaFw0yOTEyMzEyMzU5NTlaMIGBMQswCQYDVQQGEwJHQjEbMBkGA1UECBMSR3Jl\n" \
   "YXRlciBNYW5jaGVzdGVyMRAwDgYDVQQHEwdTYWxmb3JkMRowGAYDVQQKExFDT01P\n" \
   "RE8gQ0EgTGltaXRlZDEnMCUGA1UEAxMeQ09NT0RPIENlcnRpZmljYXRpb24gQXV0\n" \
   "aG9yaXR5MIIBIjANBgkqhkiG9w0BAQEFAAOCAQ8AMIIBCgKCAQEA0ECLi3LjkRv3\n" \
   "UcEbVASY06m/weaKXTuH+7uIzg3jLz8GlvCiKVCZrts7oVewdFFxze1CkU1B/qnI\n" \
   "2GqGd0S7WWaXUF601CxwRM/aN5VCaTwwxHGzUvAhTaHYujl8HJ6jJJ3ygxaYqhZ8\n" \
   "Q5sVW7euNJH+1GImGEaaP+vB+fGQV+useg2L23IwambV4EajcNxo2f8ESIl33rXp\n" \
   "+2dtQem8Ob0y2WIC8bGoPW43nOIv4tOiJovGuFVDiOEjPqXSJDlqR6sA1KGzqSX+\n" \
   "DT+nHbrTUcELpNqsOO9VUCQFZUaTNE8tja3G1CEZ0o7KBWFxB3NH5YoZEr0ETc5O\n" \
   "nKVIrLsm9wIDAQABo4GOMIGLMB0GA1UdDgQWBBQLWOWLxkwVN6RAqTCpIb5HNlpW\n" \
   "/zAOBgNVHQ8BAf8EBAMCAQYwDwYDVR0TAQH/BAUwAwEB/zBJBgNVHR8EQjBAMD6g\n" \
   "PKA6hjhodHRwOi8vY3JsLmNvbW9kb2NhLmNvbS9DT01PRE9DZXJ0aWZpY2F0aW9u\n" \
   "QXV0aG9yaXR5LmNybDANBgkqhkiG9w0BAQUFAAOCAQEAPpiem/Yb6dc5t3iuHXIY\n" \
   "SdOH5EOC6z/JqvWote9VfCFSZfnVDeFs9D6Mk3ORLgLETgdxb8CPOGEIqB6BCsAv\n" \
   "IC9Bi5HcSEW88cbeunZrM8gALTFGTO3nnc+IlP8zwFboJIYmuNg4ON8qa90SzMc/\n" \
   "RxdMosIGlgnW2/4/PEZB31jiVg88O8EckzXZOFKs7sjsLjBOlDW0JB9LeGna8gI4\n" \
   "zJVSk/BwJVmcIGfE7vmLV2H0knZ9P4SNVbfo5azV8fUZVqZa+5Acr5Pr5RzUZ5dd\n" \
   "BA6+C4OmF4O5MBKgxTMVBbkN+8cFduPYSo38NBejxiEovjBFMR7HeL5YYTisO+IB\n" \
   "ZQ==\n" \
   "-----END CERTIFICATE-----\n" \
   "-----BEGIN CERTIFICATE-----\n" \
   "MIICiTCCAg+gAwIBAgIQH0evqmIAcFBUTAGem2OZKjAKBggqhkjOPQQDAzCBhTEL\n" \
   "MAkGA1UEBhMCR0IxGzAZBgNVBAgTEkdyZWF0ZXIgTWFuY2hlc3RlcjEQMA4GA1UE\n" \
   "BxMHU2FsZm9yZDEaMBgGA1UEChMRQ09NT0RPIENBIExpbWl0ZWQxKzApBgNVBAMT\n" \
   "IkNPTU9ETyBFQ0MgQ2VydGlmaWNhdGlvbiBBdXRob3JpdHkwHhcNMDgwMzA2MDAw\n" \
   "MDAwWhcNMzgwMTE4MjM1OTU5WjCBhTELMAkGA1UEBhMCR0IxGzAZBgNVBAgTEkdy\n" \
   "ZWF0ZXIgTWFuY2hlc3RlcjEQMA4GA1UEBxMHU2FsZm9yZDEaMBgGA1UEChMRQ09N\n" \
   "T0RPIENBIExpbWl0ZWQxKzApBgNVBAMTIkNPTU9ETyBFQ0MgQ2VydGlmaWNhdGlv\n" \
   "biBBdXRob3JpdHkwdjAQBgcqhkjOPQIBBgUrgQQAIgNiAAQDR3svdcmCFYX7deSR\n" \
   "FtSrYpn1PlILBs5BAH+X4QokPB0BBO490o0JlwzgdeT6+3eKKvUDYEs2ixYjFq0J\n" \
   "cfRK9ChQtP6IHG4/bC8vCVlbpVsLM5niwz2J+Wos77LTBumjQjBAMB0GA1UdDgQW\n" \
   "BBR1cacZSBm8nZ3qQUfflMRId5nTeTAOBgNVHQ8BAf8EBAMCAQYwDwYDVR0TAQH/\n" \
   "BAUwAwEB/zAKBggqhkjOPQQDAwNoADBlAjEA7wNbeqy3eApyt4jf/7VGFAkK+qDm\n" \
   "fQjGGoe9GKhzvSbKYAydzpmfz1wPMOG+FDHqAjAU9JM8SaczepBGR7NjfRObTrdv\n" \
   "GDeAU/7dIOA1mjbRxwG55tzd8/8dLDoWV9mSOdY=\n" \
   "-----END CERTIFICATE-----\n" \
   "-----BEGIN CERTIFICATE-----\n" \
   "MIIF2DCCA8CgAwIBAgIQTKr5yttjb+Af907YWwOGnTANBgkqhkiG9w0BAQwFADCB\n" \
   "hTELMAkGA1UEBhMCR0IxGzAZBgNVBAgTEkdyZWF0ZXIgTWFuY2hlc3RlcjEQMA4G\n" \
   "A1UEBxMHU2FsZm9yZDEaMBgGA1UEChMRQ09NT0RPIENBIExpbWl0ZWQxKzApBgNV\n" \
   "BAMTIkNPTU9ETyBSU0EgQ2VydGlmaWNhdGlvbiBBdXRob3JpdHkwHhcNMTAwMTE5\n" \
   "MDAwMDAwWhcNMzgwMTE4MjM1OTU5WjCBhTELMAkGA1UEBhMCR0IxGzAZBgNVBAgT\n" \
   "EkdyZWF0ZXIgTWFuY2hlc3RlcjEQMA4GA1UEBxMHU2FsZm9yZDEaMBgGA1UEChMR\n" \
   "Q09NT0RPIENBIExpbWl0ZWQxKzApBgNVBAMTIkNPTU9ETyBSU0EgQ2VydGlmaWNh\n" \
   "dGlvbiBBdXRob3JpdHkwggIiMA0GCSqGSIb3DQEBAQUAA4ICDwAwggIKAoICAQCR\n" \
   "6FSS0gpWsawNJN3Fz0RndJkrN6N9I3AAcbxT38T6KhKPS38QVr2fcHK3YX/JSw8X\n" \
   "pz3jsARh7v8Rl8f0hj4K+j5c+ZPmNHrZFGvnnLOFoIJ6dq9xkNfs/Q36nGz637CC\n" \
   "9BR++b7Epi9Pf5l/tfxnQ3K9DADWietrLNPtj5gcFKt+5eNu/Nio5JIk2kNrYrhV\n" \
   "/erBvGy2i/MOjZrkm2xpmfh4SDBF1a3hDTxFYPwyllEnvGfDyi62a+pGx8cgoLEf\n" \
   "Zd5ICLqkTqnyg0Y3hOvozIFIQ2dOciqbXL1MGyiKXCJ7tKuY2e7gUYPDCUZObT6Z\n" \
   "+pUX2nwzV0E8jVHtC7ZcryxjGt9XyD+86V3Em69FmeKjWiS0uqlWPc9vqv9JWL7w\n" \
   "qP/0uK3pN/u6uPQLOvnoQ0IeidiEyxPx2bvhiWC4jChWrBQdnArncevPDt09qZah\n" \
   "SL0896+1DSJMwBGB7FY79tOi4lu3sgQiUpWAk2nojkxl8ZEDLXB0AuqLZxUpaVIC\n" \
   "u9ffUGpVRr+goyhhf3DQw6KqLCGqR84onAZFdr+CGCe01a60y1Dma/RMhnEw6abf\n" \
   "Fobg2P9A3fvQQoh/ozM6LlweQRGBY84YcWsr7KaKtzFcOmpH4MN5WdYgGq/yapiq\n" \
   "crxXStJLnbsQ/LBMQeXtHT1eKJ2czL+zUdqnR+WEUwIDAQABo0IwQDAdBgNVHQ4E\n" \
   "FgQUu69+Aj36pvE8hI6t7jiY7NkyMtQwDgYDVR0PAQH/BAQDAgEGMA8GA1UdEwEB\n" \
   "/wQFMAMBAf8wDQYJKoZIhvcNAQEMBQADggIBAArx1UaEt65Ru2yyTUEUAJNMnMvl\n" \
   "wFTPoCWOAvn9sKIN9SCYPBMtrFaisNZ+EZLpLrqeLppysb0ZRGxhNaKatBYSaVqM\n" \
   "4dc+pBroLwP0rmEdEBsqpIt6xf4FpuHA1sj+nq6PK7o9mfjYcwlYRm6mnPTXJ9OV\n" \
   "2jeDchzTc+CiR5kDOF3VSXkAKRzH7JsgHAckaVd4sjn8OoSgtZx8jb8uk2Intzna\n" \
   "FxiuvTwJaP+EmzzV1gsD41eeFPfR60/IvYcjt7ZJQ3mFXLrrkguhxuhoqEwWsRqZ\n" \
   "CuhTLJK7oQkYdQxlqHvLI7cawiiFwxv/0Cti76R7CZGYZ4wUAc1oBmpjIXUDgIiK\n" \
   "boHGhfKppC3n9KUkEEeDys30jXlYsQab5xoq2Z0B15R97QNKyvDb6KkBPvVWmcke\n" \
   "jkk9u+UJueBPSZI9FoJAzMxZxuY67RIuaTxslbH9qh17f4a+Hg4yRvv7E491f0yL\n" \
   "S0Zj/gA0QHDBw7mh3aZw4gSzQbzpgJHqZJx64SIDqZxubw5lT2yHh17zbqD5daWb\n" \
   "QOhTsiedSrnAdyGN/4fy3ryM7xfft0kL0fJuMAsaDk527RH89elWsn2/x20Kk4yl\n" \
   "0MC2Hb46TpSi125sC8KKfPog88Tk5c0NqMuRkrF8hey1FGlmDoLnzc7ILaZRfyHB\n" \
   "NVOFBkpdn627G190\n" \
   "-----END CERTIFICATE-----\n" \
   "-----BEGIN CERTIFICATE-----\n" \
   "MIIDkzCCAnugAwIBAgIQFBOWgxRVjOp7Y+X8NId3RDANBgkqhkiG9w0BAQUFADA0\n" \
   "MRMwEQYDVQQDEwpDb21TaWduIENBMRAwDgYDVQQKEwdDb21TaWduMQswCQYDVQQG\n" \
   "EwJJTDAeFw0wNDAzMjQxMTMyMThaFw0yOTAzMTkxNTAyMThaMDQxEzARBgNVBAMT\n" \
   "CkNvbVNpZ24gQ0ExEDAOBgNVBAoTB0NvbVNpZ24xCzAJBgNVBAYTAklMMIIBIjAN\n" \
   "BgkqhkiG9w0BAQEFAAOCAQ8AMIIBCgKCAQEA8ORUaSvTx49qROR+WCf4C9DklBKK\n" \
   "8Rs4OC8fMZwG1Cyn3gsqrhqg455qv588x26i+YtkbDqthVVRVKU4VbirgwTyP2Q2\n" \
   "98CNQ0NqZtH3FyrV7zb6MBBC11PN+fozc0yz6YQgitZBJzXkOPqUm7h65HkfM/sb\n" \
   "2CEJKHxNGGleZIp6GZPKfuzzcuc3B1hZKKxC+cX/zT/npfo4sdAMx9lSGlPWgcxC\n" \
   "ejVb7Us6eva1jsz/D3zkYDaHL63woSV9/9JLEYhwVKZBqGdTUkJe5DSe5L6j7Kpi\n" \
   "Xd3DTKaCQeQzC6zJMw9kglcq/QytNuEMrkvF7zuZ2SOzW120V+x0cAwqTwIDAQAB\n" \
   "o4GgMIGdMAwGA1UdEwQFMAMBAf8wPQYDVR0fBDYwNDAyoDCgLoYsaHR0cDovL2Zl\n" \
   "ZGlyLmNvbXNpZ24uY28uaWwvY3JsL0NvbVNpZ25DQS5jcmwwDgYDVR0PAQH/BAQD\n" \
   "AgGGMB8GA1UdIwQYMBaAFEsBmz5WGmU2dst7l6qSBe4y5ygxMB0GA1UdDgQWBBRL\n" \
   "AZs+VhplNnbLe5eqkgXuMucoMTANBgkqhkiG9w0BAQUFAAOCAQEA0Nmlfv4pYEWd\n" \
   "foPPbrxHbvUanlR2QnG0PFg/LUAlQvaBnPGJEMgOqnhPOAlXsDzACPw1jvFIUY0M\n" \
   "cXS6hMTXcpuEfDhOZAYnKuGntewImbQKDdSFc8gS4TXt8QUxHXOZDOuWyt3T5oWq\n" \
   "8Ir7dcHyCTxlZWTzTNity4hp8+SDtwy9F1qWF8pb/627HOkthIDYIb6FUtnUdLlp\n" \
   "hbpN7Sgy6/lhSuTENh4Z3G+EER+V9YMoGKgzkkMn3V0TBEVPh9VGzT2ouvDzuFYk\n" \
   "Res3x+F2T3I5GN9+dHLHcy056mDmrRGiVod7w2ia/viMcKjfZTL0pECMocJEAw6U\n" \
   "AGegcQCCSA==\n" \
   "-----END CERTIFICATE-----\n" \
   "-----BEGIN CERTIFICATE-----\n" \
   "MIIGATCCA+mgAwIBAgIRAI9hcRW6eVgXjH0ROqzW264wDQYJKoZIhvcNAQELBQAw\n" \
   "RTEfMB0GA1UEAxMWQ29tU2lnbiBHbG9iYWwgUm9vdCBDQTEVMBMGA1UEChMMQ29t\n" \
   "U2lnbiBMdGQuMQswCQYDVQQGEwJJTDAeFw0xMTA3MTgxMDI0NTRaFw0zNjA3MTYx\n" \
   "MDI0NTVaMEUxHzAdBgNVBAMTFkNvbVNpZ24gR2xvYmFsIFJvb3QgQ0ExFTATBgNV\n" \
   "BAoTDENvbVNpZ24gTHRkLjELMAkGA1UEBhMCSUwwggIiMA0GCSqGSIb3DQEBAQUA\n" \
   "A4ICDwAwggIKAoICAQCyKClzKh3rm6n1nvigmV/VU1D4hSwYW2ro3VqpzpPo0Ph3\n" \
   "3LguqjXd5juDwN4mpxTpD99d7Xu5X6KGTlMVtfN+bTbA4t3x7DU0Zqn0BE5XuOgs\n" \
   "3GLH41Vmr5wox1bShVpM+IsjcN4E/hMnDtt/Bkb5s33xCG+ohz5dlq0gA9qfr/g4\n" \
   "O9lkHZXTCeYrmVzd/il4x79CqNvGkdL3um+OKYl8rg1dPtD8UsytMaDgBAopKR+W\n" \
   "igc16QJzCbvcinlETlrzP/Ny76BWPnAQgaYBULax/Q5thVU+N3sEOKp6uviTdD+X\n" \
   "O6i96gARU4H0xxPFI75PK/YdHrHjfjQevXl4J37FJfPMSHAbgPBhHC+qn/014DOx\n" \
   "46fEGXcdw2BFeIIIwbj2GH70VyJWmuk/xLMCHHpJ/nIF8w25BQtkPpkwESL6esaU\n" \
   "b1CyB4Vgjyf16/0nRiCAKAyC/DY/Yh+rDWtXK8c6QkXD2XamrVJo43DVNFqGZzbf\n" \
   "5bsUXqiVDOz71AxqqK+p4ek9374xPNMJ2rB5MLPAPycwI0bUuLHhLy6nAIFHLhut\n" \
   "TNI+6Y/soYpi5JSaEjcY7pxI8WIkUAzr2r+6UoT0vAdyOt7nt1y8844a7szo/aKf\n" \
   "woziHl2O1w6ZXUC30K+ptXVaOiW79pBDcbLZ9ZdbONhS7Ea3iH4HJNwktrBJLQID\n" \
   "AQABo4HrMIHoMA8GA1UdEwEB/wQFMAMBAf8wgYQGA1UdHwR9MHswPKA6oDiGNmh0\n" \
   "dHA6Ly9mZWRpci5jb21zaWduLmNvLmlsL2NybC9jb21zaWduZ2xvYmFscm9vdGNh\n" \
   "LmNybDA7oDmgN4Y1aHR0cDovL2NybDEuY29tc2lnbi5jby5pbC9jcmwvY29tc2ln\n" \
   "bmdsb2JhbHJvb3RjYS5jcmwwDgYDVR0PAQH/BAQDAgGGMB0GA1UdDgQWBBQCRZPY\n" \
   "DUhirGm6rgZbPvuqJpFQsTAfBgNVHSMEGDAWgBQCRZPYDUhirGm6rgZbPvuqJpFQ\n" \
   "sTANBgkqhkiG9w0BAQsFAAOCAgEAk1V5V9701xsfy4mfX+tP9Ln5e9h3N+QMwUfj\n" \
   "kr+k3e8iXOqADjTpUHeBkEee5tJq09ZLp/43F5tZ2eHdYq2ZEX7iWHCnOQet6Yw9\n" \
   "SU1TahsrGDA6JJD9sdPFnNZooGsU1520e0zNB0dNWwxrWAmu4RsBxvEpWCJbvzQL\n" \
   "dOfyX85RWwli81OiVMBc5XvJ1mxsIIqli45oRynKtsWP7E+b0ISJ1n+XFLdQo/Nm\n" \
   "WA/5sDfT0F5YPzWdZymudMbXitimxC+n4oQE4mbQ4Zm718Iwg3pP9gMMcSc7Qc1J\n" \
   "kJHPH9O7gVubkKHuSYj9T3Ym6c6egL1pb4pz/uT7cT26Fiopc/jdqbe2EAfoJZkv\n" \
   "hlp/zdzOoXTWjiKNA5zmgWnZn943FuE9KMRyKtyi/ezJXCh8ypnqLIKxeFfZl69C\n" \
   "BwJsPXUTuqj8Fic0s3aZmmr7C4jXycP+Q8V+akMEIoHAxcd960b4wVWKqOcI/kZS\n" \
   "Q0cYqWOY1LNjznRt9lweWEfwDBL3FhrHOmD4++1N3FkkM4W+Q1b2WOL24clDMj+i\n" \
   "2n9Iw0lc1llHMSMvA5D0vpsXZpOgcCVahfXczQKi9wQ3oZyonJeWx4/rXdMtagAB\n" \
   "VBYGFuMEUEQtybI+eIbnp5peO2WAAblQI4eTy/jMVowe5tfMEXovV3sz9ULgmGb3\n" \
   "DscLP1I=\n" \
   "-----END CERTIFICATE-----\n" \
   "-----BEGIN CERTIFICATE-----\n" \
   "MIIDqzCCApOgAwIBAgIRAMcoRwmzuGxFjB36JPU2TukwDQYJKoZIhvcNAQEFBQAw\n" \
   "PDEbMBkGA1UEAxMSQ29tU2lnbiBTZWN1cmVkIENBMRAwDgYDVQQKEwdDb21TaWdu\n" \
   "MQswCQYDVQQGEwJJTDAeFw0wNDAzMjQxMTM3MjBaFw0yOTAzMTYxNTA0NTZaMDwx\n" \
   "GzAZBgNVBAMTEkNvbVNpZ24gU2VjdXJlZCBDQTEQMA4GA1UEChMHQ29tU2lnbjEL\n" \
   "MAkGA1UEBhMCSUwwggEiMA0GCSqGSIb3DQEBAQUAA4IBDwAwggEKAoIBAQDGtWhf\n" \
   "HZQVw6QIVS3joFd67+l0Kru5fFdJGhFeTymHDEjWaueP1H5XJLkGieQcPOqs49oh\n" \
   "gHMhCu95mGwfCP+hUH3ymBvJVG8+pSjsIQQPRbsHPaHA+iqYHU4Gk/v1iDurX8sW\n" \
   "v+bznkqH7Rnqwp9D5PGBpX8QTz7RSmKtUxvLg/8HZaWSLWapW7ha9B20IZFKF3ue\n" \
   "Mv5WJDmyVIRD9YTC2LxBkMyd1mja6YJQqTtoz7VdApRgFrFD2UNd3V2Hbuq7s8lr\n" \
   "9gOUCXDeFhF6K+h2j0kQmHe5Y1yLM5d19guMsqtb3nQgJT/j8xH5h2iGNXHDHYwt\n" \
   "6+UarA9z1YJZQIDTAgMBAAGjgacwgaQwDAYDVR0TBAUwAwEB/zBEBgNVHR8EPTA7\n" \
   "MDmgN6A1hjNodHRwOi8vZmVkaXIuY29tc2lnbi5jby5pbC9jcmwvQ29tU2lnblNl\n" \
   "Y3VyZWRDQS5jcmwwDgYDVR0PAQH/BAQDAgGGMB8GA1UdIwQYMBaAFMFL7XC29z58\n" \
   "ADsAj8c+DkWfHl3sMB0GA1UdDgQWBBTBS+1wtvc+fAA7AI/HPg5Fnx5d7DANBgkq\n" \
   "hkiG9w0BAQUFAAOCAQEAFs/ukhNQq3sUnjO2QiBq1BW9Cav8cujvR3qQrFHBZE7p\n" \
   "iL1DRYHjZiM/EoZNGeQFsOY3wo3aBijJD4mkU6l1P7CW+6tMM1X5eCZGbxs2mPtC\n" \
   "dsGCuY7e+0X5YxtiOzkGynd6qDwJz2w2PQ8KRUtpFhpFfTMDZflScZAmlaxMDPWL\n" \
   "kz/MdXSFmLr/YnpNH4n+rr2UAJm/EaXc4HnFFgt9AmEd6oX5AhVP51qJThRv4zdL\n" \
   "hfXBPGHg/QVBspJ/wx2g0K5SZGBrGMYmnNj1ZOQ2GmKfig8+/21OGVZOIJFsnzQz\n" \
   "OjRXUDpvgV4GxvU+fE6OK85lBi5d0ipTdF7Tbieejw==\n" \
   "-----END CERTIFICATE-----\n" \
   "-----BEGIN CERTIFICATE-----\n" \
   "MIIEDjCCAvagAwIBAgIDD92sMA0GCSqGSIb3DQEBCwUAMEUxCzAJBgNVBAYTAkRF\n" \
   "MRUwEwYDVQQKDAxELVRydXN0IEdtYkgxHzAdBgNVBAMMFkQtVFJVU1QgUm9vdCBD\n" \
   "QSAzIDIwMTMwHhcNMTMwOTIwMDgyNTUxWhcNMjgwOTIwMDgyNTUxWjBFMQswCQYD\n" \
   "VQQGEwJERTEVMBMGA1UECgwMRC1UcnVzdCBHbWJIMR8wHQYDVQQDDBZELVRSVVNU\n" \
   "IFJvb3QgQ0EgMyAyMDEzMIIBIjANBgkqhkiG9w0BAQEFAAOCAQ8AMIIBCgKCAQEA\n" \
   "xHtCkoIf7O1UmI4SwMoJ35NuOpNcG+QQd55OaYhs9uFp8vabomGxvQcgdJhl8Ywm\n" \
   "CM2oNcqANtFjbehEeoLDbF7eu+g20sRoNoyfMr2EIuDcwu4QRjltr5M5rofmw7wJ\n" \
   "ySxrZ1vZm3Z1TAvgu8XXvD558l++0ZBX+a72Zl8xv9Ntj6e6SvMjZbu376Ml1wrq\n" \
   "WLbviPr6ebJSWNXwrIyhUXQplapRO5AyA58ccnSQ3j3tYdLl4/1kR+W5t0qp9x+u\n" \
   "loYErC/jpIF3t1oW/9gPP/a3eMykr/pbPBJbqFKJcu+I89VEgYaVI5973bzZNO98\n" \
   "lDyqwEHC451QGsDkGSL8swIDAQABo4IBBTCCAQEwDwYDVR0TAQH/BAUwAwEB/zAd\n" \
   "BgNVHQ4EFgQUP5DIfccVb/Mkj6nDL0uiDyGyL+cwDgYDVR0PAQH/BAQDAgEGMIG+\n" \
   "BgNVHR8EgbYwgbMwdKByoHCGbmxkYXA6Ly9kaXJlY3RvcnkuZC10cnVzdC5uZXQv\n" \
   "Q049RC1UUlVTVCUyMFJvb3QlMjBDQSUyMDMlMjAyMDEzLE89RC1UcnVzdCUyMEdt\n" \
   "YkgsQz1ERT9jZXJ0aWZpY2F0ZXJldm9jYXRpb25saXN0MDugOaA3hjVodHRwOi8v\n" \
   "Y3JsLmQtdHJ1c3QubmV0L2NybC9kLXRydXN0X3Jvb3RfY2FfM18yMDEzLmNybDAN\n" \
   "BgkqhkiG9w0BAQsFAAOCAQEADlkOWOR0SCNEzzQhtZwUGq2aS7eziG1cqRdw8Cqf\n" \
   "jXv5e4X6xznoEAiwNStfzwLS05zICx7uBVSuN5MECX1sj8J0vPgclL4xAUAt8yQg\n" \
   "t4RVLFzI9XRKEBmLo8ftNdYJSNMOwLo5qLBGArDbxohZwr78e7Erz35ih1WWzAFv\n" \
   "m2chlTWL+BD8cRu3SzdppjvW7IvuwbDzJcmPkn2h6sPKRL8mpXSSnON065102ctN\n" \
   "h9j8tGlsi6BDB2B4l+nZk3zCRrybN1Kj7Yo8E6l7U0tJmhEFLAtuVqwfLoJs4Gln\n" \
   "tQ5tLdnkwBXxP/oYcuEVbSdbLTAoK59ImmQrme/ydUlfXA==\n" \
   "-----END CERTIFICATE-----\n" \
   "-----BEGIN CERTIFICATE-----\n" \
   "MIIEMzCCAxugAwIBAgIDCYPzMA0GCSqGSIb3DQEBCwUAME0xCzAJBgNVBAYTAkRF\n" \
   "MRUwEwYDVQQKDAxELVRydXN0IEdtYkgxJzAlBgNVBAMMHkQtVFJVU1QgUm9vdCBD\n" \
   "bGFzcyAzIENBIDIgMjAwOTAeFw0wOTExMDUwODM1NThaFw0yOTExMDUwODM1NTha\n" \
   "ME0xCzAJBgNVBAYTAkRFMRUwEwYDVQQKDAxELVRydXN0IEdtYkgxJzAlBgNVBAMM\n" \
   "HkQtVFJVU1QgUm9vdCBDbGFzcyAzIENBIDIgMjAwOTCCASIwDQYJKoZIhvcNAQEB\n" \
   "BQADggEPADCCAQoCggEBANOySs96R+91myP6Oi/WUEWJNTrGa9v+2wBoqOADER03\n" \
   "UAifTUpolDWzU9GUY6cgVq/eUXjsKj3zSEhQPgrfRlWLJ23DEE0NkVJD2IfgXU42\n" \
   "tSHKXzlABF9bfsyjxiupQB7ZNoTWSPOSHjRGICTBpFGOShrvUD9pXRl/RcPHAY9R\n" \
   "ySPocq60vFYJfxLLHLGvKZAKyVXMD9O0Gu1HNVpK7ZxzBCHQqr0ME7UAyiZsxGsM\n" \
   "lFqVlNpQmvH/pStmMaTJOKDfHR+4CS7zp+hnUquVH+BGPtikw8paxTGA6Eian5Rp\n" \
   "/hnd2HN8gcqW3o7tszIFZYQ05ub9VxC1X3a/L7AQDcUCAwEAAaOCARowggEWMA8G\n" \
   "A1UdEwEB/wQFMAMBAf8wHQYDVR0OBBYEFP3aFMSfMN4hvR5COfyrYyNJ4PGEMA4G\n" \
   "A1UdDwEB/wQEAwIBBjCB0wYDVR0fBIHLMIHIMIGAoH6gfIZ6bGRhcDovL2RpcmVj\n" \
   "dG9yeS5kLXRydXN0Lm5ldC9DTj1ELVRSVVNUJTIwUm9vdCUyMENsYXNzJTIwMyUy\n" \
   "MENBJTIwMiUyMDIwMDksTz1ELVRydXN0JTIwR21iSCxDPURFP2NlcnRpZmljYXRl\n" \
   "cmV2b2NhdGlvbmxpc3QwQ6BBoD+GPWh0dHA6Ly93d3cuZC10cnVzdC5uZXQvY3Js\n" \
   "L2QtdHJ1c3Rfcm9vdF9jbGFzc18zX2NhXzJfMjAwOS5jcmwwDQYJKoZIhvcNAQEL\n" \
   "BQADggEBAH+X2zDI36ScfSF6gHDOFBJpiBSVYEQBrLLpME+bUMJm2H6NMLVwMeni\n" \
   "acfzcNsgFYbQDfC+rAF1hM5+n02/t2A7nPPKHeJeaNijnZflQGDSNiH+0LS4F9p0\n" \
   "o3/U37CYAqxva2ssJSRyoWXuJVrl5jLn8t+rSfrzkGkj2wTZ51xY/GXUl77M/C4K\n" \
   "zCUqNQT4YJEVdT1B/yMfGchs64JTBKbkTCJNjYy6zltz7GRUUG3RnFX7acM2w4y8\n" \
   "PIWmawomDeCTmGCufsYkl4phX5GOZpIJhzbNi5stPvZR1FDUWSi9g/LMKHtThm3Y\n" \
   "Johw1+qRzT65ysCQblrGXnRl11z+o+I=\n" \
   "-----END CERTIFICATE-----\n" \
   "-----BEGIN CERTIFICATE-----\n" \
   "MIIEQzCCAyugAwIBAgIDCYP0MA0GCSqGSIb3DQEBCwUAMFAxCzAJBgNVBAYTAkRF\n" \
   "MRUwEwYDVQQKDAxELVRydXN0IEdtYkgxKjAoBgNVBAMMIUQtVFJVU1QgUm9vdCBD\n" \
   "bGFzcyAzIENBIDIgRVYgMjAwOTAeFw0wOTExMDUwODUwNDZaFw0yOTExMDUwODUw\n" \
   "NDZaMFAxCzAJBgNVBAYTAkRFMRUwEwYDVQQKDAxELVRydXN0IEdtYkgxKjAoBgNV\n" \
   "BAMMIUQtVFJVU1QgUm9vdCBDbGFzcyAzIENBIDIgRVYgMjAwOTCCASIwDQYJKoZI\n" \
   "hvcNAQEBBQADggEPADCCAQoCggEBAJnxhDRwui+3MKCOvXwEz75ivJn9gpfSegpn\n" \
   "ljgJ9hBOlSJzmY3aFS3nBfwZcyK3jpgAvDw9rKFs+9Z5JUut8Mxk2og+KbgPCdM0\n" \
   "3TP1YtHhzRnp7hhPTFiu4h7WDFsVWtg6uMQYZB7jM7K1iXdODL/ZlGsTl28So/6Z\n" \
   "qQTMFexgaDbtCHu39b+T7WYxg4zGcTSHThfqr4uRjRxWQa4iN1438h3Z0S0NL2lR\n" \
   "p75mpoo6Kr3HGrHhFPC+Oh25z1uxav60sUYgovseO3Dvk5h9jHOW8sXvhXCtKSb8\n" \
   "HgQ+HKDYD8tSg2J87otTlZCpV6LqYQXY+U3EJ/pure3511H3a6UCAwEAAaOCASQw\n" \
   "ggEgMA8GA1UdEwEB/wQFMAMBAf8wHQYDVR0OBBYEFNOUikxiEyoZLsyvcop9Ntea\n" \
   "HNxnMA4GA1UdDwEB/wQEAwIBBjCB3QYDVR0fBIHVMIHSMIGHoIGEoIGBhn9sZGFw\n" \
   "Oi8vZGlyZWN0b3J5LmQtdHJ1c3QubmV0L0NOPUQtVFJVU1QlMjBSb290JTIwQ2xh\n" \
   "c3MlMjAzJTIwQ0ElMjAyJTIwRVYlMjAyMDA5LE89RC1UcnVzdCUyMEdtYkgsQz1E\n" \
   "RT9jZXJ0aWZpY2F0ZXJldm9jYXRpb25saXN0MEagRKBChkBodHRwOi8vd3d3LmQt\n" \
   "dHJ1c3QubmV0L2NybC9kLXRydXN0X3Jvb3RfY2xhc3NfM19jYV8yX2V2XzIwMDku\n" \
   "Y3JsMA0GCSqGSIb3DQEBCwUAA4IBAQA07XtaPKSUiO8aEXUHL7P+PPoeUSbrh/Yp\n" \
   "3uDx1MYkCenBz1UbtDDZzhr+BlGmFaQt77JLvyAoJUnRpjZ3NOhk31KxEcdzes05\n" \
   "nsKtjHEh8lprr988TlWvsoRlFIm5d8sqMb7Po23Pb0iUMkZv53GMoKaEGTcH8gNF\n" \
   "CSuGdXzfX2lXANtu2KZyIktQ1HWYVt+3GP9DQ1CuekR78HlR10M9p9OB0/DJT7na\n" \
   "xpeG0ILD5EJt/rDiZE4OJudANCa1CInXCGNjOCd1HjPqbqjdn5lPdE2BiYBL3ZqX\n" \
   "KVwvvoFBuYz/6n1gBp7N1z3TLqMVvKjmJuVvw9y4AyHqnxbxLFS1\n" \
   "-----END CERTIFICATE-----\n" \
   "-----BEGIN CERTIFICATE-----\n" \
   "MIIEBDCCAuygAwIBAgIIGHqpqMKWIQwwDQYJKoZIhvcNAQELBQAwYjELMAkGA1UE\n" \
   "BhMCVVMxEzARBgNVBAoTCkFwcGxlIEluYy4xJjAkBgNVBAsTHUFwcGxlIENlcnRp\n" \
   "ZmljYXRpb24gQXV0aG9yaXR5MRYwFAYDVQQDEw1BcHBsZSBSb290IENBMB4XDTEy\n" \
   "MDIwMTIyMTIxNVoXDTI3MDIwMTIyMTIxNVoweTEtMCsGA1UEAwwkRGV2ZWxvcGVy\n" \
   "IElEIENlcnRpZmljYXRpb24gQXV0aG9yaXR5MSYwJAYDVQQLDB1BcHBsZSBDZXJ0\n" \
   "aWZpY2F0aW9uIEF1dGhvcml0eTETMBEGA1UECgwKQXBwbGUgSW5jLjELMAkGA1UE\n" \
   "BhMCVVMwggEiMA0GCSqGSIb3DQEBAQUAA4IBDwAwggEKAoIBAQCJdk8GW5pB7qUj\n" \
   "KwKjX9dzP8A1sIuECj8GJH+nlT/rTw6Tr7QO0Mg+5W0Ysx/oiUe/1wkI5P9WmCkV\n" \
   "55SduTWjCs20wOHiYPTK7Cl4RWlpYGtfipL8niPmOsIiszFPHLrytjRZQu6wqQID\n" \
   "GJEEtrN4LjMfgEUNRW+7Dlpbfzrn2AjXCw4ybfuGNuRsq8QRinCEJqqfRNHxuMZ7\n" \
   "lBebSPcLWBa6I8WfFTl+yl3DMl8P4FJ/QOq+rAhklVvJGpzlgMofakQcbD7EsCYf\n" \
   "Hex7r16gaj1HqVgSMT8gdihtHRywwk4RaSaLy9bQEYLJTg/xVnTQ2QhLZniiq6yn\n" \
   "4tJMh1nJAgMBAAGjgaYwgaMwHQYDVR0OBBYEFFcX7aLP3HyYoRDg/L6HLSzy4xdU\n" \
   "MA8GA1UdEwEB/wQFMAMBAf8wHwYDVR0jBBgwFoAUK9BpR5R2Cf70a40uQKb3R01/\n" \
   "CF4wLgYDVR0fBCcwJTAjoCGgH4YdaHR0cDovL2NybC5hcHBsZS5jb20vcm9vdC5j\n" \
   "cmwwDgYDVR0PAQH/BAQDAgGGMBAGCiqGSIb3Y2QGAgYEAgUAMA0GCSqGSIb3DQEB\n" \
   "CwUAA4IBAQBCOXRrodzGpI83KoyzHQpEvJUsf7xZuKxh+weQkjK51L87wVA5akR0\n" \
   "ouxbH3Dlqt1LbBwjcS1f0cWTvu6binBlgp0W4xoQF4ktqM39DHhYSQwofzPuAHob\n" \
   "tHastrW7T9+oG53IGZdKC1ZnL8I+trPEgzrwd210xC4jUe6apQNvYPSlSKcGwrta\n" \
   "4h8fRkV+5Jf1JxC3ICJyb3LaxlB1xT0lj12jAOmfNoxIOY+zO+qQgC6VmmD0eM70\n" \
   "DgpTPqL6T9geroSVjTK8Vk2J6XgY4KyaQrp6RhuEoonOFOiI0ViL9q5WxCwFKkWv\n" \
   "C9lLqQIPNKyIx2FViUTJJ3MH7oLlTvVw\n" \
   "-----END CERTIFICATE-----\n" \
   "-----BEGIN CERTIFICATE-----\n" \
   "MIIDtzCCAp+gAwIBAgIQDOfg5RfYRv6P5WD8G/AwOTANBgkqhkiG9w0BAQUFADBl\n" \
   "MQswCQYDVQQGEwJVUzEVMBMGA1UEChMMRGlnaUNlcnQgSW5jMRkwFwYDVQQLExB3\n" \
   "d3cuZGlnaWNlcnQuY29tMSQwIgYDVQQDExtEaWdpQ2VydCBBc3N1cmVkIElEIFJv\n" \
   "b3QgQ0EwHhcNMDYxMTEwMDAwMDAwWhcNMzExMTEwMDAwMDAwWjBlMQswCQYDVQQG\n" \
   "EwJVUzEVMBMGA1UEChMMRGlnaUNlcnQgSW5jMRkwFwYDVQQLExB3d3cuZGlnaWNl\n" \
   "cnQuY29tMSQwIgYDVQQDExtEaWdpQ2VydCBBc3N1cmVkIElEIFJvb3QgQ0EwggEi\n" \
   "MA0GCSqGSIb3DQEBAQUAA4IBDwAwggEKAoIBAQCtDhXO5EOAXLGH87dg+XESpa7c\n" \
   "JpSIqvTO9SA5KFhgDPiA2qkVlTJhPLWxKISKityfCgyDF3qPkKyK53lTXDGEKvYP\n" \
   "mDI2dsze3Tyoou9q+yHyUmHfnyDXH+Kx2f4YZNISW1/5WBg1vEfNoTb5a3/UsDg+\n" \
   "wRvDjDPZ2C8Y/igPs6eD1sNuRMBhNZYW/lmci3Zt1/GiSw0r/wty2p5g0I6QNcZ4\n" \
   "VYcgoc/lbQrISXwxmDNsIumH0DJaoroTghHtORedmTpyoeb6pNnVFzF1roV9Iq4/\n" \
   "AUaG9ih5yLHa5FcXxH4cDrC0kqZWs72yl+2qp/C3xag/lRbQ/6GW6whfGHdPAgMB\n" \
   "AAGjYzBhMA4GA1UdDwEB/wQEAwIBhjAPBgNVHRMBAf8EBTADAQH/MB0GA1UdDgQW\n" \
   "BBRF66Kv9JLLgjEtUYunpyGd823IDzAfBgNVHSMEGDAWgBRF66Kv9JLLgjEtUYun\n" \
   "pyGd823IDzANBgkqhkiG9w0BAQUFAAOCAQEAog683+Lt8ONyc3pklL/3cmbYMuRC\n" \
   "dWKuh+vy1dneVrOfzM4UKLkNl2BcEkxY5NM9g0lFWJc1aRqoR+pWxnmrEthngYTf\n" \
   "fwk8lOa4JiwgvT2zKIn3X/8i4peEH+ll74fg38FnSbNd67IJKusm7Xi+fT8r87cm\n" \
   "NW1fiQG2SVufAQWbqz0lwcy2f8Lxb4bG+mRo64EtlOtCt/qMHt1i8b5QZ7dsvfPx\n" \
   "H2sMNgcWfzd8qVttevESRmCD1ycEvkvOl77DZypoEd+A5wwzZr8TDRRu838fYxAe\n" \
   "+o0bJW1sj6W3YQGx0qMmoRBxna3iw/nDmVG3KwcIzi7mULKn+gpFL6Lw8g==\n" \
   "-----END CERTIFICATE-----\n" \
   "-----BEGIN CERTIFICATE-----\n" \
   "MIIDljCCAn6gAwIBAgIQC5McOtY5Z+pnI7/Dr5r0SzANBgkqhkiG9w0BAQsFADBl\n" \
   "MQswCQYDVQQGEwJVUzEVMBMGA1UEChMMRGlnaUNlcnQgSW5jMRkwFwYDVQQLExB3\n" \
   "d3cuZGlnaWNlcnQuY29tMSQwIgYDVQQDExtEaWdpQ2VydCBBc3N1cmVkIElEIFJv\n" \
   "b3QgRzIwHhcNMTMwODAxMTIwMDAwWhcNMzgwMTE1MTIwMDAwWjBlMQswCQYDVQQG\n" \
   "EwJVUzEVMBMGA1UEChMMRGlnaUNlcnQgSW5jMRkwFwYDVQQLExB3d3cuZGlnaWNl\n" \
   "cnQuY29tMSQwIgYDVQQDExtEaWdpQ2VydCBBc3N1cmVkIElEIFJvb3QgRzIwggEi\n" \
   "MA0GCSqGSIb3DQEBAQUAA4IBDwAwggEKAoIBAQDZ5ygvUj82ckmIkzTz+GoeMVSA\n" \
   "n61UQbVH35ao1K+ALbkKz3X9iaV9JPrjIgwrvJUXCzO/GU1BBpAAvQxNEP4Htecc\n" \
   "biJVMWWXvdMX0h5i89vqbFCMP4QMls+3ywPgym2hFEwbid3tALBSfK+RbLE4E9Hp\n" \
   "EgjAALAcKxHad3A2m67OeYfcgnDmCXRwVWmvo2ifv922ebPynXApVfSr/5Vh88lA\n" \
   "bx3RvpO704gqu52/clpWcTs/1PPRCv4o76Pu2ZmvA9OPYLfykqGxvYmJHzDNw6Yu\n" \
   "YjOuFgJ3RFrngQo8p0Quebg/BLxcoIfhG69Rjs3sLPr4/m3wOnyqi+RnlTGNAgMB\n" \
   "AAGjQjBAMA8GA1UdEwEB/wQFMAMBAf8wDgYDVR0PAQH/BAQDAgGGMB0GA1UdDgQW\n" \
   "BBTOw0q5mVXyuNtgv6l+vVa1lzan1jANBgkqhkiG9w0BAQsFAAOCAQEAyqVVjOPI\n" \
   "QW5pJ6d1Ee88hjZv0p3GeDgdaZaikmkuOGybfQTUiaWxMTeKySHMq2zNixya1r9I\n" \
   "0jJmwYrA8y8678Dj1JGG0VDjA9tzd29KOVPt3ibHtX2vK0LRdWLjSisCx1BL4Gni\n" \
   "lmwORGYQRI+tBev4eaymG+g3NJ1TyWGqolKvSnAWhsI6yLETcDbYz+70CjTVW0z9\n" \
   "B5yiutkBclzzTcHdDrEcDcRjvq30FPuJ7KJBDkzMyFdA0G4Dqs0MjomZmWzwPDCv\n" \
   "ON9vvKO+KSAnq3T/EyJ43pdSVR6DtVQgA+6uwE9W3jfMw3+qBCe703e4YtsXfJwo\n" \
   "IhNzbM8m9Yop5w==\n" \
   "-----END CERTIFICATE-----\n" \
   "-----BEGIN CERTIFICATE-----\n" \
   "MIICRjCCAc2gAwIBAgIQC6Fa+h3foLVJRK/NJKBs7DAKBggqhkjOPQQDAzBlMQsw\n" \
   "CQYDVQQGEwJVUzEVMBMGA1UEChMMRGlnaUNlcnQgSW5jMRkwFwYDVQQLExB3d3cu\n" \
   "ZGlnaWNlcnQuY29tMSQwIgYDVQQDExtEaWdpQ2VydCBBc3N1cmVkIElEIFJvb3Qg\n" \
   "RzMwHhcNMTMwODAxMTIwMDAwWhcNMzgwMTE1MTIwMDAwWjBlMQswCQYDVQQGEwJV\n" \
   "UzEVMBMGA1UEChMMRGlnaUNlcnQgSW5jMRkwFwYDVQQLExB3d3cuZGlnaWNlcnQu\n" \
   "Y29tMSQwIgYDVQQDExtEaWdpQ2VydCBBc3N1cmVkIElEIFJvb3QgRzMwdjAQBgcq\n" \
   "hkjOPQIBBgUrgQQAIgNiAAQZ57ysRGXtzbg/WPuNsVepRC0FFfLvC/8QdJ+1YlJf\n" \
   "Zn4f5dwbRXkLzMZTCp2NXQLZqVneAlr2lSoOjThKiknGvMYDOAdfVdp+CW7if17Q\n" \
   "RSAPWXYQ1qAk8C3eNvJsKTmjQjBAMA8GA1UdEwEB/wQFMAMBAf8wDgYDVR0PAQH/\n" \
   "BAQDAgGGMB0GA1UdDgQWBBTL0L2p4ZgFUaFNN6KDec6NHSrkhDAKBggqhkjOPQQD\n" \
   "AwNnADBkAjAlpIFFAmsSS3V0T8gj43DydXLefInwz5FyYZ5eEJJZVrmDxxDnOOlY\n" \
   "JjZ91eQ0hjkCMHw2U/Aw5WJjOpnitqM7mzT6HtoQknFekROn3aRukswy1vUhZscv\n" \
   "6pZjamVFkpUBtA==\n" \
   "-----END CERTIFICATE-----\n" \
   "-----BEGIN CERTIFICATE-----\n" \
   "MIIDrzCCApegAwIBAgIQCDvgVpBCRrGhdWrJWZHHSjANBgkqhkiG9w0BAQUFADBh\n" \
   "MQswCQYDVQQGEwJVUzEVMBMGA1UEChMMRGlnaUNlcnQgSW5jMRkwFwYDVQQLExB3\n" \
   "d3cuZGlnaWNlcnQuY29tMSAwHgYDVQQDExdEaWdpQ2VydCBHbG9iYWwgUm9vdCBD\n" \
   "QTAeFw0wNjExMTAwMDAwMDBaFw0zMTExMTAwMDAwMDBaMGExCzAJBgNVBAYTAlVT\n" \
   "MRUwEwYDVQQKEwxEaWdpQ2VydCBJbmMxGTAXBgNVBAsTEHd3dy5kaWdpY2VydC5j\n" \
   "b20xIDAeBgNVBAMTF0RpZ2lDZXJ0IEdsb2JhbCBSb290IENBMIIBIjANBgkqhkiG\n" \
   "9w0BAQEFAAOCAQ8AMIIBCgKCAQEA4jvhEXLeqKTTo1eqUKKPC3eQyaKl7hLOllsB\n" \
   "CSDMAZOnTjC3U/dDxGkAV53ijSLdhwZAAIEJzs4bg7/fzTtxRuLWZscFs3YnFo97\n" \
   "nh6Vfe63SKMI2tavegw5BmV/Sl0fvBf4q77uKNd0f3p4mVmFaG5cIzJLv07A6Fpt\n" \
   "43C/dxC//AH2hdmoRBBYMql1GNXRor5H4idq9Joz+EkIYIvUX7Q6hL+hqkpMfT7P\n" \
   "T19sdl6gSzeRntwi5m3OFBqOasv+zbMUZBfHWymeMr/y7vrTC0LUq7dBMtoM1O/4\n" \
   "gdW7jVg/tRvoSSiicNoxBN33shbyTApOB6jtSj1etX+jkMOvJwIDAQABo2MwYTAO\n" \
   "BgNVHQ8BAf8EBAMCAYYwDwYDVR0TAQH/BAUwAwEB/zAdBgNVHQ4EFgQUA95QNVbR\n" \
   "TLtm8KPiGxvDl7I90VUwHwYDVR0jBBgwFoAUA95QNVbRTLtm8KPiGxvDl7I90VUw\n" \
   "DQYJKoZIhvcNAQEFBQADggEBAMucN6pIExIK+t1EnE9SsPTfrgT1eXkIoyQY/Esr\n" \
   "hMAtudXH/vTBH1jLuG2cenTnmCmrEbXjcKChzUyImZOMkXDiqw8cvpOp/2PV5Adg\n" \
   "06O/nVsJ8dWO41P0jmP6P6fbtGbfYmbW0W5BjfIttep3Sp+dWOIrWcBAI+0tKIJF\n" \
   "PnlUkiaY4IBIqDfv8NZ5YBberOgOzW6sRBc4L0na4UU+Krk2U886UAb3LujEV0ls\n" \
   "YSEY1QSteDwsOoBrp+uvFRTp2InBuThs4pFsiv9kuXclVzDAGySj4dzp30d8tbQk\n" \
   "CAUw7C29C79Fv1C5qfPrmAESrciIxpg0X40KPMbp1ZWVbd4=\n" \
   "-----END CERTIFICATE-----\n" \
   "-----BEGIN CERTIFICATE-----\n" \
   "MIIDjjCCAnagAwIBAgIQAzrx5qcRqaC7KGSxHQn65TANBgkqhkiG9w0BAQsFADBh\n" \
   "MQswCQYDVQQGEwJVUzEVMBMGA1UEChMMRGlnaUNlcnQgSW5jMRkwFwYDVQQLExB3\n" \
   "d3cuZGlnaWNlcnQuY29tMSAwHgYDVQQDExdEaWdpQ2VydCBHbG9iYWwgUm9vdCBH\n" \
   "MjAeFw0xMzA4MDExMjAwMDBaFw0zODAxMTUxMjAwMDBaMGExCzAJBgNVBAYTAlVT\n" \
   "MRUwEwYDVQQKEwxEaWdpQ2VydCBJbmMxGTAXBgNVBAsTEHd3dy5kaWdpY2VydC5j\n" \
   "b20xIDAeBgNVBAMTF0RpZ2lDZXJ0IEdsb2JhbCBSb290IEcyMIIBIjANBgkqhkiG\n" \
   "9w0BAQEFAAOCAQ8AMIIBCgKCAQEAuzfNNNx7a8myaJCtSnX/RrohCgiN9RlUyfuI\n" \
   "2/Ou8jqJkTx65qsGGmvPrC3oXgkkRLpimn7Wo6h+4FR1IAWsULecYxpsMNzaHxmx\n" \
   "1x7e/dfgy5SDN67sH0NO3Xss0r0upS/kqbitOtSZpLYl6ZtrAGCSYP9PIUkY92eQ\n" \
   "q2EGnI/yuum06ZIya7XzV+hdG82MHauVBJVJ8zUtluNJbd134/tJS7SsVQepj5Wz\n" \
   "tCO7TG1F8PapspUwtP1MVYwnSlcUfIKdzXOS0xZKBgyMUNGPHgm+F6HmIcr9g+UQ\n" \
   "vIOlCsRnKPZzFBQ9RnbDhxSJITRNrw9FDKZJobq7nMWxM4MphQIDAQABo0IwQDAP\n" \
   "BgNVHRMBAf8EBTADAQH/MA4GA1UdDwEB/wQEAwIBhjAdBgNVHQ4EFgQUTiJUIBiV\n" \
   "5uNu5g/6+rkS7QYXjzkwDQYJKoZIhvcNAQELBQADggEBAGBnKJRvDkhj6zHd6mcY\n" \
   "1Yl9PMWLSn/pvtsrF9+wX3N3KjITOYFnQoQj8kVnNeyIv/iPsGEMNKSuIEyExtv4\n" \
   "NeF22d+mQrvHRAiGfzZ0JFrabA0UWTW98kndth/Jsw1HKj2ZL7tcu7XUIOGZX1NG\n" \
   "Fdtom/DzMNU+MeKNhJ7jitralj41E6Vf8PlwUHBHQRFXGU7Aj64GxJUTFy8bJZ91\n" \
   "8rGOmaFvE7FBcf6IKshPECBV1/MUReXgRPTqh5Uykw7+U0b6LJ3/iyK5S9kJRaTe\n" \
   "pLiaWN0bfVKfjllDiIGknibVb63dDcY3fe0Dkhvld1927jyNxF1WW6LZZm6zNTfl\n" \
   "MrY=\n" \
   "-----END CERTIFICATE-----\n" \
   "-----BEGIN CERTIFICATE-----\n" \
   "MIICPzCCAcWgAwIBAgIQBVVWvPJepDU1w6QP1atFcjAKBggqhkjOPQQDAzBhMQsw\n" \
   "CQYDVQQGEwJVUzEVMBMGA1UEChMMRGlnaUNlcnQgSW5jMRkwFwYDVQQLExB3d3cu\n" \
   "ZGlnaWNlcnQuY29tMSAwHgYDVQQDExdEaWdpQ2VydCBHbG9iYWwgUm9vdCBHMzAe\n" \
   "Fw0xMzA4MDExMjAwMDBaFw0zODAxMTUxMjAwMDBaMGExCzAJBgNVBAYTAlVTMRUw\n" \
   "EwYDVQQKEwxEaWdpQ2VydCBJbmMxGTAXBgNVBAsTEHd3dy5kaWdpY2VydC5jb20x\n" \
   "IDAeBgNVBAMTF0RpZ2lDZXJ0IEdsb2JhbCBSb290IEczMHYwEAYHKoZIzj0CAQYF\n" \
   "K4EEACIDYgAE3afZu4q4C/sLfyHS8L6+c/MzXRq8NOrexpu80JX28MzQC7phW1FG\n" \
   "fp4tn+6OYwwX7Adw9c+ELkCDnOg/QW07rdOkFFk2eJ0DQ+4QE2xy3q6Ip6FrtUPO\n" \
   "Z9wj/wMco+I+o0IwQDAPBgNVHRMBAf8EBTADAQH/MA4GA1UdDwEB/wQEAwIBhjAd\n" \
   "BgNVHQ4EFgQUs9tIpPmhxdiuNkHMEWNpYim8S8YwCgYIKoZIzj0EAwMDaAAwZQIx\n" \
   "AK288mw/EkrRLTnDCgmXc/SINoyIJ7vmiI1Qhadj+Z4y3maTD/HMsQmP3Wyr+mt/\n" \
   "oAIwOWZbwmSNuJ5Q3KjVSaLtx9zRSX8XAbjIho9OjIgrqJqpisXRAL34VOKa5Vt8\n" \
   "sycX\n" \
   "-----END CERTIFICATE-----\n" \
   "-----BEGIN CERTIFICATE-----\n" \
   "MIIDxTCCAq2gAwIBAgIQAqxcJmoLQJuPC3nyrkYldzANBgkqhkiG9w0BAQUFADBs\n" \
   "MQswCQYDVQQGEwJVUzEVMBMGA1UEChMMRGlnaUNlcnQgSW5jMRkwFwYDVQQLExB3\n" \
   "d3cuZGlnaWNlcnQuY29tMSswKQYDVQQDEyJEaWdpQ2VydCBIaWdoIEFzc3VyYW5j\n" \
   "ZSBFViBSb290IENBMB4XDTA2MTExMDAwMDAwMFoXDTMxMTExMDAwMDAwMFowbDEL\n" \
   "MAkGA1UEBhMCVVMxFTATBgNVBAoTDERpZ2lDZXJ0IEluYzEZMBcGA1UECxMQd3d3\n" \
   "LmRpZ2ljZXJ0LmNvbTErMCkGA1UEAxMiRGlnaUNlcnQgSGlnaCBBc3N1cmFuY2Ug\n" \
   "RVYgUm9vdCBDQTCCASIwDQYJKoZIhvcNAQEBBQADggEPADCCAQoCggEBAMbM5XPm\n" \
   "+9S75S0tMqbf5YE/yc0lSbZxKsPVlDRnogocsF9ppkCxxLeyj9CYpKlBWTrT3JTW\n" \
   "PNt0OKRKzE0lgvdKpVMSOO7zSW1xkX5jtqumX8OkhPhPYlG++MXs2ziS4wblCJEM\n" \
   "xChBVfvLWokVfnHoNb9Ncgk9vjo4UFt3MRuNs8ckRZqnrG0AFFoEt7oT61EKmEFB\n" \
   "Ik5lYYeBQVCmeVyJ3hlKV9Uu5l0cUyx+mM0aBhakaHPQNAQTXKFx01p8VdteZOE3\n" \
   "hzBWBOURtCmAEvF5OYiiAhF8J2a3iLd48soKqDirCmTCv2ZdlYTBoSUeh10aUAsg\n" \
   "EsxBu24LUTi4S8sCAwEAAaNjMGEwDgYDVR0PAQH/BAQDAgGGMA8GA1UdEwEB/wQF\n" \
   "MAMBAf8wHQYDVR0OBBYEFLE+w2kD+L9HAdSYJhoIAu9jZCvDMB8GA1UdIwQYMBaA\n" \
   "FLE+w2kD+L9HAdSYJhoIAu9jZCvDMA0GCSqGSIb3DQEBBQUAA4IBAQAcGgaX3Nec\n" \
   "nzyIZgYIVyHbIUf4KmeqvxgydkAQV8GK83rZEWWONfqe/EW1ntlMMUu4kehDLI6z\n" \
   "eM7b41N5cdblIZQB2lWHmiRk9opmzN6cN82oNLFpmyPInngiK3BD41VHMWEZ71jF\n" \
   "hS9OMPagMRYjyOfiZRYzy78aG6A9+MpeizGLYAiJLQwGXFK3xPkKmNEVX58Svnw2\n" \
   "Yzi9RKR/5CYrCsSXaQ3pjOLAEFe4yHYSkVXySGnYvCoCWw9E1CAx2/S6cCZdkGCe\n" \
   "vEsXCS+0yx5DaMkHJ8HSXPfqIbloEpw8nL+e/IBcm2PN7EeqJSdnoDfzAIJ9VNep\n" \
   "+OkuE6N36B9K\n" \
   "-----END CERTIFICATE-----\n" \
   "-----BEGIN CERTIFICATE-----\n" \
   "MIIFkDCCA3igAwIBAgIQBZsbV56OITLiOQe9p3d1XDANBgkqhkiG9w0BAQwFADBi\n" \
   "MQswCQYDVQQGEwJVUzEVMBMGA1UEChMMRGlnaUNlcnQgSW5jMRkwFwYDVQQLExB3\n" \
   "d3cuZGlnaWNlcnQuY29tMSEwHwYDVQQDExhEaWdpQ2VydCBUcnVzdGVkIFJvb3Qg\n" \
   "RzQwHhcNMTMwODAxMTIwMDAwWhcNMzgwMTE1MTIwMDAwWjBiMQswCQYDVQQGEwJV\n" \
   "UzEVMBMGA1UEChMMRGlnaUNlcnQgSW5jMRkwFwYDVQQLExB3d3cuZGlnaWNlcnQu\n" \
   "Y29tMSEwHwYDVQQDExhEaWdpQ2VydCBUcnVzdGVkIFJvb3QgRzQwggIiMA0GCSqG\n" \
   "SIb3DQEBAQUAA4ICDwAwggIKAoICAQC/5pBzaN675F1KPDAiMGkz7MKnJS7JIT3y\n" \
   "ithZwuEppz1Yq3aaza57G4QNxDAf8xukOBbrVsaXbR2rsnnyyhHS5F/WBTxSD1If\n" \
   "xp4VpX6+n6lXFllVcq9ok3DCsrp1mWpzMpTREEQQLt+C8weE5nQ7bXHiLQwb7iDV\n" \
   "ySAdYyktzuxeTsiT+CFhmzTrBcZe7FsavOvJz82sNEBfsXpm7nfISKhmV1efVFiO\n" \
   "DCu3T6cw2Vbuyntd463JT17lNecxy9qTXtyOj4DatpGYQJB5w3jHtrHEtWoYOAMQ\n" \
   "jdjUN6QuBX2I9YI+EJFwq1WCQTLX2wRzKm6RAXwhTNS8rhsDdV14Ztk6MUSaM0C/\n" \
   "CNdaSaTC5qmgZ92kJ7yhTzm1EVgX9yRcRo9k98FpiHaYdj1ZXUJ2h4mXaXpI8OCi\n" \
   "EhtmmnTK3kse5w5jrubU75KSOp493ADkRSWJtppEGSt+wJS00mFt6zPZxd9LBADM\n" \
   "fRyVw4/3IbKyEbe7f/LVjHAsQWCqsWMYRJUadmJ+9oCw++hkpjPRiQfhvbfmQ6QY\n" \
   "uKZ3AeEPlAwhHbJUKSWJbOUOUlFHdL4mrLZBdd56rF+NP8m800ERElvlEFDrMcXK\n" \
   "chYiCd98THU/Y+whX8QgUWtvsauGi0/C1kVfnSD8oR7FwI+isX4KJpn15GkvmB0t\n" \
   "9dmpsh3lGwIDAQABo0IwQDAPBgNVHRMBAf8EBTADAQH/MA4GA1UdDwEB/wQEAwIB\n" \
   "hjAdBgNVHQ4EFgQU7NfjgtJxXWRM3y5nP+e6mK4cD08wDQYJKoZIhvcNAQEMBQAD\n" \
   "ggIBALth2X2pbL4XxJEbw6GiAI3jZGgPVs93rnD5/ZpKmbnJeFwMDF/k5hQpVgs2\n" \
   "SV1EY+CtnJYYZhsjDT156W1r1lT40jzBQ0CuHVD1UvyQO7uYmWlrx8GnqGikJ9yd\n" \
   "+SeuMIW59mdNOj6PWTkiU0TryF0Dyu1Qen1iIQqAyHNm0aAFYF/opbSnr6j3bTWc\n" \
   "fFqK1qI4mfN4i/RN0iAL3gTujJtHgXINwBQy7zBZLq7gcfJW5GqXb5JQbZaNaHqa\n" \
   "sjYUegbyJLkJEVDXCLG4iXqEI2FCKeWjzaIgQdfRnGTZ6iahixTXTBmyUEFxPT9N\n" \
   "cCOGDErcgdLMMpSEDQgJlxxPwO5rIHQw0uA5NBCFIRUBCOhVMt5xSdkoF1BN5r5N\n" \
   "0XWs0Mr7QbhDparTwwVETyw2m+L64kW4I1NsBm9nVX9GtUw/bihaeSbSpKhil9Ie\n" \
   "4u1Ki7wb/UdKDd9nZn6yW0HQO+T0O/QEY+nvwlQAUaCKKsnOeMzV6ocEGLPOr0mI\n" \
   "r/OSmbaz5mEP0oUA51Aa5BuVnRmhuZyxm7EAHu/QD09CbMkKvO5D+jpxpchNJqU1\n" \
   "/YldvIViHTLSoCtU7ZpXwdv6EM8Zt4tKG48BtieVU+i2iW1bvGjUI+iLUaJW+fCm\n" \
   "gKDWHrO8Dw9TdSmq6hN35N6MgSGtBxBHEa2HPQfRdbzP82Z+\n" \
   "-----END CERTIFICATE-----\n" \
   "-----BEGIN CERTIFICATE-----\n" \
   "MIIDSjCCAjKgAwIBAgIQRK+wgNajJ7qJMDmGLvhAazANBgkqhkiG9w0BAQUFADA/\n" \
   "MSQwIgYDVQQKExtEaWdpdGFsIFNpZ25hdHVyZSBUcnVzdCBDby4xFzAVBgNVBAMT\n" \
   "DkRTVCBSb290IENBIFgzMB4XDTAwMDkzMDIxMTIxOVoXDTIxMDkzMDE0MDExNVow\n" \
   "PzEkMCIGA1UEChMbRGlnaXRhbCBTaWduYXR1cmUgVHJ1c3QgQ28uMRcwFQYDVQQD\n" \
   "Ew5EU1QgUm9vdCBDQSBYMzCCASIwDQYJKoZIhvcNAQEBBQADggEPADCCAQoCggEB\n" \
   "AN+v6ZdQCINXtMxiZfaQguzH0yxrMMpb7NnDfcdAwRgUi+DoM3ZJKuM/IUmTrE4O\n" \
   "rz5Iy2Xu/NMhD2XSKtkyj4zl93ewEnu1lcCJo6m67XMuegwGMoOifooUMM0RoOEq\n" \
   "OLl5CjH9UL2AZd+3UWODyOKIYepLYYHsUmu5ouJLGiifSKOeDNoJjj4XLh7dIN9b\n" \
   "xiqKqy69cK3FCxolkHRyxXtqqzTWMIn/5WgTe1QLyNau7Fqckh49ZLOMxt+/yUFw\n" \
   "7BZy1SbsOFU5Q9D8/RhcQPGX69Wam40dutolucbY38EVAjqr2m7xPi71XAicPNaD\n" \
   "aeQQmxkqtilX4+U9m5/wAl0CAwEAAaNCMEAwDwYDVR0TAQH/BAUwAwEB/zAOBgNV\n" \
   "HQ8BAf8EBAMCAQYwHQYDVR0OBBYEFMSnsaR7LHH62+FLkHX/xBVghYkQMA0GCSqG\n" \
   "SIb3DQEBBQUAA4IBAQCjGiybFwBcqR7uKGY3Or+Dxz9LwwmglSBd49lZRNI+DT69\n" \
   "ikugdB/OEIKcdBodfpga3csTS7MgROSR6cz8faXbauX+5v3gTt23ADq1cEmv8uXr\n" \
   "AvHRAosZy5Q6XkjEGB5YGV8eAlrwDPGxrancWYaLbumR9YbK+rlmM6pZW87ipxZz\n" \
   "R8srzJmwN0jP41ZL9c8PDHIyh8bwRLtTcm1D9SZImlJnt1ir/md2cXjbDaJWFBM5\n" \
   "JDGFoqgCWjBH4d1QB7wCCZAA62RjYJsWvIjJEubSfZGL+T0yjWW06XyxV3bqxbYo\n" \
   "Ob8VZRzI9neWagqNdwvYkQsEjgfbKbYK7p2CNTUQ\n" \
   "-----END CERTIFICATE-----\n" \
   "-----BEGIN CERTIFICATE-----\n" \
   "MIIDOzCCAiOgAwIBAgIRANAeRlAAACmMAAAAAgAAAAIwDQYJKoZIhvcNAQEFBQAw\n" \
   "PzEkMCIGA1UEChMbRGlnaXRhbCBTaWduYXR1cmUgVHJ1c3QgQ28uMRcwFQYDVQQD\n" \
   "Ew5EU1QgUm9vdCBDQSBYNDAeFw0wMDA5MTMwNjIyNTBaFw0yMDA5MTMwNjIyNTBa\n" \
   "MD8xJDAiBgNVBAoTG0RpZ2l0YWwgU2lnbmF0dXJlIFRydXN0IENvLjEXMBUGA1UE\n" \
   "AxMORFNUIFJvb3QgQ0EgWDQwggEiMA0GCSqGSIb3DQEBAQUAA4IBDwAwggEKAoIB\n" \
   "AQCthX3OFEYY8gSeIYur0O4ypOT68HnDrjLfIutL5PZHRwQGjzCPb9PFo/ihboJ8\n" \
   "RvfGhBAqpQCo47zwYEhpWm1jB+L/OE/dBBiyn98krfU2NiBKSom2J58RBeAwHGEy\n" \
   "cO+lewyjVvbDDLUy4CheY059vfMjPAftCRXjqSZIolQb9FdPcAoa90mFwB7rKniE\n" \
   "J7vppdrUScSS0+eBrHSUPLdvwyn4RGp+lSwbWYcbg5EpSpE0GRJdchic0YDjvIoC\n" \
   "YHpe7Rkj93PYRTQyU4bhC88ck8tMqbvRYqMRqR+vobbkrj5LLCOQCHV5WEoxWh+0\n" \
   "E2SpIFe7RkV++MmpIAc0h1tZAgMBAAGjMjAwMA8GA1UdEwEB/wQFMAMBAf8wHQYD\n" \
   "VR0OBBYEFPCD6nPIP1ubWzdf9UyPWvf0hki9MA0GCSqGSIb3DQEBBQUAA4IBAQCE\n" \
   "G85wl5eEWd7adH6XW/ikGN5salvpq/Fix6yVTzE6CrhlP5LBdkf6kx1bSPL18M45\n" \
   "g0rw2zA/MWOhJ3+S6U+BE0zPGCuu8YQaZibR7snm3HiHUaZNMu5c8D0x0bcMxDjY\n" \
   "AVVcHCoNiL53Q4PLW27nbY6wwG0ffFKmgV3blxrYWfuUDgGpyPwHwkfVFvz9qjaV\n" \
   "mf12VJffL6W8omBPtgteb6UaT/k1oJ7YI0ldGf+ngpVbRhD+LC3cUtT6GO/BEPZu\n" \
   "8YTV/hbiDH5v3khVqMIeKT6o8IuXGG7F6a6vKwP1F1FwTXf4UC/ivhme7vdUH7B/\n" \
   "Vv4AEbT8dNfEeFxrkDbh\n" \
   "-----END CERTIFICATE-----\n" \
   "-----BEGIN CERTIFICATE-----\n" \
   "MIIGSzCCBDOgAwIBAgIIamg+nFGby1MwDQYJKoZIhvcNAQELBQAwgbIxCzAJBgNV\n" \
   "BAYTAlRSMQ8wDQYDVQQHDAZBbmthcmExQDA+BgNVBAoMN0UtVHXEn3JhIEVCRyBC\n" \
   "aWxpxZ9pbSBUZWtub2xvamlsZXJpIHZlIEhpem1ldGxlcmkgQS7Fni4xJjAkBgNV\n" \
   "BAsMHUUtVHVncmEgU2VydGlmaWthc3lvbiBNZXJrZXppMSgwJgYDVQQDDB9FLVR1\n" \
   "Z3JhIENlcnRpZmljYXRpb24gQXV0aG9yaXR5MB4XDTEzMDMwNTEyMDk0OFoXDTIz\n" \
   "MDMwMzEyMDk0OFowgbIxCzAJBgNVBAYTAlRSMQ8wDQYDVQQHDAZBbmthcmExQDA+\n" \
   "BgNVBAoMN0UtVHXEn3JhIEVCRyBCaWxpxZ9pbSBUZWtub2xvamlsZXJpIHZlIEhp\n" \
   "em1ldGxlcmkgQS7Fni4xJjAkBgNVBAsMHUUtVHVncmEgU2VydGlmaWthc3lvbiBN\n" \
   "ZXJrZXppMSgwJgYDVQQDDB9FLVR1Z3JhIENlcnRpZmljYXRpb24gQXV0aG9yaXR5\n" \
   "MIICIjANBgkqhkiG9w0BAQEFAAOCAg8AMIICCgKCAgEA4vU/kwVRHoViVF56C/UY\n" \
   "B4Oufq9899SKa6VjQzm5S/fDxmSJPZQuVIBSOTkHS0vdhQd2h8y/L5VMzH2nPbxH\n" \
   "D5hw+IyFHnSOkm0bQNGZDbt1bsipa5rAhDGvykPL6ys06I+XawGb1Q5KCKpbknSF\n" \
   "Q9OArqGIW66z6l7LFpp3RMih9lRozt6Plyu6W0ACDGQXwLWTzeHxE2bODHnv0ZEo\n" \
   "q1+gElIwcxmOj+GMB6LDu0rw6h8VqO4lzKRG+Bsi77MOQ7osJLjFLFzUHPhdZL3D\n" \
   "k14opz8n8Y4e0ypQBaNV2cvnOVPAmJ6MVGKLJrD3fY185MaeZkJVgkfnsliNZvcH\n" \
   "fC425lAcP9tDJMW/hkd5s3kc91r0E+xs+D/iWR+V7kI+ua2oMoVJl0b+SzGPWsut\n" \
   "dEcf6ZG33ygEIqDUD13ieU/qbIWGvaimzuT6w+Gzrt48Ue7LE3wBf4QOXVGUnhMM\n" \
   "ti6lTPk5cDZvlsouDERVxcr6XQKj39ZkjFqzAQqptQpHF//vkUAqjqFGOjGY5RH8\n" \
   "zLtJVor8udBhmm9lbObDyz51Sf6Pp+KJxWfXnUYTTjF2OySznhFlhqt/7x3U+Lzn\n" \
   "rFpct1pHXFXOVbQicVtbC/DP3KBhZOqp12gKY6fgDT+gr9Oq0n7vUaDmUStVkhUX\n" \
   "U8u3Zg5mTPj5dUyQ5xJwx0UCAwEAAaNjMGEwHQYDVR0OBBYEFC7j27JJ0JxUeVz6\n" \
   "Jyr+zE7S6E5UMA8GA1UdEwEB/wQFMAMBAf8wHwYDVR0jBBgwFoAULuPbsknQnFR5\n" \
   "XPonKv7MTtLoTlQwDgYDVR0PAQH/BAQDAgEGMA0GCSqGSIb3DQEBCwUAA4ICAQAF\n" \
   "Nzr0TbdF4kV1JI+2d1LoHNgQk2Xz8lkGpD4eKexd0dCrfOAKkEh47U6YA5n+KGCR\n" \
   "HTAduGN8qOY1tfrTYXbm1gdLymmasoR6d5NFFxWfJNCYExL/u6Au/U5Mh/jOXKqY\n" \
   "GwXgAEZKgoClM4so3O0409/lPun++1ndYYRP0lSWE2ETPo+Aab6TR7U1Q9Jauz1c\n" \
   "77NCR807VRMGsAnb/WP2OogKmW9+4c4bU2pEZiNRCHu8W1Ki/QY3OEBhj0qWuJA3\n" \
   "+GbHeJAAFS6LrVE1Uweoa2iu+U48BybNCAVwzDk/dr2l02cmAYamU9JgO3xDf1WK\n" \
   "vJUawSg5TB9D0pH0clmKuVb8P7Sd2nCcdlqMQ1DujjByTd//SffGqWfZbawCEeI6\n" \
   "FiWnWAjLb1NBnEg4R2gz0dfHj9R0IdTDBZB6/86WiLEVKV0jq9BgoRJP3vQXzTLl\n" \
   "yb/IQ639Lo7xr+L0mPoSHyDYwKcMhcWQ9DstliaxLL5Mq+ux0orJ23gTDx4JnW2P\n" \
   "AJ8C2sH6H3p6CcRK5ogql5+Ji/03X186zjhZhkuvcQu02PJwT58yE+Owp1fl2tpD\n" \
   "y4Q08ijE6m30Ku/Ba3ba+367hTzSU8JNvnHhRdH9I2cNE3X7z2VnIp2usAnRCf8d\n" \
   "NL/+I5c30jn6PQ0GC7TbO6Orb1wdtn7os4I07QZcJA==\n" \
   "-----END CERTIFICATE-----\n" \
   "-----BEGIN CERTIFICATE-----\n" \
   "MIIE5zCCA8+gAwIBAgIBADANBgkqhkiG9w0BAQUFADCBjTELMAkGA1UEBhMCQ0Ex\n" \
   "EDAOBgNVBAgTB09udGFyaW8xEDAOBgNVBAcTB1Rvcm9udG8xHTAbBgNVBAoTFEVj\n" \
   "aG93b3J4IENvcnBvcmF0aW9uMR8wHQYDVQQLExZDZXJ0aWZpY2F0aW9uIFNlcnZp\n" \
   "Y2VzMRowGAYDVQQDExFFY2hvd29yeCBSb290IENBMjAeFw0wNTEwMDYxMDQ5MTNa\n" \
   "Fw0zMDEwMDcxMDQ5MTNaMIGNMQswCQYDVQQGEwJDQTEQMA4GA1UECBMHT250YXJp\n" \
   "bzEQMA4GA1UEBxMHVG9yb250bzEdMBsGA1UEChMURWNob3dvcnggQ29ycG9yYXRp\n" \
   "b24xHzAdBgNVBAsTFkNlcnRpZmljYXRpb24gU2VydmljZXMxGjAYBgNVBAMTEUVj\n" \
   "aG93b3J4IFJvb3QgQ0EyMIIBIDANBgkqhkiG9w0BAQEFAAOCAQ0AMIIBCAKCAQEA\n" \
   "utU/5BkV15UBf+s+JQruKQxr77s3rjp/RpOtmhHILIiO5gsEWP8MMrfrVEiidjI6\n" \
   "Qh6ans0KAWc2Dw0/j4qKAQzOSyAZgjcdypNTBZ7muv212DA2Pu41rXqwMrlBrVi/\n" \
   "KTghfdLlNRu6JrC5y8HarrnRFSKF1Thbzz921kLDRoCi+FVs5eVuK5LvIfkhNAqA\n" \
   "byrTgO3T9zfZgk8upmEkANPDL1+8y7dGPB/d6lk0I5mv8PESKX02TlvwgRSIiTHR\n" \
   "k8++iOPLBWlGp7ZfqTEXkPUZhgrQQvxcrwCUo6mk8TqgxCDP5FgPoHFiPLef5szP\n" \
   "ZLBJDWp7GLyE1PmkQI6WiwIBA6OCAVAwggFMMA8GA1UdEwEB/wQFMAMBAf8wCwYD\n" \
   "VR0PBAQDAgEGMB0GA1UdDgQWBBQ74YEboKs/OyGC1eISrq5QqxSlEzCBugYDVR0j\n" \
   "BIGyMIGvgBQ74YEboKs/OyGC1eISrq5QqxSlE6GBk6SBkDCBjTELMAkGA1UEBhMC\n" \
   "Q0ExEDAOBgNVBAgTB09udGFyaW8xEDAOBgNVBAcTB1Rvcm9udG8xHTAbBgNVBAoT\n" \
   "FEVjaG93b3J4IENvcnBvcmF0aW9uMR8wHQYDVQQLExZDZXJ0aWZpY2F0aW9uIFNl\n" \
   "cnZpY2VzMRowGAYDVQQDExFFY2hvd29yeCBSb290IENBMoIBADBQBgNVHSAESTBH\n" \
   "MEUGCysGAQQB+REKAQMBMDYwNAYIKwYBBQUHAgEWKGh0dHA6Ly93d3cuZWNob3dv\n" \
   "cnguY29tL2NhL3Jvb3QyL2Nwcy5wZGYwDQYJKoZIhvcNAQEFBQADggEBAG+nrPi/\n" \
   "0RpfEzrj02C6JGPUar4nbjIhcY6N7DWNeqBoUulBSIH/PYGNHYx7/lnJefiixPGE\n" \
   "7TQ5xPgElxb9bK8zoAApO7U33OubqZ7M7DlHnFeCoOoIAZnG1kuwKwD5CXKB2a74\n" \
   "HzcqNnFW0IsBFCYqrVh/rQgJOzDA8POGbH0DeD0xjwBBooAolkKT+7ZItJF1Pb56\n" \
   "QpDL9G+16F7GkmnKlAIYT3QTS3yFGYChnJcd+6txUPhKi9sSOOmAIaKHnkH9Scz+\n" \
   "A2cSi4A3wUYXVatuVNHpRb2lygfH3SuCX9MU8Ure3zBlSU1LALtMqI4JmcQmQpIq\n" \
   "zIzvO2jHyu9PQqo=\n" \
   "-----END CERTIFICATE-----\n" \
   "-----BEGIN CERTIFICATE-----\n" \
   "MIIEAzCCAuugAwIBAgIQVID5oHPtPwBMyonY43HmSjANBgkqhkiG9w0BAQUFADB1\n" \
   "MQswCQYDVQQGEwJFRTEiMCAGA1UECgwZQVMgU2VydGlmaXRzZWVyaW1pc2tlc2t1\n" \
   "czEoMCYGA1UEAwwfRUUgQ2VydGlmaWNhdGlvbiBDZW50cmUgUm9vdCBDQTEYMBYG\n" \
   "CSqGSIb3DQEJARYJcGtpQHNrLmVlMCIYDzIwMTAxMDMwMTAxMDMwWhgPMjAzMDEy\n" \
   "MTcyMzU5NTlaMHUxCzAJBgNVBAYTAkVFMSIwIAYDVQQKDBlBUyBTZXJ0aWZpdHNl\n" \
   "ZXJpbWlza2Vza3VzMSgwJgYDVQQDDB9FRSBDZXJ0aWZpY2F0aW9uIENlbnRyZSBS\n" \
   "b290IENBMRgwFgYJKoZIhvcNAQkBFglwa2lAc2suZWUwggEiMA0GCSqGSIb3DQEB\n" \
   "AQUAA4IBDwAwggEKAoIBAQDIIMDs4MVLqwd4lfNE7vsLDP90jmG7sWLqI9iroWUy\n" \
   "euuOF0+W2Ap7kaJjbMeMTC55v6kF/GlclY1i+blw7cNRfdCT5mzrMEvhvH2/UpvO\n" \
   "bntl8jixwKIy72KyaOBhU8E2lf/slLo2rpwcpzIP5Xy0xm90/XsY6KxX7QYgSzIw\n" \
   "WFv9zajmofxwvI6Sc9uXp3whrj3B9UiHbCe9nyV0gVWw93X2PaRka9ZP585ArQ/d\n" \
   "MtO8ihJTmMmJ+xAdTX7Nfh9WDSFwhfYggx/2uh8Ej+p3iDXE/+pOoYtNP2MbRMNE\n" \
   "1CV2yreN1x5KZmTNXMWcg+HCCIia7E6j8T4cLNlsHaFLAgMBAAGjgYowgYcwDwYD\n" \
   "VR0TAQH/BAUwAwEB/zAOBgNVHQ8BAf8EBAMCAQYwHQYDVR0OBBYEFBLyWj7qVhy/\n" \
   "zQas8fElyalL1BSZMEUGA1UdJQQ+MDwGCCsGAQUFBwMCBggrBgEFBQcDAQYIKwYB\n" \
   "BQUHAwMGCCsGAQUFBwMEBggrBgEFBQcDCAYIKwYBBQUHAwkwDQYJKoZIhvcNAQEF\n" \
   "BQADggEBAHv25MANqhlHt01Xo/6tu7Fq1Q+e2+RjxY6hUFaTlrg4wCQiZrxTFGGV\n" \
   "v9DHKpY5P30osxBAIWrEr7BSdxjhlthWXePdNl4dp1BUoMUq5KqMlIpPnTX/dqQG\n" \
   "E5Gion0ARD9V04I8GtVbvFZMIi5GQ4okQC3zErg7cBqklrkar4dBGmoYDQZPxz5u\n" \
   "uSlNDUmJEYcyW+ZLBMjkXOZ0c5RdFpgTlf7727FE5TpwrDdr5rMzcijJs1eg9gIW\n" \
   "iAYLtqZLICjU3j2LrTcFU3T+bsy8QxdxXvnFzBqpYe73dgzzcvRyrc9yAjYHR8/v\n" \
   "GVCJYMzpJJUPwssd8m92kMfMdcGWxZ0=\n" \
   "-----END CERTIFICATE-----\n" \
   "-----BEGIN CERTIFICATE-----\n" \
   "MIIEkTCCA3mgAwIBAgIERWtQVDANBgkqhkiG9w0BAQUFADCBsDELMAkGA1UEBhMC\n" \
   "VVMxFjAUBgNVBAoTDUVudHJ1c3QsIEluYy4xOTA3BgNVBAsTMHd3dy5lbnRydXN0\n" \
   "Lm5ldC9DUFMgaXMgaW5jb3Jwb3JhdGVkIGJ5IHJlZmVyZW5jZTEfMB0GA1UECxMW\n" \
   "KGMpIDIwMDYgRW50cnVzdCwgSW5jLjEtMCsGA1UEAxMkRW50cnVzdCBSb290IENl\n" \
   "cnRpZmljYXRpb24gQXV0aG9yaXR5MB4XDTA2MTEyNzIwMjM0MloXDTI2MTEyNzIw\n" \
   "NTM0MlowgbAxCzAJBgNVBAYTAlVTMRYwFAYDVQQKEw1FbnRydXN0LCBJbmMuMTkw\n" \
   "NwYDVQQLEzB3d3cuZW50cnVzdC5uZXQvQ1BTIGlzIGluY29ycG9yYXRlZCBieSBy\n" \
   "ZWZlcmVuY2UxHzAdBgNVBAsTFihjKSAyMDA2IEVudHJ1c3QsIEluYy4xLTArBgNV\n" \
   "BAMTJEVudHJ1c3QgUm9vdCBDZXJ0aWZpY2F0aW9uIEF1dGhvcml0eTCCASIwDQYJ\n" \
   "KoZIhvcNAQEBBQADggEPADCCAQoCggEBALaVtkNC+sZtKm9I35RMOVcF7sN5EUFo\n" \
   "Nu3s/poBj6E4KPz3EEZmLk0eGrEaTsbRwJWIsMn/MYszA9u3g3s+IIRe7bJWKKf4\n" \
   "4LlAcTfFy0cOlypowCKVYhXbR9n10Cv/gkvJrT7eTNuQgFA/CYqEAOwwCj0Yzfv9\n" \
   "KlmaI5UXLEWeH25DeW0MXJj+SKfFI0dcXv1u5x609mhF0YaDW6KKjbHjKYD+JXGI\n" \
   "rb68j6xSlkuqUY3kEzEZ6E5Nn9uss2rVvDlUccp6en+Q3X0dgNmBu1kmwhH+5pPi\n" \
   "94DkZfs0Nw4pgHBNrziGLp5/V6+eF67rHMsoIV+2HNjnogQi+dPa2MsCAwEAAaOB\n" \
   "sDCBrTAOBgNVHQ8BAf8EBAMCAQYwDwYDVR0TAQH/BAUwAwEB/zArBgNVHRAEJDAi\n" \
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
void loop() {
  int stat;
  
  //L2_RED(); delay(500); L2_BLACK(); delay(500);
  if(RETRIEVINGSTREAM == 1) {
    Serial.printf("Retrieving data...\n");
    yield();
    if(client.available()) {
      if(strlen(outstream) < 8191) {
        char c = client.read();
        outstream[strlen(outstream)] = c;
        outstream[strlen(outstream)+1] = 0x0;
      }
    }
    else {
      RETRIEVINGSTREAM = 0;
      client.stop();
      BUFFERSREADY = 1; 
      Serial.printf("Data read complete.\n");
    }
  }

  if(RETRIEVINGHEADERS == 1) {
    Serial.printf("Retrieving headers...\n");
    yield();
    if(!client.connected()) {
      RETRIEVINGHEADERS = 0;    
      RETRIEVINGSTREAM = 0;
      Serial.printf("client disconnect during header retrieval\n");
    }
    yield();
    String line = client.readStringUntil('\n');
    if(line == "\r") {
      RETRIEVINGHEADERS = 0;    
      RETRIEVINGSTREAM = 1;
    }
    strcat(headers,line.c_str());
    strcat(headers,"\n");
  }

  if(INVOKINGGET == 1) {
    Serial.printf("Invoking GET...\n");
    INVOKINGGET = 0;
    yield();
    client.printf("GET %s HTTP/1.0\n", getBuffer);
    client.printf("Connection: close\n");
    client.printf("\n");
    BUFFERSREADY = 0;
    RETRIEVINGHEADERS = 1;
    RETRIEVINGSTREAM = 0;
    headers[0] = 0x0;
    outstream[0] = 0x0;
  }

  if(strlen(getBuffer) > 0 && SETTINGCACERT == 0) {
    strcpy(server, getBuffer);
    String s(server);
    s.trim();
    s.replace("https://","");
    s.replace("http://","");
          
    if(s.indexOf("/") > 0) {
      s = s.substring(0,s.indexOf("/"));
    }
    else { 
        if(s.indexOf(" ") > 0) {
          s = s.substring(0,s.indexOf(" "));
        }
    }
    s.trim();
    strcpy(server, s.c_str());
    Serial.printf("Connecting to server %s...\n", server);
    yield();
    if(!client.connect(server, 80)) {
      Serial.printf("Connection failed requesting %s\n", getBuffer);
      getBuffer[0] = 0x0;
      strcpy(outBuffer,"CONNECTION FAILED");
    }
    else {
      INVOKINGGET = 1;
    }
  }

  if(SETTINGCACERT == 1) {
    Serial.printf("Setting Root CA Cert...\n");
    client.setCACert(globalsign_ca);
    SETTINGCACERT = 0;
  }

  if(WAITINGFORCONNECT == 1) {
    yield();
    wl_status_t t = WiFi.status();
    if(t == WL_CONNECTED) {
      WAITINGFORCONNECT = 0;
      SETTINGCACERT = 1;
    }
  }

  if(CONNECTING == 1) {
    CONNECTING = 0;
    WiFi.disconnect(true);
    delay(500);
    Serial.printf("WiFi.begin(%s,%s)...\n", ssid, password);
    //detachTRS80Interrupts();
    WiFi.begin(ssid, password);
    WAITINGFORCONNECT = 1;
  }
}
