calphool/TRS80MXS/teensy/TeensyDiskEmu/SDCardFunctions.ino

SdFatSdioEX sdEx;

extern drivesettings Drives[4];


bool initSD() {
  if (!sdEx.begin()) {             // couldn't establish SD card connection
        fatalError((char*)"ERROR:  Unable to open SdFatSdioEX object.\n");
        sdEx.initErrorHalt("SdFatSdioEX begin() failed");
        return false;
  }  
  return true;
}


void catalog() {
  File file;
  String workStrm;
  StringStream stream(workStrm); // set up string stream to capture SD card directory

  if(!initSD()) return;
    
  sdEx.chvol();
  sdEx.vwd()->rewind();
  while (file.openNext(sdEx.vwd(), O_RDONLY)) {
      if(!file.isHidden()) {
          file.printName(&stream);
          if (file.isDir()) {
           stream.write('/');
          }
          stream.flush();
          p((char*)"%s\n",workStrm.c_str());
          workStrm = "";
      }
      file.close();
  }
}


char buffer[255];

char* getImageAt(int ix) {
  int iCtr = 0;
  File file;
  String workStrm;
  StringStream stream(workStrm); // set up string stream to capture SD card directory

  if(!initSD()) return NULL;
    
  sdEx.chvol();
  sdEx.vwd()->rewind();
  while (file.openNext(sdEx.vwd(), O_RDONLY)) {
      if(!file.isHidden()) {
          file.printName(&stream);
          if (!file.isDir()) {
            stream.flush();
            strcpy(buffer, workStrm.c_str());
            if(ix == iCtr) {
              file.close();
              return buffer;
            }
            iCtr++;
            workStrm = "";
          }
      }
      file.close();
  }

  return NULL;
}


int getImageCount() {
  int iCtr = 0;
  File file;

  if(!initSD()) return 0;
    
  sdEx.chvol();
  sdEx.vwd()->rewind();
  while (file.openNext(sdEx.vwd(), O_RDONLY)) {
      if(!file.isHidden()) {
          if (!file.isDir()) {
            iCtr++;
          }
      }
      file.close();
  }
  return iCtr;
}


bool delFile(char* fileName) {
  if(!initSD()) return false;

  return sdEx.remove(fileName);
}

bool fileExists(char* fileName) {
  File file;
  if(!initSD()) return true;
  sdEx.chvol();

  if(file.open(fileName, O_RDONLY)) {
    file.close();
    return true;
  }
  return false;
}

void viewFile(char* fileName, bool bViewHex) {
  File file;
  char ch;

  if(!initSD()) return;
  sdEx.chvol();
  if(!file.open(fileName, O_RDONLY)) {
        fatalError((char*)"ERROR:  Unable to open file: %s\n",fileName);
        return;
  }

  int iCtr = 1;
  while(file.available()) {
    if(file.read(&ch, 1) == 1) {
      if(bViewHex) {
        p((char*)"%02X ",ch);
        if(iCtr % 40 == 0) 
           p((char*)"\n");
      }
      else {
        p((char*)"%c",ch);
      }
      iCtr++;
    }
  }
  

  file.close();
}


void appendBufferToFile(char* buf, int iSize, char* fileName) {
  File file;
  
  if(!initSD()) return;

  sdEx.chvol();
  if(!file.open(fileName, O_CREAT | O_WRITE | O_AT_END)) {
        fatalError((char*)"ERROR:  Unable to open file: %s\n",fileName);
        return;
  }

  if (iSize != file.write(buf, iSize)) {
        fatalError((char*)"ERROR:  Unable to write to file: %s\n",fileName);
        file.close();
        return;    
  }

  file.close();
}



int openDiskFileByName(String sFileName, int iDriveNum) {
  File file;
  String workStrm;
  boolean bLoaded = false;
  
  StringStream stream(workStrm); // set up string stream to capture SD card directory

  if(!initSD()) return -1;

  sdEx.chvol();
  sdEx.vwd()->rewind();
  while (file.openNext(sdEx.vwd(), O_RDONLY)) {
      if(!file.isHidden()) {
          file.printName(&stream);
          if (file.isDir()) {
           stream.write('/');
          }
          stream.flush();
          if(workStrm.equalsIgnoreCase(sFileName)) {
             p((char*)"Opening disk %d file: ",iDriveNum);
             p((char*)workStrm.c_str());
             Drives[iDriveNum].diskFile = sdEx.open(workStrm.c_str(), O_RDWR);
             if(!Drives[iDriveNum].diskFile) {
                fatalError((char*)"ERROR:  Unable to open file\n");
                file.close();
                return -1;
             }
             else {
              p((char*)"\n%d bytes in file.\n",Drives[iDriveNum].diskFile.available());
              bLoaded = true;
             }
          }
          workStrm = "";
      }
      file.close();
  }

  if(bLoaded == true)
      Drives[iDriveNum].sDiskFileName = sFileName;
  else {
      fatalError((char*)"ERROR: Unable to load file %s.\n",sFileName.c_str());
      return -1;
  }

  return 0;
}
